paulovitorbal/coruja_gps/revisao_tecnica.md

# 🔍 Revisão Técnica — Pontos que Necessitam Correção

**Projeto:** Detector de Radares GPS Inteligente (Raspberry Pi Pico 2 W)
**Documentos revisados:** `bom_schematic.md`, `requirements.md`
**Data da revisão:** 2026-09-15
**Contexto:** projeto pessoal de estudo — aperfeiçoamento de habilidades em embarcados.

## Sumário por severidade

> ✅ **2026-09-15 — Revisão 2 aplicada aos documentos de origem.** `requirements.md` e
> `bom_schematic.md` foram atualizados com todos os itens abaixo. Os originais estão em
> `requirements.md.bak` e `bom_schematic.md.bak`. O que resta não é mais *documentar* —
> é **implementar, medir e confirmar as suposições**.

| Severidade | Documentado | Pendente de bancada | Significado |
| :--- | :---: | :---: | :--- |
| 🔴 **Bloqueador** | 8 de 8 | — *(R-05 medido em 19/09)* | Queima componente, ou o requisito não roda no hardware. R-05, R-06, R-14 e R-21 fechados. |
| 🟠 **Relevante** | 28 de 28 | 2 medições (R-13, R-17) + 2 inspeções (display, serigrafia do GPS) + 1 julgamento subjetivo (R-32, audibilidade) | Circuito liga, comportamento sai errado ou falha em silêncio. **R-22 a R-26**. |
| 🟡 **Lacuna** | 9 de 9 | — | Requisito que não existia. |
| ⚪ **Editorial** | 5 de 5 | — | Erro de texto ou numeração. |

### ⏳ O que continua aberto

**📐 Medições de bancada** — as únicas coisas que exigem o hardware na mão:

| Item | O que medir | Por quê |
| :--- | :--- | :--- |
| ~~**R-05**~~ | ✅ **CONCLUÍDO em duas partes.** LED em 2026-09-19: resistores 330/470/150 Ω, âmbar 19,6% de verde, rosa 15,7% de azul. **Tela em 2026-09-29:** as três matizes se distinguem a 5%, mas a barra some por falta de área — piso físico sobe de 5% para 10%, e a escala exposta passa a 0–100% com o piso escondido. **Reverificado:** a 0% da escala nova o texto continua legível no escuro e a barra é fácil de ver | Critério do RF03.4 atendido no LED. Na tela, a paleta passou, o piso de brilho não — e o piso corrigido passou na reverificação. |
| **R-13** | Corrente agregada no `3V3_OUT` com backlight em 100% | Com o GPS migrado para 5 V (R-14), sobraram display e SD — margem provavelmente confortável, mas não verificada. |
| **R-17** | Consumo do buzzer e pinagem do BC337/2N2222 | A ordem E-B-C difere da do BC547. ⚠️ **Esperado ~10 mA no SFM-20B**, não 20–50 mA como dizia a rev. 2 da folha de bancada — aquele número era do SFM-27 (R-32). |

**🔍 Inspeção antes de energizar:**

| Item | Verificação |
| :--- | :--- |
| ~~**R-14**~~ | ✅ **CONFIRMADO em 2026-10-04.** Regulador presente: SOT-23-**5** marcado `LB2k` — não 3 pinos, como esta linha supunha. Medido com fonte de bancada a 3,3 V: `VCC` 3,29 V, saída 3,19 V no **pino 4**, consumo **42 mA**. A queda de 0,10 V a 42 mA são 2,4 Ω equivalentes; trilha cai microvolts. **5 V liberados.** |

**❓ Decisões de produto — não bloqueiam nada:**

| Item | Decisão |
| :--- | :--- |

**🔜 Escopo futuro, fora desta versão:**

| Item | Escopo |
| :--- | :--- |
| **RF03.10** | Controle de velocidade média em trecho. Desenho completo registrado. |
| **Telas e interfaces visuais** | Sessão dedicada. Inclui a distinção visual de radar móvel do RF03.5 e todos os estados que migraram para a tela no R-25. |

**🔨 Todo o resto é implementar.** Ver ordem de ataque abaixo.

### ✅ Decisões fechadas pelo autor

| Item | Decisão | Data |
| :--- | :--- | :--- |
| **RF03.6** | **Limiar de multa com margem de segurança:** desconto de projeto de 6 km/h (≤100) e 5% (>100), contra os valores legais de 7 km/h e 7% confirmados na Resolução CONTRAN. | 2026-09-15 |
| **RF03.7** | **Buzzer escalonado em 3 faixas** na Zona de Perigo (lento / rápido / contínuo). | 2026-09-15 |
| **RF03.9** | **Rosa piscante a 1 Hz** entre o limite da via e `V_infra` — silencioso. Rosa (R+B) em vez de laranja (R+G): separação por canal, não por razão. | 2026-09-15 |
| **RF03.4** | **Precedência: Perigo > Margem > Semáforo > Conforme.** | 2026-09-15 |
| **RF03.5** | **`TYPE=5` como radar simples** + sinal de alerta na tela. Média diferida. | 2026-09-15 |
| **RF06.1** | **Categorias exportadas: `1,2,4,5`** (Radar Fixo, Radar Móvel, Semáforo c/ Câmera, Semáforo c/ Radar). Fora do escopo: Polícia Rodoviária, Pedágio e **Lombada** — esta última, com 19.351 pontos, levaria a base a 37.645 registros e estouraria o RNF07. | 2026-09-16 |
| **R-25** | **LED RGB exclusivo de estado de via** — boot, sem sinal, OTA e falha de dados só na tela. **LED verde de Wi-Fi removido do projeto**; LED RGB é o único indicador luminoso. | 2026-09-15 |
| **RF03.8** | **Zona de Aproximação silenciosa** — buzzer exclusivo da Zona de Perigo. | 2026-09-15 |
| **L-08** | **C++17 com Pico SDK** — dual core real e orçamento de memória. Teste de heap do MicroPython dispensado. | 2026-09-15 |
| **R-06** | **Conector JST-XH** de 2 vias no lugar do Jack P2. | 2026-09-15 |
| **R-14** | **GPS alimentado em 5 V** — placa GY-GPS6MV2-NEO M8N tem LDO embarcado. | 2026-09-15 |
| **R-19** | **Zona de Semáforo silenciosa**, LED amarelo/vermelho alternando a 2 Hz. | 2026-09-15 |
| **R-21** | **GPS+GLONASS a 4 Hz nominal, piso de 3 Hz.** Gerou o RF01.5. | 2026-09-15 |

### ⚠️ Correções de pinagem física (2026-09-17)

Com os módulos em mãos, duas pinagens dos documentos estavam erradas. Ambas vieram de
inferência minha, não de leitura da peça.

| Módulo | Documento (rev. 2) | Placa física | Consequência se soldado |
| :--- | :--- | :--- | :--- |
| **KY-040** | `CLK DT SW + GND` | **`GND + SW DT CLK`** | **ordem invertida** — 3,3 V e GND direto em dois GPIO |
| **Leitor SD** | 6 pinos `VCC GND CLK DI DO CS` | **8 pinos** `3V GND CLK DO/SO CMD/SI D3/CS DAT2 DET` | rótulos inventados; 2 pinos inexistentes no meu mapa |

Lição registrada: rótulo de serigrafia é dado, não dedução. Os documentos passaram a
usar os nomes impressos na placa, porque na bancada se lê a placa.

### 🆕 Card detect aproveitado (2026-09-17)

O pino `DET` do leitor SD, que eu nem sabia existir, foi ligado ao **GPIO 14** — livre
desde que o LED de Wi-Fi saiu (R-25). Permite ao RF07 distinguir **cartão ausente**, que
o motorista resolve inserindo o cartão, de **cartão ilegível**, que ele não resolve
dirigindo. Antes eram a mesma mensagem.

Custo zero em componentes: **a própria placa traz o pull-up de 4,7 kΩ para 3 V**, então
o GPIO 14 é entrada **sem pull** — o interno do Pico, que eu havia recomendado, seria
redundante e mais fraco.

A polaridade **não é incógnita de bancada**: o guia do fabricante documenta que o `DET`
fica em GND sem cartão e sobe a 3 V quando há cartão, logo **cartão presente = nível
ALTO**. Fica uma ressalva no RNF03: o `DET` é **indício, não autoridade** — a tentativa
de leitura continua sendo o veredito.

### Histórico de resoluções

| Data | Itens | Documento de solução | Observação |
| :--- | :--- | :--- | :--- |
| 2026-09-15 | **R-02** | `formato_dados.md` §1 | Premissa corrigida: base real tem 18.294 pontos, não 40–60 mil. Cabe em RAM; particionamento desnecessário. |
| 2026-09-15 | **R-03** | `formato_dados.md` §4 | Array ordenado por latitude + busca binária + pré-filtro inteiro. Custo medido: máx. 24 Haversines/ciclo. |
| 2026-09-15 | **R-18** | `formato_dados.md` §0 + `converte.py` | Layout confirmado por cabeçalho do arquivo; `DirType` confirmado por análise geométrica; conversor escrito e verificado. |
| 2026-09-15 | **R-19** *(parcial)* | `formato_dados.md` §7.1 | Comportamento decidido pelo autor: Zona de Semáforo silenciosa, LED amarelo/vermelho a 2 Hz. Implementação pendente e dependente do R-05. |
| 2026-09-15 | **L-08** | `requirements.md` RNF06 | **C++17 com Pico SDK decidido pelo autor.** Dual core real e orçamento de memória. Teste de heap do MicroPython dispensado. |
| 2026-09-15 | **TODOS** | `requirements.md` rev. 2 + `bom_schematic.md` rev. 2 | Os 34 itens aplicados aos documentos de origem, com tabelas de rastreabilidade em cada um. Originais preservados em `.bak`. |
| 2026-09-15 | **R-06** | `bom_schematic.md` §5 + `requirements.md` RNF05 | **Conector JST-XH confirmado pelo autor** em lugar do Jack P2. Suposição fechada. |
| 2026-09-15 | **R-14** *(reformulado)* | `bom_schematic.md` §3 | Faixa do chip (2,7–3,6 V) informada pelo autor revelou que a suposição de 3,3 V era mal fundamentada. Virou árvore de decisão por regulador da placa. |
| 2026-09-15 | **R-14** | `bom_schematic.md` §3 | **5 V decidido.** Placa identificada como GY-GPS6MV2-NEO M8N, família com LDO embarcado — alimentar em 5 V é a configuração de projeto da placa, funciona com qualquer LDO e alivia ~82 mA do regulador do Pico. |
| 2026-09-15 | **R-21, R-22** *(novos)* | `revisao_tecnica.md` | Datasheet oficial UBX-15031086 analisado. Teto de 5 Hz em GPS+GLONASS e faixa de entrada dos GPIO do GPS. Correntes, temperatura e config padrão agora ancoradas em datasheet. |
| 2026-09-16 | **R-20** *(resolvido)* e **R-26** | `formato_dados.md` §0.2 · `requirements.md` RF03.5/RF03.10 | Significado real dos códigos `TYPE` obtido da fonte da base: as contagens batem na unidade. **Minhas duas inferências de rótulo estavam erradas** — `TYPE=2` é semáforo com radar e `TYPE=5` é radar móvel. RF03.10 anulado por falta de dados. |
| 2026-09-15 | **R-20** *(corrigido)* + **R-25** *(novo)* | `requirements.md` RF03.5, RF03.9, RF03.10 | Teste de pareamento de `TYPE=5` refeito após erro de método meu — evidência é mista, não negativa. Requisito mantido pelo autor; média diferida por ausência de trechos no DF (5 pontos). Paleta do LED reduzida de 9 para 5 estados. |
| 2026-09-15 | **R-23** *(novo)* | `requirements.md` RF03.6 a RF03.8 | Tolerância legal e buzzer escalonado especificados pelo autor. A ancoragem literal dos percentuais no limite da via deixaria as faixas vazias em 82,5% dos radares; reancorada em `V_infra`. Aproximação silenciada. |
| 2026-10-04 | **R-14** *(fechado)* | `revisao_tecnica.md` · `bom_schematic.md` §3 | Regulador da placa GPS **confirmado por medição**: SOT-23-5 marcado `LB2k`, 3,29 V na entrada e **3,19 V na saída** a 42 mA. Queda de 0,10 V nessa corrente só vem de elemento ativo em série. **5 V liberados.** A marcação não identificou a peça e a pinagem típica de datasheet errou o pino de saída — resolveu-se medindo. |
| 2026-10-03 | **R-67** *(novo)* | `bom_schematic.md` item 10 · `roteiro_bancada.html` §02 | Procedimento de bancada mandava tentar as duas orientações do transistor "sem risco a 5 V" — mas o **ADR 0009 levou o buzzer para 12 V** em setembro, e invertido isso aplica o dobro do `V_EBO` na junção base-emissor. Degrada o hFE sem o dano aparecer. Substituído por **teste de ruptura reversa**, que não depende de ganho. Pinagem desta peça MEDIDA: `2N2222 / A331`, NPN, **E-B-C** com a face chata para o observador. |
| 2026-10-01 | **R-66** *(novo)* · **ADR 0011** | `bom_schematic.md` item 2 · `docs/adr/0011` · `montagem.md` §0 | Conector da antena medido a paquímetro: **U.FL de ~2 mm com rabicho de 8 cm**, não SMA. Terceira divergência BOM × peça no mesmo dia, e as duas últimas me fizeram propor arranjos impossíveis. **ADR 0011:** monta-se com o que já existe e as mitigações do R-65 são contingentes a medição — o gatilho é observar problema, não concluir que seriam boa ideia. |
| 2026-10-01 | **R-65** *(novo)* | `requirements.md` RNF09 · `montagem.md` §4 | Painel ao sol medido em **92 °C** (infravermelho, São Paulo, 5 h) contra os "ultrapassa 60 °C" do requisito. O NEO-M8N fica **7 °C fora da faixa de ARMAZENAMENTO** — o aparelho desligado já está fora de especificação. Remoção ao estacionar vetada pelo autor por contrariar a premissa do produto. Mitigado por montagem: prateleira migra da tampa para o chassi. |
| 2026-09-15 | **R-21** | `requirements.md` RF01.4 + RF01.5 | **4 Hz nominal com piso de 3 Hz confirmado pelo autor.** A banda de tolerância gerou requisito novo de monitoramento da taxa efetiva — que serve primariamente como verificação de que a configuração UBX do RF01.2 foi aplicada. |

## Legenda de confiança da evidência

| Marca | Origem |
| :--- | :--- |
| ✅ **Verificado** | Confirmado contra pinout oficial do Raspberry Pi Pico 2 / formato de dados / especificação citada. |
| ⚠️ **Valor típico** | Valor típico de datasheet. **Medir com a peça real** — e aqui medir é parte do exercício: multímetro no LED e no buzzer ensina mais que aceitar o número. |
| ❓ **A confirmar** | Precisa de consulta ao datasheet do fornecedor específico. |

## Ordem sugerida de ataque

Os requisitos já estão escritos. Esta é a ordem de **construção**, priorizada por valor
didático e por dependência:

1. **Bancada, antes de soldar** — as três medições pendentes (R-05, R-13, R-17). São
   rápidas, se resolvem com multímetro e datasheet, e custam componente queimado se
   descobertas depois. O R-05 é o mais urgente: sem o canal verde funcionando, a Zona de
   Semáforo que você decidiu não tem como ser validada.
2. **Fechar as duas decisões de produto restantes** — RF03.4 (prioridade entre alertas
   simultâneos) e RF03.5 (distinção visual de radar móvel). Podem esperar o aparelho
   rodando; não bloqueiam nada. *(R-06, conector JST-XH, confirmado em 2026-09-15.)*
3. **Parser NMEA e matemática geográfica** (RF01, RF02) — o núcleo, e o melhor terreno
   para os testes do RNF10: vetores conhecidos, zero hardware na mesa. O wraparound
   355°/5° e os três valores de `DirType` são os casos de teste obrigatórios. O
   `radares.bin` já gerado serve de *fixture*.
4. **Carregador da base e busca em dois estágios** (RF06, RF02.1) — continua sendo a
   parte mais interessante do projeto: é onde restrição real de memória e CPU força
   decisões de estrutura de dados. Especificação pronta em `formato_dados.md` §2 e §4.
5. **Máquina de estados de zona** (RF03, RF07) — as quatro zonas, histerese, condição de
   aproximação, prioridade entre alertas e degradação segura. É aqui que a Zona de
   Semáforo vive.
6. **Concorrência entre núcleos** (RNF04) — divisão core 0 / core 1 e mutex do SPI0.
   Deixar para depois de a lógica estar correta em um único núcleo.
7. **OTA** (RF05) — por último: subsistema mais independente e o projeto já é útil sem
   ele. Escrita atômica e validação já especificadas.

---

---

# 🔴 Bloqueadores

## R-01 — `VBUS` não é o pino 39, e não deve ser o nó de entrada

- **Onde:** `bom_schematic.md` seções 1 e 5; `requirements.md` RNF01
- **Confiança:** ✅ Verificado (pinout oficial Pico / Pico 2)

**Problema.** O documento roteia o carregador veicular e os dois capacitores de filtro
para "VBUS (Pino 39)". No pinout real: pino 39 = `VSYS`, pino 40 = `VBUS`, pino 38 = `GND`.
O rótulo está trocado. Além do erro de nome, `VBUS` é ligado diretamente ao conector
USB do Pico — injetar 5V externo nesse nó cria conflito de fontes se o USB for plugado
para debug ou regravação.

**Correção.** Entrada 5V → diodo Schottky em série → `VSYS` (pino 39), com o par de
capacitores nesse nó, o mais próximo possível fisicamente dos pinos 39/38.

**Impacto propagado.** Atualizar também:
- Seção 5 do BOM: a linha de 5V do Jack do buzzer passa a vir de `VSYS` (ou do 5V
  pré-regulador, antes do Schottky).
- RNF01: trocar a menção a `VBUS` pelo nó correto.
- Seção 3 do BOM: a opção de alimentar o GPS em 5V muda de nó.

---

## ~~R-02 — A base de radares não cabe na SRAM~~ → ✅ **RESOLVIDO: premissa corrigida**

- **Onde:** `requirements.md` §5 (tela de boot: "Lê o SD e carrega dados na RAM")
- **Solução registrada em:** `formato_dados.md` §1
- **Resolvido em:** 2026-09-15

**Este achado estava errado.** Eu o levantei sobre uma estimativa de 40–60 mil pontos
na base brasileira. O número real, informado pelo autor, é de **18.294 pontos** — 3×
menor. Recalculando:

```
18.294 registros × 12 bytes = 214 KB   de 520 KB de SRAM
```

**A base inteira cabe na RAM.** O requisito original do §5 ("Lê o SD e carrega dados na
RAM") estava correto como escrito, e o particionamento em quadrantes que eu recomendei
é complexidade desnecessária: índice espacial, margem sobreposta, prefetch, histerese
de fronteira e duplo buffer são cinco mecanismos que não precisam existir.

Ganhos colaterais da carga integral: **nenhum acesso a SD com o veículo em movimento**,
e falha de cartão em movimento passa a ser irrelevante.

**O que sobrou de real deste achado** — dois pontos que valem independentemente:

1. **O framebuffer do display consome 150 KB** (320 × 240 × 2 B), quase o que a base
   inteira consome, e não aparecia em nenhum documento. É o maior alvo de otimização se a
   memória apertar (renderização em bandas libera **125 KB**). Ver `formato_dados.md` §6.
   *Número atualizado em 2026-09-17: o painel passou de 1,3" 240×240 para 2,4" 320×240,
   e com ele o framebuffer de 112,5 para 150 KB.*
2. **O orçamento de memória continua precisando ser escrito** como requisito, agora com
   números reais em vez de estimativas. Ver **L-02**.

O desenho de particionamento está preservado em `formato_dados.md` Anexo A, como plano
B para o caso de a base passar de ~35.000 registros.

---

## ~~R-03 — Haversine contra a base inteira a 5 Hz~~ → ✅ **RESOLVIDO**

- **Onde:** `requirements.md` RF02
- **Solução registrada em:** `formato_dados.md` §4
- **Resolvido em:** 2026-09-15

O achado era válido: 18.294 pontos × 5 Hz × Haversine em dupla precisão não executa em
tempo real. A solução não dependia do particionamento e sobreviveu à revisão do R-02.

**Solução: array ordenado por latitude + busca em dois estágios.**

1. **Busca binária** pela faixa de latitude `[lat − 300 m, lat + 300 m]` — ~15
   comparações de inteiros.
2. **Varredura da faixa** com descarte por longitude em aritmética inteira, sem
   trigonometria.
3. **Haversine apenas nos sobreviventes** — unidades por ciclo, não milhares.

Ordenar por **latitude** e não longitude é deliberado: o grau de latitude mede 111,32 km
em qualquer ponto do globo, então o limiar da busca binária é constante. Em longitude ele
dependeria de cos(lat) e o índice ficaria distorcido de norte a sul do país.

A invariante de ordenação é validada no carregamento (ver R-10 e `formato_dados.md` §2):
se o arquivo vier desordenado, a busca binária erra silenciosamente.

---

## R-04 — Filtro de rumo com bug de wraparound em 0°/360°

- **Onde:** `requirements.md` RF02, "Filtro de Sentido (Rumo)"
- **Confiança:** ✅ Verificado (aritmética circular + dados reais da base)
- **Código pronto em:** `formato_dados.md` §3.2

**Problema.** O requisito diz "se a diferença absoluta for maior que 30°, o radar deve
ser ignorado". Entre rumo 355° e radar 5° a diferença aritmética é 350° → o radar
**correto** é descartado. São três defeitos no mesmo requisito:

1. **Wraparound.** Usar diferença circular: `min(|a−b|, 360−|a−b|)`.
2. **Rumo inválido a baixa velocidade.** O azimute do NEO-M8N é ruído aleatório com o
   veículo parado ou abaixo de ~5 km/h. O filtro precisa de porta de velocidade — e
   abaixo do limiar ele deve **abrir**, não fechar: descartar por um rumo que é ruído
   perderia radares reais.
3. **O requisito só contempla o caso unidirecional**, que é 83,2% da base. Os outros
   dois casos, confirmados nos dados (ver R-18), precisam de tratamento próprio:
   - **`DirType=0`, omnidirecional — 1.419 registros (7,8%):** nunca podem ser
     descartados pelo filtro de rumo.
   - **`DirType=2`, bidirecional — 1.657 registros (9,1%):** válidos no rumo indicado
     **e no oposto**. Resolve-se com uma diferença circular dobrada em 0–90° em vez de
     0–180°, sem caso especial no laço.

> ⚠️ **Correção de uma suposição minha anterior:** eu havia afirmado que o sentinela de
> omnidirecional seria `Direction = 0`. **Está errado** — o `Direction` vem preenchido
> mesmo quando `DirType = 0`. O sentinela é o campo `DirType`. Se você tinha anotado a
> versão anterior, descarte.

---

## ~~R-05 — 330 Ω deixa o verde e o azul do LED RGB praticamente invisíveis~~ → ✅ **MEDIDO: a previsão estava errada**

- **Onde:** `bom_schematic.md` itens 10 e 11, seção 4
- **Confiança:** ✅ **Medido na bancada em 2026-09-19**, com fonte de 3,3 V e julgamento
  sob **luz solar direta**, que é o pior caso de visibilidade
- **Status:** ✅ **FECHADO** — sem alteração de BOM

**O que este achado afirmava.** Que LEDs difusos verde e azul têm `Vf` de 3,0 a 3,2 V,
que com 330 Ω sobrariam ~0,1 V no resistor, menos de 1 mA, e que os dois canais ficariam
**praticamente invisíveis** — tornando o amarelo do R-19 e o rosa do RF03.9 impossíveis.
A correção proposta era baixar verde e azul para **47 a 100 Ω**.

**O que a medição encontrou.**

| Canal | Resistor escolhido | O achado previa |
| :--- | ---: | ---: |
| Vermelho | 330 Ω | 330 Ω ✅ |
| **Verde** | **470 Ω** | 47–100 Ω ❌ |
| **Azul** | **150 Ω** | 47–100 Ω ❌ |

O verde precisou do **maior** resistor dos três, não do menor. A previsão errou o sinal,
não só a magnitude.

**Por que errou.** O raciocínio olhava exclusivamente o lado **elétrico** — `Vf` contra o
trilho — e ignorou o lado **fotométrico**. A sensibilidade do olho humano tem pico no
verde, e a ordem dos resistores medidos é **exatamente o inverso** da ordem de
sensibilidade:

| Canal | Resistor | Sensibilidade relativa do olho |
| :--- | ---: | ---: |
| Verde ~555 nm | **470 Ω** | **1,00** |
| Vermelho ~630 nm | 330 Ω | 0,27 |
| Azul ~470 nm | **150 Ω** | **0,09** |

A 1 mA o verde parece cerca de **11× mais brilhante** que o azul de mesma corrente.
Dimensionar canal de LED colorido só pela corrente supõe que o olho é plano em
frequência, e ele não é — é a suposição que estava escondida no achado.

**O que se fecha.**

* **Nenhum componente novo.** A contingência — trocar o LED ou acionar verde e azul pelos
  5 V com um transistor por canal — não é necessária. Era o único item que podia fazer o
  BOM crescer.
* **R-19 e RF03.9 destravados.** Há verde suficiente para compor o amarelo da Zona de
  Semáforo e azul para o rosa da faixa de margem.
* **Alívio para o R-13.** Somados, os três canais contribuem com poucos miliampères no
  trilho de 3V3.
* Os **68 Ω comprados** antes da medição ficam de sobra. Os 150 Ω e 470 Ω saem do estoque.

**Calibração de PWM concluída em 2026-09-19**, com o modo de calibração na placa:

| Cor | Composição | Razão |
| :--- | :--- | ---: |
| **Âmbar** | `rgb(255, 50, 0)` | 19,6% de verde |
| **Rosa** | `rgb(255, 0, 40)` | 15,7% de azul |

Os dois canais secundários precisam de **muito pouco**. Os nominais que este documento
propunha — 45% e 60% — estavam errados por **2,3× e 3,8×**, e teriam produzido um amarelo
esverdeado e um rosa lavado, quase lilás. Mesma origem do erro dos resistores: estimativa
fotométrica feita de cabeça.

✅ **Critério do RF03.4 atendido**, confirmado pelo autor: o rosa é inconfundível em
relação ao vermelho, e o âmbar sai âmbar claro. Os quatro estados de via — verde, âmbar,
rosa, vermelho — são distinguíveis.

**Duas ressalvas sobre a medição.**

1. Foi com **fonte de bancada ligada direto ao LED**, a 3,30 V. No circuito final o ânodo
   comum fica no `3V3_OUT` e o **GPIO drena**, com `Vol` de ~0,2 V: sobram ~3,10 V, cerca
   de **7% menos corrente**. Imperceptível, mas os valores não são idênticos.
2. **`Vf` não foi anotado**, então as correntes por canal são estimativa. Para o R-13
   basta; se o orçamento do trilho apertar, vale medir.

---

## R-06 — O Jack J2 de 3,5 mm curto-circuita 5V no GND durante a inserção

- **Onde:** `bom_schematic.md` seção 5, itens 16 e 17; `requirements.md` RNF05
- **Confiança:** ✅ Verificado (geometria de conector P2)

**Problema.** Do jeito roteado (tip = 5V, sleeve = coletor do BC547), inserir ou remover
o plugue faz o sleeve varrer o tip. Se o transistor estiver conduzindo nesse instante,
resulta em curto direto do trilho de 5V para o GND, **sem o buzzer limitando a corrente** —
risco de dano ao transistor e ao carregador veicular. Conector P2/P3 de áudio para
energia é antipadrão conhecido justamente por isso.

**Correção (em ordem de preferência).**
1. Trocar por conector polarizado sem wiping — JST-XH ou Molex de 2 vias. *Recomendado:*
   preserva o requisito de liberação rápida do RNF05 sem o modo de falha.
2. Se o P2 for mandatório por restrição mecânica: inverter os nós (5V no sleeve) e
   adicionar PTC rearmável ou fusível na perna de 5V do jack.

---

## ~~R-21 — 5 Hz é exatamente o teto do NEO-M8N~~ → ✅ **RESOLVIDO**

- **Onde:** `requirements.md` RF01, RF01.4, RF01.5
- **Confiança:** ✅ **Verificado no datasheet oficial** (UBX-15031086, Tabela 1, p. 6)
- **Decisão do autor:** 2026-09-15 — **GPS+GLONASS a 4 Hz nominal, piso de 3 Hz**

> ✅ **Resolvido.** O autor optou por banda de tolerância em vez de ponto único, o que é
> mais robusto: 4 Hz nominal com 20% de folga sob o teto, e 3 Hz como piso aceitável.
> O custo do piso é de no máximo um período de amostragem de antecedência — 333 ms, ou
> 11 m dos 300 m de raio a 120 km/h.
>
> **Consequência que gerou requisito novo:** definir um piso só tem valor se o sistema
> souber quando o cruzou. Daí o **RF01.5** (monitoramento da taxa efetiva), que na
> prática funciona como verificação de que a configuração UBX do RF01.2 foi aplicada —
> taxa abaixo do nominal quase nunca é o receptor com dificuldade, é a configuração que
> não pegou.

**Problema.** O RF01 exige "taxa de amostragem mínima de 5 Hz". A Tabela 1 do datasheet
traz a taxa máxima de navegação do NEO-M8N por modo de GNSS:

| Modo GNSS | Taxa máx. | Precisão horiz. | Cold start | Sensib. (tracking) | Talker NMEA |
| :--- | :---: | :--- | :---: | :---: | :---: |
| **GPS + GLONASS** *(padrão de fábrica)* | **5 Hz** | 2,5 m · 2,0 m c/ SBAS | 26 s | −167 dBm | `$GNRMC` |
| **GPS apenas** | **10 Hz** | 2,5 m · 2,0 m c/ SBAS | 29 s | −166 dBm | `$GPRMC` |
| GLONASS apenas | 10 Hz | 4 m | 30 s | −166 dBm | `$GLRMC` |
| BeiDou | 10 Hz | 3 m | 34 s | −160 dBm | — |
| Galileo | 10 Hz | 3 m | 45 s | −159 dBm | — |

O módulo sai de fábrica em **recepção concorrente de GPS + GLONASS**, modo em que o teto
é **exatamente 5 Hz**. O requisito não tem **nenhuma folga**: qualquer degradação —
temperatura, sinal fraco, muitos satélites rastreados — e a taxa efetiva cai abaixo do
que o RF01 exige, sem aviso.

**O dado mais útil da tabela:** GPS-apenas tem **precisão horizontal idêntica** à
concorrente (2,5 m, 2,0 m com SBAS). O que se perde são 3 s de cold start, 1 dBm de
sensibilidade e a disponibilidade extra de satélites — que importa em cânion urbano,
justamente onde os radares estão.

**Vale reexaminar o próprio 5 Hz.** A 100 km/h (27,8 m/s), o deslocamento por amostra é:

| Taxa | Deslocamento/amostra a 100 km/h |
| :---: | :--- |
| 5 Hz | 5,6 m |
| 4 Hz | 6,9 m |
| 2 Hz | 13,9 m |

Contra um raio de alerta de **300 m**, mesmo 2 Hz daria granularidade de 14 m — 4,6% do
raio. O 5 Hz é generoso, não apertado.

**Três configurações viáveis:**

| Opção | Configuração | Folga | Custo |
| :---: | :--- | :--- | :--- |
| **a** | GPS+GLONASS @ 5 Hz | **nenhuma** | — |
| **b** | GPS apenas @ 5 Hz | 2× | +3 s cold start, −1 dBm, menos satélites em cânion urbano |
| **c** ⭐ | GPS+GLONASS @ 4 Hz | 20% | 6,9 m/amostra em vez de 5,6 m |

**Recomendação: opção (c).** Mantém a disponibilidade multiconstelação, que é o ativo
real em cidade, e compra 20% de folga trocando 1,3 m de granularidade que o raio de
300 m absorve sem notar. Exige relaxar o RF01 de 5 Hz para 4 Hz.

> **Fecha o R-08 por outro caminho:** a escolha de modo determina o talker NMEA —
> `$GNRMC` em concorrente, `$GPRMC` em GPS-apenas. Aceitar os dois, como o R-08 já
> exigia, deixa o firmware indiferente a esta decisão e permite mudá-la sem tocar no
> parser.

---

> ℹ️ **Não existe R-27.** O número foi pulado na numeração original e nunca ocupado.

## R-28 — Conector permutável com 12 V destrói o aparelho

- **Onde:** `bom_schematic.md` seção 0; BOM itens 18, 19 e 22
- **Confiança:** ✅ Verificado por análise do circuito
- **Origem:** revisão do autor em 2026-09-17
- **Resolvido em:** mesma data, com o perigo reposicionado

**Problema.** Um plugue de **12 V** que encaixe na entrada do aparelho injeta 12 V no nó
`VSYS`, cujo máximo absoluto é **5,5 V**. Pico, GPS, display e cartão saem juntos. O
erro é fácil: dois plugues iguais, sob o painel, no escuro.

### O perigo mudou de lugar duas vezes

| Arranjo | Onde estava o risco |
| :--- | :--- |
| Conversor **dentro** do gabinete | Nos **dois conectores do aparelho**: a entrada trazia 12 V e o buzzer trazia `VSYS`. Trocar destruía tudo. |
| Conversor **fora** *(decisão final)* | Nos **dois cabos externos**: 12 V (piggyback → conversor) e 5 V (conversor → gabinete). |

Com o conversor fora, a entrada do aparelho passou a ser 5 V, então **trocar os dois
conectores do aparelho deixou de ser destrutivo** — o pior caso é o buzzer tocar sozinho
ou o aparelho não ligar.

Mas o risco não desapareceu: migrou para o cabo de 12 V, que agora existe do lado de
fora e pode encaixar na entrada do gabinete.

### Correções aplicadas

1. **O trecho de 12 V não usa JST-XH.** Preferência: ligar direto aos terminais do
   conversor, sem conector — não existindo plugue de 12 V, não há o que trocar. Se
   houver conector, família diferente (VH, faston).
2. **Entrada do aparelho com 3 vias**, pino central sem uso, contra as 2 do buzzer.
   Agora é medida de **robustez**, não de segurança: evita duas formas de perder tempo
   depurando, ao mesmo custo.

Achado do autor, não meu: eu especifiquei os dois conectores sem notar que se tornaram
permutáveis quando a entrada deixou de ser 5 V, e teria mantido o erro se ele não
tivesse pedido a revisão.

---

# 🟠 Pontos relevantes

## R-07 — RF01 (5 Hz) exige configuração UBX não especificada

- **Onde:** `requirements.md` RF01
- **Confiança:** ✅ Verificado (comportamento padrão de fábrica u-blox M8)

**Problema.** O NEO-M8N sai de fábrica em **1 Hz e 9600 bps**. A 9600 bps o conjunto NMEA
padrão a 5 Hz não cabe na banda → frames truncados. O requisito pede a taxa mas não
especifica como obtê-la.

**Correção.** Acrescentar ao RF01 a sequência de configuração obrigatória:
- `CFG-RATE` → 200 ms.
- `CFG-PRT` → 38400 ou 115200 bps.
- `CFG-MSG` → desabilitar todas as sentenças exceto RMC.
- `CFG-CFG` → persistir em BBR/flash **e** reenviar a cada boot (o módulo perde a
  configuração se a bateria de backup estiver descarregada).

---

## R-08 — `$GNRMC` vs `$GPRMC`

- **Onde:** `requirements.md` RF01
- **Confiança:** ✅ Verificado (padrão NMEA: talker ID)

**Problema.** RF01 fixa `$GNRMC`. O talker `GN` só aparece com multi-GNSS ativo; em modo
GPS-only a sentença vira `$GPRMC` e o parser não casa nada — falha silenciosa total.

**Correção.** Aceitar ambos os talkers. Acrescentar também requisito de **validação de
checksum NMEA**, hoje ausente dos dois documentos.

---

## R-09 — As zonas de alerta não saem depois de passar pelo radar

- **Onde:** `requirements.md` RF03; §5 (fluxo de telas); matriz IHM
- **Confiança:** ✅ Verificado (análise lógica do requisito)

**Problema.** RF03 define as zonas apenas por `distância ≤ 300 m`. Ao passar pelo radar
a distância volta a crescer, mas permanece ≤ 300 m por vários segundos: o alerta continua
ativo e, na Zona de Perigo, o buzzer "metralhadora" segue tocando **depois** de já ter
passado o radar. Dois defeitos:

1. **Falta condição de aproximação.** Comparar o azimute veículo→radar com o rumo do
   veículo (alvo à frente), ou exigir distância decrescente entre amostras.
2. **Falta histerese no limiar de 300 m.** Sem ela, os "2 bipes curtos apenas no momento
   da entrada da zona" re-disparam em loop quando a distância oscila na fronteira.

**Consideração adicional.** Raio fixo de 300 m dá ~10,8 s de antecedência a 100 km/h e
~21,6 s a 50 km/h. Avaliar raio proporcional à velocidade.

---

## R-10 — OTA sem integridade, escrita atômica ou rollback

- **Onde:** `requirements.md` RF05; matriz IHM (linha "Fim do download / Falha no Timeout")
- **Confiança:** ✅ Verificado (análise do requisito)

**Problema.** RF05 salva o arquivo baixado "diretamente no cartão SD". Queda de energia
(motorista desliga o carro), timeout ou arquivo remoto vazio deixam a base corrompida e
o dispositivo sem alertas — falha perigosa e silenciosa, já que a tela volta ao
velocímetro normalmente.

**Correção.** Especificar no RF05:
- Baixar para `speedcam.tmp`.
- Validar: tamanho mínimo, contagem de linhas parseáveis, hash conferido contra a origem.
- Só então renomear sobre o original, preservando `speedcam.bak` da versão anterior.
- Rollback automático para `.bak` se a validação falhar.
- Definir **timeout**, **número de tentativas** e comportamento explícito para
  arquivo remoto vazio ou HTTP != 200.

---

## R-11 — Credenciais de Wi-Fi não especificadas e não devem ir no firmware

- **Onde:** `requirements.md` RF05 ("conectar ao ponto de acesso configurado" — sem definir onde)
- **Confiança:** ✅ Verificado (política de segurança da informação aplicável)

**Problema.** O requisito pressupõe um AP "configurado" mas não define o mecanismo.
Credenciais embutidas no firmware violam a política de não manter segredos em código.

**Correção.** Escrever requisito explícito:
- Credenciais em arquivo de configuração no SD (ex. `wifi.cfg`), lido em runtime.
- Tratar o cartão SD como mídia que circula fora do laboratório — não versionar o
  arquivo de credenciais, não usar rede corporativa para o AP de atualização.
- Download por HTTPS ou com verificação de assinatura na origem.

---

## R-12 — Suspender o GPS durante o OTA é risco de uso em movimento

- **Onde:** `requirements.md` RF05
- **Confiança:** ✅ Verificado (análise do requisito)

**Problema.** RF05 "suspende temporariamente a leitura do GPS" ao detectar o clique.
O eixo do encoder é fácil de pressionar sem intenção. Se isso ocorrer em movimento, o
motorista fica sem alerta por tempo indeterminado, e a matriz IHM mostra apenas
"Atualizando base de dados..." — sem indicação de que a proteção está desativada.

**Correção.** Condicionar a entrada em OTA a veículo parado (velocidade < 3 km/h por
N segundos consecutivos), ou exigir confirmação em duas etapas. Definir também timeout
máximo global do modo OTA com retorno automático ao velocímetro.

---

## R-13 — Orçamento de corrente do trilho `3V3_OUT` não foi calculado

- **Onde:** `bom_schematic.md` seções 2, 3 e 4
- **Confiança:** ⚠️ Valores típicos — **requer medição**

**Problema.** Somam-se no `3V3_OUT` (pino 36) o GPS, o display com backlight, os picos
de escrita do SD e o encoder. O total se aproxima do que o regulador interno do Pico
entrega com folga, e o documento não apresentava o cálculo.

O consumo do GPS deixou de ser estimativa — **datasheet UBX-15031086, Tabela 11**:

| Parâmetro | Valor | Nota |
| :--- | ---: | :--- |
| `ICCP` — corrente máxima de pico | **67 mA** | *"use esta figura para dimensionar a capacidade máxima da fonte"* |
| `ICC` tracking contínuo (GPS+GLONASS) | 30 mA @ 3,0 V | regime normal de condução |
| `ICC` aquisição (até o primeiro fix) | 32 mA @ 3,0 V | |
| `ICC_RF` — antena ativa (LNA) | **até 50 mA** | corrente **separada**, sai do pino VCC_RF |

Pior caso do bloco GPS: **67 mA + antena**. Com LNA de antena patch típica (~10–15 mA),
o número de projeto é **~82 mA**; com antena que consuma o máximo de `ICC_RF`, chega a
117 mA. A estimativa anterior de 50–100 mA estava aproximadamente certa, mas agora está
ancorada e o **típico é bem menor** (~40 mA) do que o de projeto.

**Correção.**
- Medir o consumo agregado com todos os periféricos ativos e backlight em 100%.
- Se não houver margem, prever regulador 3V3 dedicado a partir dos 5V.
- Registrar o resultado como requisito não-funcional (ver L-02).

---

## R-14 — Alimentação do GPS: depende do regulador da placa

- **Onde:** `bom_schematic.md` seção 3
- **Confiança:** ✅ **Faixa do chip verificada no datasheet oficial** (UBX-15031086, Tabela 10: min 2,7 · típico 3,0 · máx 3,6 V; máximo absoluto 3,6 V) / ❓ regulador da placa adquirida a identificar
- **Atualizado em:** 2026-09-15

**Problema.** A revisão 1 oferecia "5 V **ou** 3V3_OUT" sem decidir — são circuitos
diferentes. Eu havia adotado 3,3 V como suposição conservadora. **A suposição estava
mal fundamentada.**

O datasheet do CI u-blox especifica 2,7 V a 3,6 V. Esse é o limite **do chip**, não da
placa breakout — e essa distinção decide o circuito, porque a maioria das breakouts traz
LDO embarcado com faixa de entrada própria.

| Regulador na placa | Alimentar em | Motivo |
| :--- | :--- | :--- |
| Nenhum | **3,3 V** obrigatório | 5 V excede o máximo absoluto de 3,6 V e destrói o chip |
| LDO de baixa queda (HT7333, XC6206) | **5 V** preferível | 3,3 V funciona (~3,1 V), mas 5 V alivia o regulador do Pico (R-13) |
| **LDO de queda alta (AMS1117-3.3)** | **5 V** obrigatório | Com 3,3 V de entrada a saída cai a ~2,1 V — **abaixo do mínimo de 2,7 V** |

O terceiro caso é o traiçoeiro: alimentar em 3,3 V uma placa com AMS1117 deixa o CI
subalimentado. O sintoma é ausência de fix ou fix intermitente, que se confunde
facilmente com problema de antena ou de céu obstruído — e não com erro de projeto
elétrico.

**Em duas das três configurações os 5 V são preferíveis ou obrigatórios**, o que
inverte a suposição que eu havia aplicado.

**Correção.** Identificar o regulador antes de fechar o circuito: inspeção visual do
encapsulamento de 3 pinos junto ao VCC, leitura da marcação, ou medição da tensão no CI
com 5 V na entrada. Procedimento detalhado em `bom_schematic.md` §3.

**Efeito colateral positivo — questão de nível lógico encerrada.** Em qualquer das três
configurações válidas o CI opera em 3,3 V ou menos, logo o TX sai em nível compatível
com o GPIO 1. Não há necessidade de divisor nem level shifter, e a ressalva que eu havia
levantado sobre isso não se aplica.

---

## R-15 — Concorrência no SPI0 e divisão entre cores não especificadas

- **Onde:** `requirements.md` RNF04; `bom_schematic.md` seção 2
- **Confiança:** ✅ Verificado (requisito de inicialização SD / arquitetura RP2350)

**Problema.** O barramento compartilhado com dois CS distintos está correto, mas:
- O SD exige clock ≤ 400 kHz **na inicialização**, enquanto o ST7789 opera em dezenas
  de MHz — troca de velocidade por dispositivo não está prevista.
- Nenhum acesso pode se intercalar com o outro; não há requisito de exclusão mútua.
- O RNF04 fala de IRQs e timers mas não define a divisão de trabalho, apesar de o
  Pico 2 W ser dual-core.

**Correção.** Especificar no RNF04: core 0 = GPS/parsing/cálculo geográfico;
core 1 = display/encoder/LEDs; mutex no acesso ao SPI0; reconfiguração de clock por
dispositivo antes de cada transação.

---

## R-16 — O diodo 1N4148 no buzzer é desnecessário e a justificativa está incorreta

- **Onde:** `bom_schematic.md` item 13 e seção 5; `requirements.md` RNF02
- **Confiança:** ✅ Verificado (buzzer piezoelétrico é carga capacitiva)

**Problema.** O item 13 justifica o diodo como "roda livre para absorver o pico de
retorno magnético do buzzer". O SFM-27 é piezoelétrico **ativo** — carga capacitiva com
oscilador interno, sem indutância significativa. Não há pico de retorno magnético a
absorver. A justificativa técnica no documento está errada.

**Correção.** Corrigir o texto. O componente pode ser mantido (é inofensivo e protege
contra troca futura por buzzer eletromagnético), mas não deve ser descrito como proteção
necessária. A **orientação descrita está correta** para flyback (catodo no 5V, anodo no
coletor) — preservar caso o diodo seja mantido.

---

## R-17 — BC547 opera no limite de corrente

- **Onde:** `bom_schematic.md` item 10, seção 5; `requirements.md` RNF02
- **Confiança:** ⚠️ Valor típico — **medir**. O SFM-20B, que passou a ser o modelo
  padrão, consome ~10 mA; o SFM-27, ~50 mA. Em qualquer dos dois o BC337 fica folgado,
  mas o BC547 seguiria inadequado por princípio (ver R-32).

**Problema.** O BC547 tem Ic máximo de 100 mA. Um piezo de 95–105 dB pode puxar
30–50 mA, somando a capacitância do cabo longo até o painel. Funciona, mas sem margem.

**Correção.** Trocar por BC337 (Ic 500 mA) ou 2N2222 (Ic 800 mA) — mesmo encapsulamento
TO-92, mesmo custo, mesma pinagem a confirmar por datasheet. Com 1 kΩ na base a corrente
é ~2,6 mA, suficiente para saturar qualquer um dos três. Medir o consumo real do buzzer
adquirido.

---

## ~~R-18 — Mapeamento dos campos do iGO8~~ → ✅ **RESOLVIDO**

- **Onde:** `requirements.md` RF02 / RF05
- **Solução registrada em:** `formato_dados.md` §0 e §5; conversor em `converte.py`
- **Resolvido em:** 2026-09-15

O arquivo real (18.294 pontos) traz **cabeçalho explícito**:

```
X,Y,TYPE,SPEED,DirType,Direction
```

Minha previsão de que a ordem seria `X,Y` com longitude primeiro **estava certa** — e
essa era a armadilha de falha silenciosa. Confirmado.

Minha previsão de que `Direction = 0` seria o sentinela de omnidirecional **estava
errada.** O `Direction` vem preenchido mesmo quando `DirType = 0` (99,6% não-zero); o
sentinela é o próprio campo `DirType`. Semântica confirmada por teste geométrico —
proporção de registros com "gêmeo" de rumo oposto a menos de 120 m:

| `DirType` | n | Com gêmeo oposto | Conclusão |
| :---: | ---: | ---: | :--- |
| 0 | 1.419 | 0,3% | omnidirecional |
| 1 | 15.218 | **47,9%** | unidirecional (pista oposta = registro separado) |
| 2 | 1.657 | 0,2% | bidirecional |

Contraste de ~200×, conclusivo.

**Decisão revisada:** eu havia recomendado expandir cada bidirecional em dois registros.
Com os números reais isso custaria 19,4 KB de RAM a mais (233,8 KB contra 214,4 KB), e a
comparação bidirecional é uma dobra aritmética trivial. **Guardar o `DirType` em 2 bits
venceu a expansão** — ver `formato_dados.md` §3.2.

Conversor escrito, executado e verificado: 18.294 registros, zero rejeições, round-trip
de coordenadas idêntico ao `.txt`, CRC-32 e invariante de ordenação conferidos.

---

## R-19 — `limite = 0` dispara Zona de Perigo permanente → 🟨 **comportamento decidido, implementação pendente**

- **Onde:** `requirements.md` RF03 (Zona de Perigo) + matriz IHM (falta a linha)
- **Confiança:** ✅ Verificado nos dados reais
- **Decisão do autor:** 2026-09-15
- **Detalhe em:** `formato_dados.md` §7.1

**Problema.** **1.430 registros — 7,8% da base — têm `SPEED = 0`**: são os semáforos
(`TYPE=3`), que não têm limite de velocidade associado. O RF03 define a Zona de Perigo
como `Velocidade Carro > Limite Radar`; com `Limite = 0`, **qualquer** velocidade acima
de zero satisfaz a condição. Todo semáforo dispararia fundo vermelho piscante e buzzer
em "metralhadora" até o carro parar — inutilizável justamente na cidade.

Bug que só aparece com a base real na mão: a lógica do RF03 é perfeitamente coerente
até encontrar um ponto sem limite aferível.

**Decisão: nova Zona de Semáforo, silenciosa.**

| Aspecto | Comportamento |
| :--- | :--- |
| Buzzer | 🔇 **silencioso — sem exceção** |
| Visor | ícone de semáforo + distância decrescente, **sem placa de limite** |
| LED RGB | 🟡🔴 **amarelo/vermelho alternados a 2 Hz** |
| Zona de Perigo | **nunca**, independente da velocidade |

**Pendente de implementação:**
- [ ] Nova linha na matriz IHM do `requirements.md` (texto pronto em `formato_dados.md` §7.1)
- [ ] Gatilho por `limite == 0`, **não** por `TYPE == 3` — os 22 registros combinados
      (semáforo *com* limite 50/60) devem seguir pelo caminho de radar de velocidade
- [ ] Alternância em timer de hardware, conforme RNF04
- [ ] Regra de prioridade quando semáforo e radar coexistem nos 300 m (proposta na §7.1)

> ⚠️ **Esta decisão tem pré-requisito de hardware: o R-05.** Ver nota no R-05.

---

## R-20 — `TYPE=5` → ✅ **RESOLVIDO: rótulos oficiais obtidos, minhas duas inferências estavam erradas**

- **Onde:** `requirements.md` RF03.5, RF03.10; `formato_dados.md` §0.2, §7.2
- **Confiança:** ✅ **Aritmeticamente conclusivo** — contagens batem na unidade
- **Resolvido em:** 2026-09-16

### Como foi resolvido

A fonte da base permite contar pontos por categoria de equipamento. Comparando com a distribuição de `TYPE` no arquivo
baixado, o mapeamento sai sem ambiguidade:

| Categoria de equipamento | n | → `TYPE` | n no arquivo |
| :--- | ---: | :---: | ---: |
| Radar Fixo | 11.783 | **1** | 11.783 |
| **Radar Móvel** | 2.065 | **5** | 2.065 |
| **Semáforo c/ Câmera** | 1.452 | **3** | 1.452 |
| **Semáforo c/ Radar** | 2.994 | **2** | 2.994 |

E `1,2,4,5` é a única combinação de categorias que soma 18.294 — confirmando também
qual seleção gerou o arquivo atual.

### Minhas duas inferências estavam erradas

| `TYPE` | Meu rótulo inferido | Rótulo oficial |
| :---: | :--- | :--- |
| 2 | "provável lombada eletrônica" | **Semáforo c/ Radar** |
| 5 | "provável trecho controlado (velocidade média)" | **Radar Móvel** |

Eu as derivei do perfil de velocidade e da distribuição espacial. Ambas eram
plausíveis e ambas estavam erradas. O caso do `TYPE=5` é instrutivo: passei por duas
análises espaciais — a primeira com erro de método, a segunda corrigida e apontando
"evidência mista" — e **nenhuma das duas chegou perto** do rótulo real. Geometria
sozinha não recupera semântica; a fonte de dados tinha a resposta.

### O mapeamento explica as anomalias

* `TYPE=3` tem `SPEED=0` em 98,5% porque é **câmera de avanço de sinal** e não afere
  velocidade. Os 22 casos com 50/60 são inconsistências da base, não equipamento
  combinado como eu supus.
* `TYPE=2` sempre tem limite porque afere **as duas coisas** — daí a faixa urbana.
* `TYPE=5` opera em 60–120 km/h porque **fiscalização móvel** acontece em rodovia. Os
  pares a ~26 m em sentidos opostos são pontos de operação registrados por sentido, a
  mesma convenção dos radares fixos.

### Consequências aplicadas

| Item | Resultado |
| :--- | :--- |
| **RF03.5** | Reescrito de "Trecho controlado" para **Radar Móvel**. Zonamento inalterado. |
| **RF03.10** | ❌ **ANULADO.** Sem trecho controlado na base, não há par de pórticos a cronometrar. O número fica retirado, não reservado. |
| **RF03.3** | Lacuna nova — ver R-26. |

O que a correção **não** invalida: o zonamento de `TYPE=5` como "radar de velocidade
simples" sempre esteve correto. Radar Móvel afere velocidade instantânea.

---

## R-22 — GPIO do Pico em 3,3 V excede a faixa de entrada do GPS

- **Onde:** `bom_schematic.md` seção 3 (GPS RX ← Pico GPIO 0)
- **Confiança:** ✅ **Verificado no datasheet oficial** (UBX-15031086, Tabelas 9 e 10)
- **Registrado em:** 2026-09-15

**Problema.** O datasheet especifica para os pinos digitais de entrada:

| Parâmetro | Valor | Fonte |
| :--- | :--- | :--- |
| Faixa de operação `VIN` | **0 a VCC** | Tabela 10 (operating conditions) |
| Máximo absoluto `VIN` | VCC + 0,5 V *(se VCC < 3,1 V)* / 3,6 V *(se VCC > 3,1 V)* | Tabela 9 |
| `VCC` NEO-M8N | min 2,7 · **típico 3,0** · máx 3,6 V | Tabela 10 |
| Corrente por pino `IPIN` | máx 10 mA | Tabela 9 |

O Pico aciona o GPIO 0 em **3,3 V**. Como o VCC **típico** do NEO-M8N é **3,0 V**, a
faixa de operação da entrada fica em 0–3,0 V e os 3,3 V do Pico a **excedem em 0,3 V**.
Não há dano — o máximo absoluto nesse caso é VCC + 0,5 = 3,5 V — mas é operação fora de
especificação, e a margem até o limite absoluto é de apenas 0,2 V.

Se a placa tiver LDO de 3,3 V, `VIN` máximo passa a 3,3 V e a situação é limítrofe mas
dentro da faixa. Se o LDO for de 3,0 V, ou se o VCC cair sob carga, fica fora.

**Esta direção do barramento é necessária:** os comandos UBX de configuração do RF01.2
vão do Pico para o GPS.

**Correção.** **Resistor de 1 kΩ em série** no caminho `Pico GPIO 0 → GPS RX`. Limita
qualquer corrente de clamp a menos de 1 mA (contra o `IPIN` de 10 mA) e é eletricamente
irrelevante a 115200 bps: com ~10 pF de capacitância de pino, a constante RC é de ~10 ns
contra um bit de 8,7 µs.

**A direção oposta está confirmada como segura**, agora com números:

| | Valor | Conclusão |
| :--- | :--- | :--- |
| `VOH` do GPS (Tabela 10) | ≥ VCC − 0,4 V a IOH = 4 mA | 2,9 V com VCC 3,3 · 2,6 V com VCC 3,0 |
| `VIH` do RP2350 | ≈ 0,65 × 3,3 = 2,15 V | Ambos os casos leem nível alto com margem |

Nenhum divisor ou level shifter é necessário no `GPS TX → Pico GPIO 1`.

---

## R-23 — Faixas de 10%/20% ficam vazias em 82,5% dos radares da base

- **Onde:** `requirements.md` RF03.7 (escalonamento sonoro da Zona de Perigo)
- **Confiança:** ✅ **Verificado na base real** (base real, 16.864 radares de velocidade)
- **Origem:** especificação de comportamento do autor, 2026-09-15
- **Resolvido em:** mesma data, ancoragem reformulada

**Problema.** O autor especificou duas regras que, combinadas literalmente, se anulam:

1. **Tolerância legal absoluta** de 7 km/h até 100 km/h (RF03.6).
2. **Faixas sonoras** a 10% e 20% "acima da velocidade da via" (RF03.7).

Sete km/h é um percentual **grande** em via lenta — a 30 km/h equivale a 23%, já acima
da própria faixa de 20%. Ancorando os percentuais no limite da via, a faixa de bipes
lentos nasce **abaixo** do limiar em que a Zona de Perigo começa:

| Limite | `V_infra` | `limite × 1,10` | Faixa 1 |
| :--- | ---: | ---: | :--- |
| 30 | 37,0 | 33,0 | ❌ vazia — *e a faixa 2 (36,0) também* |
| 40 | 47,0 | 44,0 | ❌ vazia |
| 50 | 57,0 | 55,0 | ❌ vazia |
| 60 | 67,0 | 66,0 | ❌ vazia |
| 70 | 77,0 | 77,0 | ❌ vazia |
| 80 | 87,0 | 88,0 | +1,0 km/h |
| 120 | 126,0 | 132,0 | +6,0 km/h |

**Alcance medido na base:** os limites ≤ 70 km/h são **13.905 de 16.864 radares de
velocidade — 82,5%**. Em todos eles a faixa de bipes lentos seria vazia. E a 30 km/h
até a intermediária seria vazia, fazendo o aparelho saltar direto para **bipe contínuo**
no instante em que cruzasse o limiar de infração — o oposto exato do escalonamento
pretendido, e precisamente nas vias urbanas onde o aparelho mais será usado.

É o tipo de defeito que não aparece na leitura da especificação: as duas regras são
individualmente corretas e a interação entre elas é que falha.

**Correção aplicada.** Os percentuais passam a contar a partir de **`V_infra`** (o
limiar de infração) e não do limite da via. Preserva a intenção do escalonamento em
passos de 10% e garante faixas não vazias e monotônicas em todos os dez limites da base.
Tabela completa em `requirements.md` RF03.7.

**Ganho colateral:** as fronteiras da nova ancoragem ficam próximas dos degraus de
gravidade da legislação em vias rápidas, onde a tolerância percentual e a absoluta
convergem.

---

## R-24 — Precedência por categoria suprimiria o aviso de margem

- **Onde:** `requirements.md` RF03.4 vs RF03.9
- **Confiança:** ✅ Verificado na base real (29,2% de coexistência)
- **Origem:** interação entre duas decisões do autor, 2026-09-15
- **Resolvido em:** mesma data

**Problema.** O autor escolheu a opção (d) para o RF03.4 — precedência por categoria,
com Semáforo acima de Aproximação — e, na mesma decisão, aprovou o sub-estado de
**margem** (rosa piscante entre o limite e `V_infra`).

As duas combinadas criam um furo: um semáforo em **qualquer** ponto da janela de 300 m
suprimiria o rosa piscante, e o motorista a 1 km/h do limiar de multa não receberia
aviso. Como **29,2% dos semáforos da base têm radar de velocidade a menos de 300 m**, o
aviso de margem seria perdido justamente nas vias urbanas onde ele mais importa.

A justificativa original da opção (d) era que *"a Aproximação é o único estado sem ação
associada"* — argumento que o RF03.9 tornou verdadeiro **apenas para o sub-estado
conforme**. A margem tem ação clara (não acelerar) e certeza (o aparelho comparou a
velocidade com `V_infra`).

**Correção aplicada.** A precedência passa a ter quatro níveis, com a margem elevada
acima do semáforo:

```
Perigo  >  Margem  >  Semáforo  >  Conforme
```

Dentro de cada nível, vence o mais próximo. Exige rastrear **quatro candidatos** na
varredura — um por categoria — em vez de um único alvo.

**Achado colateral.** Ao especificar os quatro ponteiros, ficou explícito um erro sutil
que a implementação ingênua cometeria: **o estado é por ponto, não global.** Dois radares
na janela com limites diferentes — um de 60 km/h a 250 m e um de 80 km/h a 100 m, veículo
a 70 km/h — produzem simultaneamente um candidato de Perigo (o mais distante) e um de
conforme (o mais próximo). Avaliar o estado do radar *mais próximo* e usá-lo como estado
do sistema perderia a infração em curso.

---

## R-25 — Paleta do LED RGB saturada em nove estados → ✅ **RESOLVIDO**

- **Onde:** `requirements.md` RF03.9 e matriz IHM
- **Decisão do autor:** 2026-09-15

**Problema.** Com a adição do rosa (RF03.9), o LED RGB acumulava **nove** estados
distintos — segura, conforme, margem, perigo, semáforo, boot, sem sinal, OTA e falha de
dados — distinguidos por hue e taxa de piscada. Perto do limite do que um LED difuso
comunica com confiabilidade na visão periférica, e misturando duas categorias
semânticas: estado da **via** e estado do **aparelho**.

**Decisão.** Os estados de **boot, sem sinal, OTA e falha de dados** passam a ser
exibidos **somente na tela**. O LED RGB fica apagado neles, reduzindo a paleta a
**cinco** estados, todos da mesma categoria — "qual é a sua situação em relação à via".

| Estado | LED RGB |
| :--- | :--- |
| Zona Segura | 🟢 verde fixo |
| Aproximação conforme | 🟡 amarelo fixo |
| Aproximação em margem | 🩷 rosa piscante (1 Hz) |
| Zona de Perigo | 🔴 vermelho piscante (4 Hz) |
| Zona de Semáforo | 🟡🔴 amarelo/vermelho alternados (2 Hz) |
| *(todos os demais)* | **apagado** |

**Consequência não óbvia e favorável:** o **LED apagado ganha significado próprio —
nenhuma proteção ativa.** É inequivocamente distinguível do verde fixo, então um olhar
de relance informa que o sistema não está avaliando a via. Um LED colorido nesses
estados diria "estou trabalhando" sem estar.

O canal **azul** deixa de ser usado isoladamente e serve apenas à mistura do rosa (R+B).

**Pendência que este achado gerou, já resolvida:** o LED verde dedicado ao status de
Wi-Fi ficou redundante e **saiu do projeto** em 2026-09-15, liberando o **GPIO 14** —
que foi usado pelo card detect do leitor SD entre 2026-09-17 e 2026-09-22, e voltou a
ficar livre com a remoção dele (ADR 0010).

---

## R-26 — `TYPE=2` é semáforo e não recebe aviso de semáforo

- **Onde:** `requirements.md` RF03.3
- **Confiança:** ✅ Verificado no mapeamento oficial (R-20)
- **Registrado em:** 2026-09-16

**Problema.** Os **2.994 pontos de `TYPE=2` são Semáforos c/ Radar** — fiscalizam
avanço de sinal **e** velocidade. O gatilho da Zona de Semáforo (RF03.3) é
`limite == 0`, e esses pontos têm limite. Resultado: caem no caminho de radar de
velocidade e o motorista **não recebe indicação alguma de fiscalização de sinal** em
2.994 cruzamentos urbanos.

A regra `limite == 0` continua correta para o *zonamento* — há velocidade a comparar,
então a máquina de estados deve tratá-los como radar. O que falta é **indicação
visual** de que ali também se fiscaliza o sinal.

**Correção.** O campo `TYPE` já está preservado nos flags do registro
(`formato_dados.md` §3.1), então não há mudança de formato: zonamento pela velocidade,
ícone combinado de semáforo + radar na tela.

> 🎨 **Forma visual deferida** para a sessão dedicada a telas e interfaces, junto com
> a distinção visual de Radar Móvel (RF03.5) e o sinal de alerta de tipo de ponto.

---

## R-29 — O `.fzz` versionado divergiu do gerador

- **Onde:** `coruja_gps.fzz` vs `gera_fritzing.py`
- **Registrado em:** 2026-09-17

**Situação.** O `.fzz` foi gerado por script e depois **ajustado à mão** no Fritzing:
roteamento com pontos de dobra (53 → 155 fios), orientação de 16 peças e 4 notas
rotulando os módulos que aparecem como headers genéricos. Nada disso o gerador
reproduz.

Regerar o arquivo **descarta o trabalho manual**. E o gerador já foi atualizado para a
entrada de 12 V com 3 vias, enquanto o `.fzz` ainda mostra a de 5 V com 2 — a
divergência existe agora.

**Convenção adotada:** o gerador é fonte da **netlist**; o `.fzz` é fonte do
**layout**. Para mudar fiação: editar `NETS`, regerar num arquivo temporário, comparar
as redes e aplicar a mudança à mão no Fritzing.

O documento de referência para montagem é o **`bom_schematic.md`**, não o `.fzz`.

### Como fechar a divergência à mão, no Fritzing

O único ponto divergente é o conector de entrada: o `.fzz` tem 2 vias rotuladas
`+5V / GND`, o gerador tem 3 vias `+12V / n/c / GND`. São quatro passos e dois fios.

1. **Na vista Protoboard, apague o conector de entrada atual.** É o header de 2 vias
   com título *"Entrada 5V (carregador veicular)"*, ligado ao anodo do `D1`
   (Schottky) e ao GND. Apagar leva os dois fios com ele.

2. **Arraste um header fêmea de 3 vias** para a mesma posição. Na paleta:
   *Core Parts → Connection → Generic female header*, e ajuste `pins` para **3**.
   Se preferir garantir a peça exata, é a `generic-female-header-rounded_3`,
   moduleId `b13c0353-1ee1-11de-8283-0019d2b7521e`.

3. **Renomeie** para `Entrada 12V (pos-chave) -> conversor CC`, em *Inspector →
   part label*. Se quiser, acrescente uma nota ao lado, como você fez com os módulos.

4. **Refaça os dois fios**, deixando o pino central sem ligação:

   | Do pino | Para | Cor |
   | :--- | :--- | :--- |
   | 1 — `+12V` | anodo do `D1` (1N5817) | vermelho `#ff1a1a` |
   | 2 — `n/c` | *nada* | — |
   | 3 — `GND` | rede de GND | preto `#000000` |

> ⚠️ **Fisicamente, o `D1` fica depois do conversor CC**, não antes — o conversor não
> está representado no esquemático, que começa no 5 V. Ligar `+12V` ao `D1` no desenho
> é atalho de representação. Quem monta segue a **seção 0** do `bom_schematic.md`, não
> o `.fzz`.

Ao terminar, confira que o total de peças voltou a 21 e que nenhuma rede ficou órfã:
o `gera_fritzing.py` continua sendo a referência das 30 redes.

## R-30 — A falha de dados avisa por 3 s e depois cala para sempre

- **Onde:** `requirements.md` matriz de IHM, linha "Cartão SD ausente ou base inválida"
- **Confiança:** ✅ Verificado no próprio texto da matriz
- **Registrado em:** 2026-09-17
- **Status:** ✅ **CORRIGIDO** na mesma data — `requirements.md` §4.1

**Problema.** A matriz mandava exibir *"Base indisponível — modo velocímetro"* e
**permanecer na tela 3 s**, voltando depois ao velocímetro. Passados os 3 segundos, a
tela ficava idêntica à Zona Segura — número branco, LED apagado — e o motorista rodava o
resto da viagem **sem nenhuma proteção e sem nenhum indício disso**.

O LED não cobre o furo: em Falha de Dados ele fica **apagado** por decisão do R-25, e
apagado é indistinguível de aparelho desligado na visão periférica.

A ambiguidade é de significado, não de pixel: a tela de Zona Segura afirma *"não há
pontos próximos"*. Sem base, o que o aparelho sabe é *"não sei se há pontos"*. As duas
afirmações eram visualmente iguais, e a segunda é perigosa porque produz confiança
infundada — exatamente a classe de falha silenciosa que o RF07 foi escrito para evitar.

**Correção aplicada.** A mensagem passa a ser **persistente**, na faixa inferior, em
cinza. O encaixe é exato e foi o autor quem o apontou: **sem base não existe ponto, logo
a barra de proximidade nunca teria o que mostrar** — a faixa inferior está livre 100% do
tempo nesse estado, e o relógio nem precisa ceder lugar.

A mesma lógica generalizou a faixa inferior para um canal único — *"há alerta, ou por que
não há"* — que também absorveu o estado "sem sinal" e a recusa de OTA em movimento. Ver o
inquilinato em `requirements.md` §4.1.

## R-31 — A entrada de 12 V não tinha proteção nenhuma

- **Onde:** `bom_schematic.md` seção 0
- **Confiança:** ✅ Verificado no próprio desenho
- **Registrado em:** 2026-09-18
- **Status:** ✅ **CORRIGIDO** na mesma data — BOM itens 27 e 28

**Problema.** A cadeia de alimentação tinha três proteções, e nenhuma cobria o
conversor:

| Proteção | Protege | Não protege |
| :--- | :--- | :--- |
| Fusível de 2 A | o **fio** contra curto | sobretensão — fusível não reage a transiente de milissegundos |
| `C1` 470 µF em `VSYS` | o **Pico** contra ruído e queda | o conversor: fica **depois** dele |
| `C2` 100 nF em `VSYS` | idem, alta frequência | idem |

O conversor CC era **o único componente exposto direto à rede do carro**, e o
desenho contava com ele aguentar sozinho. Apareceu quando o autor perguntou se
um módulo específico de 3 A era seguro: a resposta exigia olhar o que havia a
montante dele, e não havia nada.

**Correção aplicada.** TVS bidirecional de 24 V (item 27) e eletrolítico de
470 µF / 50 V (item 28), em paralelo na entrada de 12 V, junto ao conversor.

**Sobre o que isso cobre — e o que não cobre.** Registro aqui porque eu mesmo
exagerei ao propor: disse que o TVS "existe justamente para load dump". Está
errado. Um load dump real chega a 60–120 V com impedância de fonte de ordem de
ohms por até 400 ms; contra um clamp de 33 V isso dá dezenas de ampères e mais
de **1 kW sustentado**, e 600 W ou 1500 W são ratings de pulso de 10/1000 µs,
não de centenas de milissegundos. Nenhum TVS axial pequeno sobrevive.

O que o TVS cobre são os transientes **frequentes e de baixa energia** —
chaveamento indutivo, ruído de ignição, pulsos da ISO 7637-2 — que são os que
matam módulo barato no uso diário. Para o load dump, o projeto se apoia no fato
de que alternador de carro moderno já clampa internamente em ~35 V. **É uma
suposição, não uma medição**, e vale dizer isso em voz alta em vez de deixar o
componente novo dar falsa sensação de blindagem.

**Detalhe que quase passou.** O sufixo `CA` é obrigatório: significa
bidirecional. A versão `A` é unidirecional e, montada ao contrário, fica em
curto permanente com 12 V atrás. E o fusível tem de ficar **antes** da proteção
no percurso do cabo: o modo de falha desejável de um TVS é curto, e sem fusível
a montante ele vira aquecedor ligado na bateria.

## R-32 — Audibilidade com janela aberta, e a faixa 3 era o padrão menos detectável

### ✅ Medição de bancada, 2026-09-27: 52 dB em 5 V contra 75 dB em 12 V

O autor mediu o SFM-27 nas duas alimentações:

| Alimentação | Nível medido |
| :--- | ---: |
| 5 V | **52 dB** |
| 12 V | **75 dB** |

**23 dB de diferença.** Não é um ganho marginal: em pressão sonora são ~14×
(10^(23/20)), e em sonoridade percebida, à regra de +10 dB ≈ "duas vezes mais alto",
algo perto de **cinco vezes**. É a justificativa do ADR 0009 confirmada por medição, e
não por raciocínio: os 12 V entraram no gabinete por causa do buzzer, e o buzzer era o
único componente que pedia isso.

Também explica por que a especificação de 3–24 V do módulo não é uma faixa onde tanto
faz. Em 5 V ele opera junto ao mínimo, e o rendimento acústico despenca ali.

**Condições, completadas em 2026-09-27:** medido a **~5 cm** com o telefone do autor
(Blackview BV9300 Pro). Instrumento não calibrado.

### A extrapolação para a posição do ouvido, e por que ela preocupa

Em campo livre a pressão cai 6 dB a cada dobro de distância:

| Distância | Nível estimado |
| ---: | ---: |
| 5 cm *(medido)* | **75 dB** |
| 10 cm | 69 dB |
| 40 cm | 57 dB |
| **80 cm** *(ouvido do motorista)* | **~51 dB** |

Contra uma cabine que a 80 km/h com janela aberta fica em **75–85 dB**, isso é um
déficit de **25 a 35 dB** — o alerta não apenas ficaria baixo, ficaria abaixo do ruído.

**As ressalvas são grandes e vão todas na mesma direção de incerteza, não de conforto:**
a cabine é reverberante e cai menos que campo livre; medidor de telefone não é
calibrado e erra mais em 4 kHz; e 5 cm é campo próximo para um transdutor de 22 mm, o
que torna a extrapolação frágil. Fácil errar ±10 dB. Mas o sinal do resultado não muda.

### A discrepância que precisa ser resolvida antes de mexer em hardware

O BOM registra **"até 105 dB"** para o SFM-27. A extrapolação da medição dá **69 dB a
10 cm**. São ~36 dB de diferença, demais para erro de instrumento sozinho.

Hipóteses, e a primeira é a que muda a decisão:

1. **Os 105 dB podem ser especificados em 24 V**, o topo da faixa de 3–24 V. Se for
   isso, o número da folha pressupõe uma alimentação que o projeto não fornece.
2. Medidor de telefone lendo baixo.
3. Campo próximo num transdutor de 22 mm.
4. A peça em mãos não ser a que se supõe (o BOM aceita SFM-20B **ou** SFM-27, e são
   bem diferentes: 95 dB/10 mA contra 105 dB/~50 mA).

### O experimento que responde de verdade

Medir com **o mesmo telefone** o buzzer na posição de montagem e o ruído de cabine a
80 km/h com janela aberta. Sendo o mesmo instrumento não calibrado nos dois, o erro
sistemático se cancela na **diferença** — que é o que interessa. Isso responde o R-32
com um número em vez de estimativa, e custa uma volta de carro.

O **delta entre 5 V e 12 V** está estabelecido e basta para a decisão de alimentação.
A **audibilidade** continua pendente, e agora com indício desfavorável.

- **Onde:** `requirements.md` RF03.7 · `bom_schematic.md` item 7 e RNF05
- **Confiança:** ⚠️ Estimativa acústica, **não medida** — ver ressalva
- **Registrado em:** 2026-09-18
- **Status:** ⏳ **PARCIAL** — a faixa 3 virou pulso de 10 Hz, e em 2026-09-21 o buzzer
  passou a ser alimentado em 12 V em vez de 5 V (ADR 0009), o que ataca a mesma causa
  pelo lado elétrico. **A audibilidade em campo segue sem medição.**; montagem documentada

**Contexto que faltava.** O veículo é um **Uno Mille 2009 sem ar-condicionado**, e o
autor roda normalmente **com as janelas abertas**, em vias de ~80 km/h. Isso não é uma
condição excepcional a tolerar: é o caso de uso normal, e portanto o **caso de projeto**.

Com janela aberta a 80 km/h, num carro de 2009 e pouco isolamento, o ruído interno fica
em torno de **87 dB(A)**, dominado por vento. Contra isso, em decibéis brutos:

| Buzzer | A 70 cm | A 30 cm |
| :--- | ---: | ---: |
| SFM-20B (95 dB) | **−9 dB** | −2 dB |
| SFM-20B (se vier 85 dB) | −19 dB | −12 dB |
| SFM-27 (105 dB) | +1 dB | +8 dB |

**Nem o SFM-27 tem folga a 70 cm.** A conclusão importante é que **trocar de buzzer não
resolve** um déficit desse tamanho — e é a primeira coisa que alguém tentaria.

**Por que não é tão ruim quanto a tabela.** A comparação em dB brutos é pessimista por
três motivos, e nenhum deles é desprezível:

1. **Separação espectral.** Mascaramento é seletivo por frequência: um tom estreito só
   precisa vencer o ruído **na banda crítica dele**, não o nível total de banda larga.
   Ruído de vento se concentra abaixo de ~1 kHz; os **3,9 kHz** do SFM-20B caem onde o
   ruído tem pouca energia e a audição é mais sensível.
2. **Padrão pulsado** detecta muito melhor que tom estável contra ruído estável.
3. **O LED é o canal periférico primário por projeto.** Nesta condição ele deixa de ser
   redundância e passa a ser a defesa principal — o que o desenho já acomoda.

**O defeito de projeto que isso expôs.** A faixa 3 do RF03.7 usava **bipe contínuo**, e
tom contínuo é **o padrão menos detectável** contra ruído estável: o sistema auditivo se
adapta em segundos, e o vento faz exatamente isso. O alerta mais urgente tinha a forma
mais fácil de mascarar.

**Corrigido:** faixa 3 passa a ser **50 ms a cada 100 ms**, um pulso de 10 Hz. Mantém a
mensagem de escalonamento pela cadência (1 Hz → 2,9 Hz → 10 Hz), resiste ao mascaramento
por ser transiente repetido, e continua inconfundível em relação à faixa 2.

**Nota de sorte de configuração.** Numa via de 80 km/h o `V_infra` é 86, e a faixa 3 só
começa a **103,2 km/h** — raro num Uno Mille com janela aberta. Na prática o autor viverá
nas faixas 1 e 2, que já eram pulsadas. Isso reduz a exposição ao problema, mas não era
projeto, era acaso, e não valeria deixar como está.

**O que vale mais que o modelo.** Documentado no item 7 do BOM:

| Ação | Ganho | Custo |
| :--- | ---: | ---: |
| Trocar SFM-20B por SFM-27 | +10 dB | ~R$ 15 |
| Apontar para o motorista | +6 a +12 dB | R$ 0 |
| Aproximar de 70 cm para 30 cm | +7 dB | R$ 0 |

O JST-XH de 2 vias (R-06) torna a troca de buzzer reversível depois do projeto fechado,
então a decisão de modelo não é crítica. A de montagem é.

> ⚠️ **Ressalva de confiança.** Os 87 dB(A) de ruído interno e os ganhos de
> reposicionamento são **estimativas de campo livre e de literatura, não medições neste
> veículo**. A atenuação por distância assume campo livre, e o interior de um carro não
> é. O teste é subjetivo e não cabe em multímetro: montar, rodar a 80 km/h com janela
> aberta e julgar se é inconfundível. Se não for, seguir a ordem de tentativa acima.

## R-33 — O LED é de ânodo comum, e isso inverte a lógica de acionamento

- **Onde:** `bom_schematic.md` item 8 e §4 · `gera_fritzing.py` · `firmware/src/led/`
- **Confiança:** ✅ Verificado na peça física pelo autor
- **Registrado em:** 2026-09-18
- **Status:** ✅ **CORRIGIDO** na mesma data

**Problema.** O projeto especificava **LED RGB 5 mm, cátodo comum**, e o firmware foi
escrito sobre essa premissa. A peça que o autor tem em casa é **10 mm difuso, ânodo
comum**.

| | Cátodo comum *(premissa)* | **Ânodo comum** *(realidade)* |
| :--- | :--- | :--- |
| Terminal comum | GND | **`3V3_OUT`** |
| O GPIO | **fornece** corrente | **drena** corrente |
| Acende com GPIO em | nível **alto** | nível **baixo** |
| PWM | duty direto | **duty complementado** |

Montar um no lugar do outro **não queima nada**, e é por isso que o erro é ruim: o LED
simplesmente fica **aceso ao contrário** — apagado quando deveria acender, e no brilho
complementar em cada canal. O sintoma é confuso, e num LED que codifica quatro estados
de via por cor, é o tipo de coisa que se depura por horas.

**Correção aplicada, em quatro lugares:**

1. **Firmware.** `LedRgbPwm` virou `LedRgbAnodoComum`, com o nível de PWM complementado
   (`kWrap − intensidade`). A polaridade está no **nome da classe** e não num parâmetro
   de construtor, de propósito: ela não é configuração, é propriedade física da peça
   soldada, e com o nome no tipo a escolha errada fica visível onde se escolhe a classe.
   A inversão é aritmética e não por `pwm_set_output_polarity()`, porque a polaridade em
   hardware é por canal de slice e os três GPIO se espalham por dois slices — GPIO 6 e 7
   são A e B do mesmo, GPIO 8 é A de outro. Essa contabilidade é fonte de bug silencioso;
   uma subtração não é.
2. **Netlist.** O terminal comum saiu da rede `GND` e entrou na rede `3V3`. As redes
   `LED_x_ANODO` viraram `LED_x_CATODO`, porque é o cátodo que agora desce pelo resistor.
3. **BOM e §4.** Item 8 passa a 10 mm, ânodo comum, e a fiação foi reescrita.
4. **Folha de bancada, rev. 5.** O diagrama do R-05 mostrava o resistor do lado do 3V3.

**O que o teste não pegou, e por quê.** Os 92 casos continuaram verdes durante toda a
troca, e corretamente: a inversão vive na única classe que toca registrador de PWM, que
por decisão do **ADR 0001** fica fora do alvo de teste de host. O `LedRgbMock` é
agnóstico de polaridade — ele guarda `Cor`, não duty — e é isso que faz a lógica de
`ModoTesteEncoder` continuar válida sem uma linha de mudança. A separação funcionou como
projetada; só não há como um teste de host detectar um LED soldado ao contrário.

**Duas notas que não são defeito.**

* **O 10 mm é melhor** para este uso: lente maior, mais área luminosa na visão
  periférica, que é exatamente o papel do LED no RF03.4. Muda o furo do gabinete.
* **Não ligar o ânodo comum nos 5 V**, por tentador que pareça — resolveria o aperto de
  margem do verde e do azul que o R-05 investiga. Durante o reset os GPIO ficam em alta
  impedância e o LED puxaria os pinos na direção de 5 V menos o `Vf`; no canal vermelho,
  de `Vf` mais baixo, isso chega perto do máximo absoluto do GPIO.

**Divergência conhecida no `.fzz`.** O arquivo versionado usa a peça *"LED RGB catodo
comum"* da biblioteca do Fritzing, com o comum ligado ao GND. O gerador já está correto;
o `.fzz` foi editado à mão pelo autor e **não será regerado** (R-29). A correção ali é
manual: mover o fio do terminal comum do GND para o `3V3`.

## R-34 — O GPS era o único módulo sem tabela de pinagem, e o desenho estava errado

- **Onde:** `bom_schematic.md` §3 · `gera_fritzing.py`
- **Confiança:** ⚠️ Ordem vinda da **foto do anúncio** do módulo comprado — a confirmar
  na serigrafia
- **Registrado em:** 2026-09-18
- **Status:** ⏳ **PARCIAL** — tabela corrigida na mesma data; confirmação física pendente

**Problema.** Três módulos deste projeto têm pinagem que não se adivinha, e **dois deles
divergiram do documentado** quando o autor conferiu a peça física:

| Módulo | O que o documento dizia | O que a placa tinha |
| :--- | :--- | :--- |
| Leitor microSD | 6 pinos, `VCC GND CLK DI DO CS` | **8 pinos**, com nomes duplos |
| KY-040 | `CLK DT SW + GND` | **`GND + SW DT CLK`** — invertido |
| **GY-GPS6MV2 (GPS)** | **nada — não havia tabela** | a confirmar |

O GPS era o único **sem tabela de pinagem física**, apesar de ser o módulo onde um erro de
`VCC`/`GND` seria destrutivo. E o `gera_fritzing.py` assumia `VCC, GND, TX, RX`, enquanto a
foto do anúncio do módulo efetivamente comprado mostra **`VCC, RX, TX, GND`** — pinos 2 e
4 trocados.

**Correção aplicada.** Tabela criada na §3 no mesmo formato das outras duas, ordem do
gerador corrigida, e item novo no checklist de pré-energização exigindo conferir a
serigrafia **antes** de ligar.

**O que aconteceria seguindo o desenho errado.** Não é destrutivo, e é por isso que é ruim:
o **`VCC` é o pino 1 nas duas versões**, então não havia risco de 5 V no lugar errado. Mas
o `GND` do módulo chegaria através do resistor de 1 kΩ do R-22, e o `RX` ficaria preso em
nível baixo. O GPS não ligaria direito e nunca receberia a configuração UBX do RF01.2 —
dano zero, sintoma confuso, e o tipo de coisa que se procura no firmware.

**O que estava certo e vale registrar.** O cruzamento UART está correto na netlist:
`GPIO 0 (TX) → 1 kΩ → GPS RX` e `GPS TX → GPIO 1 (RX)`. O outro erro clássico de UART,
ligar TX↔TX, não está presente.

**Divergência adicional no `.fzz`.** O arquivo versionado tem o GPS com a ordem antiga:
`connector1` é o `GND` e `connector3` é o `RX`, quando deveriam estar trocados. O gerador
já está correto e o `.fzz` não será regerado (R-29). A correção ali é manual: trocar de
posição os fios de `GND` e de `RX` do módulo GPS.

**Padrão que isto revela.** Dois de três módulos com pinagem divergente não é azar, é taxa
de acerto de documentação de módulo genérico de marketplace. A regra que vale para o
display de 2,4" que também está chegando: **nenhuma pinagem de módulo é confiável até ser
lida na serigrafia da peça em mãos**, e o checklist de pré-energização é onde isso vira
obrigação em vez de intenção.

## R-35 — Vermelho e azul do LED estavam trocados, e o mapa passou a descrever a placa

- **Onde:** `firmware/src/placa/Pinos.h` · `bom_schematic.md` §4 · `gera_fritzing.py`
- **Confiança:** ✅ **Determinado empiricamente** com o modo de calibração na placa
- **Registrado em:** 2026-09-19
- **Status:** ✅ **CORRIGIDO** no mapa de pinos

**Como apareceu.** Com o modo de calibração gravado, o autor observou a sequência de
cores ao clicar: **azul, verde, vermelho, ciano, lilás**. O firmware manda vermelho,
verde, azul, âmbar, rosa.

**As compostas fecharam o diagnóstico**, e são o que descarta as outras hipóteses:

| Item | Firmware manda | Observado | Com R e B trocados |
| :--- | :--- | :--- | :--- |
| Vermelho | `255,0,0` | azul | azul ✅ |
| Verde | `0,255,0` | verde | verde ✅ |
| Azul | `0,0,255` | vermelho | vermelho ✅ |
| **Âmbar** | `255,115,0` | **ciano** | azul+verde = **ciano** ✅ |
| **Rosa** | `255,0,153` | **lilás** | azul+vermelho = **lilás** ✅ |

Cinco de cinco. A hipótese concorrente — comum ligado ao GND em vez do 3V3 — foi
descartada por cálculo antes do teste: ela acenderia verde e azul juntos, e como o verde
é ~3,7× mais visível na combinação de correntes deste projeto, o resultado seria verde ou
ciano esverdeado, **não azul puro**.

**A decisão: corrigir o mapa, não a fiação.** O autor optou por manter a protoboard como
está e trocar as constantes. É a escolha certa, e por um motivo que não é preguiça:
**`placa/Pinos.h` documenta a placa como construída**, e esse é o papel dele. Trocar fio
para satisfazer um documento é inverter quem manda.

O que tornou a troca possível sem perder nada foi um detalhe: **os resistores já estavam
casados com a cor**, não com o GPIO. O de 330 Ω já terminava na perna vermelha. Se
estivessem presos ao GPIO, trocar só as constantes daria cores certas com **correntes
trocadas** — vermelho a 150 Ω e azul a 330 Ω — jogando fora a calibração do R-05 feita
sob sol. Foi a pergunta que se fez antes de mexer em qualquer linha.

**Mapa final:**

| Canal | GPIO | Pino físico | Resistor |
| :--- | ---: | ---: | ---: |
| Vermelho | **8** | 11 | 330 Ω |
| Verde | 7 | 10 | 470 Ω |
| Azul | **6** | 9 | 150 Ω |

**O quarto módulo com pinagem diferente da assumida.** Depois do leitor SD (8 pinos em
vez de 6), do KY-040 (ordem invertida) e do GPS (pinos 2 e 4 trocados), agora o LED RGB.
Quatro de quatro entre os que foram verificados fisicamente. A regra do R-34 se confirma
e vale para o display de 2,4" que ainda vai chegar: **nenhuma pinagem de módulo genérico
é confiável até ser observada na peça.**

**De passagem, o que o mesmo teste já provou funcionando:** o encoder decodifica o
clique, o anti-repique não gera evento duplo, o ciclo de itens avança na ordem certa, os
três canais do LED acendem, e a inversão de PWM do ânodo comum está correta — se
estivesse errada, os canais apareceriam complementados.

## R-36 — Os 100 nF de debounce do encoder destruíam o sinal que deviam limpar

- **Onde:** `bom_schematic.md` item 17 e §4 · `requirements.md` RF04
- **Confiança:** ✅ **Medido na placa** em 2026-09-19, com e sem os capacitores
- **Registrado em:** 2026-09-19
- **Status:** ✅ **RESOLVIDO** — monta **sem capacitor**. Não há valor novo a comprar:
  o debounce é a máquina de estados do `DecodificadorQuadratura`. Um RC de 1 a 10 nF
  fica registrado como contingência, caso a montagem definitiva exija.

**Problema.** A revisão 2 deste documento mandou soldar **100 nF entre `CLK` e GND** e
outro entre `DT` e GND, com a justificativa de que "o KY-040 é eletricamente ruidoso;
sem este filtro o ajuste de brilho salta de forma errática mesmo com decodificação por
máquina de estados em software".

A justificativa é razoável. **O valor foi escolhido sem medir nada**, e com ele o giro
do encoder **não produz um único passo decodificado**.

**A medição.** Com o firmware de diagnóstico amostrando a 50 µs:

| | Com 100 nF | Sem capacitor |
| :--- | ---: | ---: |
| Fase `(0,1)` | 0,6 – 2 ms | **45 – 128 ms** |
| Estado `(0,0)` | **nunca ocorreu** | **5,75 – 25,4 ms** |
| Passos decodificados | **zero** | quadratura íntegra |

O capacitor de 100 nF com o pull-up de 10 kΩ do módulo dá **τ = 1 ms**. Contra fases que
duram **dezenas de milissegundos**, ele comprimia pulsos de 60 ms em pulsos de 1 ms e
**apagava a sobreposição inteira** — o estado `(0,0)`, que é onde a quadratura codifica
a direção. A tabela de transição fazia o que devia: sem `(0,0)`, o acumulado oscila em
torno de zero e nunca atinge ±4.

**Direção conferida nos dois sentidos**, com o filtro removido: 11 ocorrências de
`(0,1) → (0,0) → (1,0)` e 12 de `(1,0) → (0,0) → (0,1)`, praticamente simétrico para
8 detentes em cada sentido.

**Decisão do autor, em 2026-09-19: montar sem capacitor**, e o RF04 foi revisado para
acompanhar. É defensável, e por um motivo que estava implícito no projeto sem nunca ter
sido dito: **a máquina de estados já é o debounce**. Repique de contato é oscilação entre
dois estados adjacentes, e na tabela isso soma `+1, −1, +1, −1` — zero líquido. É o teste
`RuidoNaoProduzPassoLiquido`, que alterna 200 vezes numa borda e exige zero passo. Um
passo só sai com **quatro transições válidas consecutivas na mesma direção**, que ruído
simétrico não produz.

E o filtro em software é **independente de frequência**; o RC não é, e foi justamente
essa dependência que quebrou tudo.

| Evidência a favor | Valor |
| :--- | :--- |
| Mudanças espúrias, parado, sem capacitor | **0 em 12 s** |
| Passos falsos na sessão de calibração | nenhum |
| Folga do `(0,0)` sobre a amostragem | **5,8×** |

**O que não foi testado, e fica dito:** o ambiente do veículo, com alternador e ignição.
Dois fatos reduzem o risco — o encoder é **interno ao gabinete**, com fios curtos, ao
contrário do buzzer, que é remoto com 2 m de cabo; e o modo de falha é **benigno e
óbvio**, o brilho saltando sozinho, não uma falha silenciosa que engane o motorista.

**Contingência, mantida barata:** o lugar dos capacitores fica na placa. Se o brilho
oscilar no veículo, soldar **1 a 10 nF** (τ de 10 a 100 µs) resolve sem redesenhar nada.
**Nunca 100 nF.**

**Como o erro se sustentou.** Duas vezes, e as duas por olhar a variável errada:

1. Ao especificar, dimensionei um filtro **sem conhecer a duração das fases do sinal**
   que ele iria filtrar. Constante de tempo só significa alguma coisa em relação ao que
   se quer preservar.
2. Quando o autor perguntou diretamente *"será que o problema são os capacitores?"*,
   respondi que duvidava, argumentando que o RC **alarga** o pulso baixo e portanto
   deveria tornar o `(0,0)` mais provável. O argumento está correto **isoladamente** e é
   irrelevante: o que importa é a **fase relativa** entre os dois canais, e o RC atrasa
   cada um independentemente. Ele chegou lá primeiro; eu o demovi.

**Consequência para o ADR 0005.** O receio de perder detente girando rápido não se
confirma: o pior caso medido do `(0,0)`, já na volta rápida, foi **5,75 ms** contra
1 ms de amostragem — **5,8× de folga**. Polling a 1 ms basta, e a interrupção de borda
deixa de ser pendência e passa a ser desnecessária.

## R-14 — fechado: o LDO da placa GPS existe, e a pinagem não era a típica

- **Onde:** `bom_schematic.md` §3, árvore de decisão de alimentação
- **Confiança:** ✅ Medido na peça, com fonte de bancada
- **Status:** ✅ **FECHADO** — 5 V liberados

**O que se queria saber.** A placa GY-GPS6MV2-NEO M8N tem regulador entre o `VCC` do
header e o chip u-blox? O chip é de 3,6 V máximo; sem LDO, os 5 V da decisão do R-14 o
destroem.

**O componente.** SOT-23-**5** marcado `LB2k`, com o `VCC` entrando numa perna da ponta
do lado de três. A linha de inspeção dizia "encapsulamento de 3 pinos" — são cinco. Não
muda a conclusão, mas mostra que o texto descrevia o que se imaginava.

⚠️ **A marcação não identificou a peça.** O banco de códigos SMD dá `LB2K` como um
XC6219B27ADR da Torex, LDO de 2,75 V, mas em **USP-6B, de seis pinos**. Código de
marcação não é único entre fabricantes, e com o encapsulamento divergindo a
identificação não vale.

**E a pinagem típica de datasheet também errou.** A suposição (1=IN, 2=GND, 3=EN, 4=NC,
5=OUT) previa a saída no pino 5. Medido, o pino 5 está em **0 V** e a saída é o **4**.
Terceira vez na semana em que presumir layout típico falha e a medição corrige — mesma
família do R-66.

| Pino | Função | Evidência |
| :---: | :--- | :--- |
| 1 | `Vin` | curto com `VCC` na continuidade |
| 2 | `GND` | |
| 3 | `EN`, amarrado no `Vin` | curto com `VCC` — montagem "sempre ligado" |
| **4** | **`Vout`** | **3,19 V** com 3,29 V na entrada |
| 5 | — | 0 V |

**As medidas,** fonte de bancada a 3,3 V com limite de corrente em 150 mA:

| | |
| :--- | ---: |
| `VCC` no header | **3,29 V** |
| Saída, pino 4 | **3,19 V** |
| Consumo | **42 mA** · 0,141 W |

**Por que 0,10 V de queda prova regulação.** A 42 mA são 2,4 Ω equivalentes. Trilha de
PCB nessa corrente cai microvolts; só elemento ativo em série produz isso. E a
continuidade já mostrara a saída **aberta** em relação ao `VCC`, descartando passagem
direta.

**O dropout é a previsão de setembro se cumprindo.** O R-14 concluiu que a 3,3 V este
LDO viveria em dropout, e foi por isso que a operação ficou em 5 V. Sobrarem 0,10 V de
margem é exatamente isso.

**Consumo abaixo do orçado.** A BOM previa ~82 mA para o bloco — 67 de pico mais ~15 de
LNA de antena. Com 42 mA medidos **sem antena**, a dissipação do LDO em 5 V fica em
**0,071 W**, cerca de 18 °C de elevação num SOT-23-5, e o uso do limite típico de
150 mA cai para **28%**. Mesmo somando o LNA, 57 mA seguem bem abaixo do orçamento —
folga confortável até no painel quente do R-65.

## R-67 — O procedimento de bancada do transistor ficou perigoso quando o buzzer foi para 12 V

- **Onde:** `bom_schematic.md` nota do item 10 · `roteiro_bancada.html` §02
- **Confiança:** ✅ Aritmética sobre datasheet, e a pinagem foi medida
- **Status:** ✅ **CORRIGIDO** — procedimento substituído; pinagem desta peça registrada

**O defeito.** Os dois documentos mandavam determinar coletor e emissor
**funcionalmente**, tentando as duas orientações no circuito real, e afirmavam:

> *"**Não há risco** em tentar as duas orientações a **5 V** e 10 mA"*

E a nota do item 10 justificava: *"o `V_EBO` do 2N2222 é 6 V. Com o trilho de 5 V sobra
1 V de margem."*

**O buzzer não está em 5 V.** O **ADR 0009** o levou para **12 V** — é inclusive a razão
de os 12 V entrarem no gabinete, e a própria seção de fiação do mesmo documento avisa em
negrito *"É 12 V, não 5 V"*. As duas frases são anteriores ao ADR e não foram revistas.

**A consequência.** Invertido, quem bloqueia a alimentação é a junção base-emissor:

| Peça | `V_EBO` | Aplicado | |
| :--- | ---: | ---: | :--- |
| 2N2222 | 6 V | ~12 V | 2× |
| BC337 | 5 V | ~12 V | 2,4× |

Nos **dois** estados do GPIO. A corrente fica limitada pelo buzzer, então degrada em vez
de destruir — e ruptura reversa de base-emissor derruba o hFE permanentemente. **Um
transistor degradado ainda satura numa chave**, então o dano não aparece. Soma-se ao
sintoma sutil que a mesma nota já descrevia para o SFM-20B: seguir o procedimento
documentado podia estragar a peça *e* esconder que estragou.

**O método primário também falhou.** Os documentos mandavam "leia a marcação e puxe o
datasheet daquela variante", listando `P2N2222A`, `PN2222A` e `2N2222A`. A peça em mãos
traz `2N2222` / `A331` — **sem prefixo de fabricante**. Um `2N2222A` puro é o número
JEDEC genérico e não identifica a disposição dos pinos. O procedimento presumia que a
marcação sempre discriminaria a variante, e ela não discrimina.

**A substituição: ruptura reversa.** As duas junções da base rompem em tensões muito
diferentes — base-emissor em ~6 V, base-coletor em 60 a 75 V. Aplicando 12 V reversos
com 47 kΩ em série, o emissor grampeia e o coletor não.

É melhor que o teste funcional por não depender de **ganho, saturação nem modo reverso**
— e isso não é teórico: o teste de saturação foi tentado nesta peça e **não
discriminou**, dando ~35 mA nas duas orientações. A causa não foi apurada.

**Pinagem medida (2026-10-03), peça marcada `2N2222 / A331`:**

| | |
| :--- | :--- |
| Tipo | **NPN** — conduz com a vermelha no central para os dois outros |
| Base | **pino central** |
| Ruptura, pino esquerdo | **9,13 V** → emissor |
| Ruptura, pino direito | **11,47 V** → coletor |
| **Face chata para o observador, pernas para baixo** | **E – B – C** |

Os 11,47 V em vez de 12 V são a impedância de entrada do multímetro (~1 MΩ) carregando
os 47 kΩ, não condução da junção.

**O sintoma real, observado em 2026-10-03.** A montagem foi feita com C e E trocados, e
o resultado **não** foi o "som mais fraco" que esta nota previa: **o buzzer ficou ligado
direto, desde que o aparelho energiza, ignorando o firmware.** Trocar as duas pernas
resolveu na hora.

A previsão de som fraco descrevia o **modo reverso**, que é o que domina a 5 V. A 12 V
quem domina é a **ruptura da junção base-emissor** — medida em 9,13 V nesta peça —, que
abre um caminho de corrente do trilho ao terra que o GPIO não tem como interromper.

| Trilho | C e E trocados produzem |
| :--- | :--- |
| 5 V | modo reverso, ganho 2 a 5 → **som mais fraco** (sutil) |
| **12 V** | **ruptura base-emissor → buzzer SEMPRE LIGADO** (óbvio) |

🟢 **Os 12 V transformaram uma falha sutil numa falha evidente.** A mesma tensão que
torna o erro perigoso para a peça é a que o denuncia na primeira vez que se liga o
aparelho. A 5 V o defeito teria sobrevivido à montagem como "esse buzzer é fraquinho".

**Fica como sintoma de diagnóstico:** buzzer ligado direto e indiferente ao software é
**coletor e emissor trocados**, não polaridade do buzzer — piezo ativo invertido fica
**mudo**, nunca ligado.

**A regra que sai disto.** Quando um ADR move uma tensão de trilho, **toda afirmação de
margem que cita aquela tensão fica suspeita** — e margens aparecem em notas de segurança,
que é onde errar custa peça. O ADR 0009 mudou 5 V para 12 V em setembro, e duas frases
de "não há risco" sobreviveram três semanas em dois documentos diferentes.

## R-66 — A BOM divergiu das peças em mãos em três pontos num só dia

- **Onde:** `bom_schematic.md`
- **Confiança:** ✅ Três divergências confirmadas, duas delas com consequência
- **Status:** ⏳ **ABERTO** — inspeção pendente

**O sintoma.** Em 2026-10-01 a documentação discordou da peça física três vezes:

| Item | A BOM dizia | A peça é | Consequência |
| :--- | :--- | :--- | :--- |
| Torres da Patola | "torres de fixação para placa" *(descrição da revenda)* | torres da **tampa** | plano de fixação refeito |
| Local do conversor (item 22) | "montado **fora** do gabinete" | **dentro**, desde o ADR 0009 | linha obsoleta, contradizia o item 19 |
| Conector da antena (item 2) | "antena ativa externa **SMA**" | **U.FL**, rabicho de **8 cm** | **duas propostas nasceram mortas** |

**Por que importa.** As duas últimas me levaram a propor arranjos que não funcionam —
caixa na coluna A e antena remota — porque eu inferi fato físico de documento em vez de
conferir a peça. É a mesma forma do **R-63** (três pinos desconectados, cinco hipóteses
erradas antes de olhar o fio) e do card detect do **ADR 0010** (quatro diagnósticos
sobre uma leitura não conferida).

A BOM foi escrita em 2026-09-15, antes de quase tudo existir fisicamente. Ela
envelheceu enquanto a montagem avançava, e agora que praticamente tudo está comprado e
montado, ela é a única fonte que **ninguém reconferiu contra o hardware**.

**A inspeção.** Meia hora com paquímetro, conferindo contra a peça em mãos:

- [ ] **conector por conector** — família, gênero e diâmetro
- [ ] **comprimento de cabo por comprimento de cabo** — o que é roteável e o que não é
- [ ] encapsulamento e marcação dos semicondutores
- [ ] o que está **soldado direto** e o que é desconectável
- [ ] revisar as linhas que o ADR 0009 e o ADR 0010 deveriam ter superado

**Regra que sai disto.** Não planejar montagem sobre descrição de revenda nem sobre
linha de BOM que antecede a compra. Fato físico se confere na peça — e as três vezes
de hoje custaram duas propostas inteiras.

## R-65 — O NEO-M8N fica fora da faixa de ARMAZENAMENTO no painel ao sol

- **Onde:** `requirements.md` RNF09 · `montagem.md` §4
- **Confiança:** 🟡 Datasheet confirmado; temperatura de fonte externa, não medida no aparelho
- **Status:** ⏳ **ABERTO E ACEITO** — **ADR 0011**: monta-se com o que já existe e as
  mitigações são contingentes a medição (**M-08**, **M-06**). Risco conhecido, não
  defeito a corrigir agora.

**O defeito.** O RNF09 afirmava que o painel "ultrapassa 60 °C" e que um painel ao sol
no verão brasileiro "chega perto" dos 85 °C do módulo. Medição com termômetro
infravermelho em São Paulo, após 5 h de sol, deu **92 °C na superfície do painel**.

O número do requisito estava subestimado em mais de 30 °C, e a conclusão qualitativa
estava errada na direção que importa: **não chega perto, passa** — por 7 °C.

E o limite excedido é o de **armazenamento**, não o de operação:

| | NEO-M8N | NEO-M8M |
| :--- | :---: | :---: |
| Operação | −40 a +85 °C | −40 a +85 °C |
| **Armazenamento** | **+85 °C** | **+105 °C** |

Ou seja: o aparelho desligado, parado, já está fora da especificação. Não existe
estado em que a condição seja segura pelo datasheet.

**A assimetria que ninguém tinha notado.** O aparelho **opera** com o carro ligado, e
aí o ar-condicionado refrigera a cabine. Ele **armazena** desligado, parado ao sol.
Logo o limite que aperta é o de armazenamento — e é justamente nesse eixo que o M8M
tem 20 °C mais de margem que o M8N que está em mãos.

**O que o 92 °C é, exatamente.** Superfície de um plástico escuro, fosco e absorvedor,
ao sol direto, incapaz de dissipar o que absorve — o pior ponto do veículo. O ar da
cabine fica bem abaixo (47 °C após 1 h, medição da Arizona State). A temperatura que o
**módulo** atinge depende de três variáveis, e as três são de projeto:

| Variável | Alavanca |
| :--- | :--- |
| Condução dos 92 °C | **folga de ar** entre a caixa e o painel — é o acoplamento mais forte |
| Absortividade própria | **face solar clara** (a tampa da Patola já é a peça cinza) |
| Troca de ar | **ventilação por convecção** — caixa selada ao sol é estufa |

**Mitigação recusada, e a recusa é de produto.** Remover o aparelho ao estacionar
resolveria termicamente e foi **vetada pelo autor**: contraria a premissa de estar
sempre pronto para uso. Exigir conexão ao entrar no carro faz o celular com Waze ganhar
por atrito, e o aparelho perde a razão de existir. Uma mitigação que destrói o requisito
que a motivou não é mitigação.

**Mitigação adotada — e ela conserta um erro do plano de montagem.** O `montagem.md`
punha a prateleira do GPS **na tampa**, com módulo e antena juntos. A tampa é a face
solar: era o pior lugar possível para o componente termicamente limitante.

A prateleira migra para o **chassi**, em camadas (§4 do `montagem.md`):

- antena no topo da prateleira, vendo o zênite através de **folga de ar** até a tampa;
- a prateleira de FR4 passa a ser **escudo de radiação** entre a tampa quente e o módulo;
- módulo **sob** a prateleira, na sombra dela.

Ganho adicional, e foi objeção do autor que o revelou: **com a prateleira no chassi, a
abertura da tampa não mexe no conjunto GPS.** O coaxial nunca flexiona. A entrada de RF
do módulo alimenta o LNA por *bias tee* e é sensível a ESD; o conector é a peça mais
frágil da montagem. Uma versão intermediária desta proposta separava antena e módulo
entre tampa e chassi — e teria posto a peça mais frágil a flexionar a cada manutenção.

### A ordem de grandeza das mitigações — e ela não é óbvia

A primeira versão deste achado listava só mitigações de montagem, o que passava a
impressão errada. Com o cabo da antena medido em **8 cm** (ver abaixo), a exigência de
vista de céu **prega a caixa no ponto mais ensolarado do carro** — e isso não tem saída
por geometria.

| Ordem | Mitigação | Rende |
| :---: | :--- | :--- |
| **1ª** | **Antena de cabo longo + bulkhead SMA** (`montagem.md` §4.8) | **dezenas de °C** — a caixa deixa de precisar de céu e vai para a sombra |
| 2ª | Não conduzir: pés + manta isolante refletiva | o acoplamento mais forte depois da posição |
| 2ª | Não absorver: face solar clara, parede dupla, sombra | a entrada dominante é radiante |
| 3ª | Ventilar | acopla o interior ao ar da cabine (47–60 °C) |
| 4ª | Dissipador interno | ~3,5 °C de origem própria (2 W em 0,056 m²) |

⚠️ **Dissipador SOB a caixa foi considerado e recusado.** O problema é calor *entrando*:
alumínio (~200 W/m·K) entre o painel de 92 °C e a caixa de ABS (~0,2 W/m·K) troca um
isolante por um condutor mil vezes melhor, e anodizado preto ao sol é absorvedor solar
quase ideal. É problema de **isolar**, não de dissipar. Os pés funcionam pelo motivo
oposto: minimizam área de contato e deixam ar parado, que é o melhor isolante de graça.

### O cabo da antena tem 8 cm, e isso matou duas propostas

Medido pelo autor: a fêmea do módulo é **U.FL / IPEX MHF1**, ~2 mm de diâmetro a
paquímetro, com **30 ciclos de encaixe** no datasheet da Hirose. A BOM dizia "antena
ativa externa SMA" (corrigido em 2026-10-01).

Duas propostas desta sessão nasceram mortas sobre essa suposição:

| Proposta | Por que morreu |
| :--- | :--- |
| Caixa na **coluna A** | Ganho térmico e acústico reais, mas o teto bloqueia o zênite, e em superfície vertical não se tem tampa-para-o-céu e display-para-o-motorista ao mesmo tempo. Some o airbag de cortina e a zona de impacto de cabeça. |
| **Antena remota** no painel, caixa na sombra | 8 cm não chegam a lugar nenhum. |

**O que sobreviveu da coluna A:** o **buzzer**. Ele já tem **2 m de cabo próprio** na
BOM — a posição dele sempre foi livre, e levá-lo para perto do ouvido ataca o **R-32**
sem compra nenhuma. Está soldado direto desde 2026-09-25, então é decisão de uma vez só.

**Lição de método, e é a terceira do mesmo tipo hoje.** Inferi fato físico de documento
em vez de conferir a peça: as torres da Patola (descrição da revenda), o local do conversor
(linha obsoleta após o ADR 0009) e o conector da antena. As duas últimas me fizeram
propor coisa que não funciona. Mesma forma do R-63 e do card detect do ADR 0010.
Registrado como item de inspeção **R-66**.

**Candidato para a v2:** trocar para o **NEO-M8M** pela faixa de armazenamento. ⚠️ Antes
de adotar, confirmar que ele atende **GPS+GLONASS concorrente** na taxa do RF01.4; o
**R-21** ancorou o teto de 5 Hz para o M8N, não para o M8M. A placa em mãos é a
GY-GPS6MV2-NEO M8N (R-14), então é troca de placa, não de configuração.

**Postura, e ela é explícita.** Limite de datasheet não é precipício: 92 °C ocasionais
aceleram envelhecimento, não matam o módulo na hora. Como isto é projeto de estudo e não
produto em série, a posição é **medir o real (M-08), reduzir o que é barato reduzir,
registrar o risco, e saber do que suspeitar** se o GPS degradar em janeiro. O que não é
defensável é não saber que o risco existe.

## R-64 — A fonte de 56×94 do §4.1 não cabe uma velocidade de três dígitos

- **Onde:** `requirements.md` §4.1, tabela de assets
- **Confiança:** ✅ Aritmética, confirmada na maquete no painel real
- **Status:** ✅ **CORRIGIDO** — hierarquia de escala, `FonteNumeroPequeno`

**O defeito.** O §4.1 especifica uma fonte numérica de **56×94** para
`velocidade/limite`, com 11 glifos (`0-9` e `/`). Some as larguras do pior
caso real:

```
"120/120"  →  7 glifos × 56 px  =  392 px
tela útil  →  320 − 2×2 de moldura  =  316 px
```

**Não cabe, e por 76 px.** Não é caso extremo: rodovia brasileira tem limite
de 110 e 120 km/h, e velocidade de três dígitos é o normal nelas.

**Por que passou.** O §4.1 fixou o tamanho da célula sem multiplicar pelo
conteúdo máximo. E a primeira maquete só não expôs isso porque eu escolhi
`72/60` como exemplo — 5 glifos, 280 px, cabe. **Escolhi um caso que caberia
e concluí que o layout funcionava.** O autor pediu explicitamente para ver
`100/120`, e foi o pedido que revelou o problema.

**A correção: hierarquia de escala, não encolher tudo.** Reduzir a fonte
única para 45 px faria caber, ao custo de diminuir a velocidade — que é
justamente o que se lê de relance. Em vez disso:

| Elemento | Fonte | Pior caso |
| :--- | :--- | ---: |
| Velocidade | 56×94 | `120` → 168 px |
| `/limite` | **28×48** | `/120` → 112 px |
| | | **280 px** ✅ |

Isso também concorda com a atenção do motorista, e não só com a aritmética:
a velocidade é a informação, o limite é referência. O §4.1 já lista
"hierarquia por contraste de escala" entre as qualidades exigidas — aqui ela
deixou de ser recomendação e virou necessidade geométrica.

**Custo em flash:** +2.112 bytes. Total das três fontes: 12,8 KiB, contra os
~10 KiB que o §4.1 orçava para duas. O orçamento era de 16 KiB com os
sprites, e ainda cabe.

**O limite assenta na linha de base da velocidade**, não centralizado na
altura da própria célula — alinhado pelo meio ele pareceria flutuar acima do
número.

## R-63 — Primeira ligação do painel: o custo de não conferir o óbvio

- **Onde:** bancada, 2026-09-29
- **Confiança:** ✅ Painel desenhando; cada hipótese descartada por medição
- **Status:** ✅ **FECHADO** — e registrado como lição de método

**O sintoma.** Backlight aceso, tela sem nada. Nenhuma cor, em nenhuma
velocidade, com o firmware rodando até o fim (provado pelo LED por etapa).

**A causa.** Os pinos `DC`, `CS` e `RST` **não estavam conectados**. O `DC` é o
que distingue comando de dado no SPI de 4 fios; sem ele, o ST7789V nunca
interpretou um único comando como comando. `SLPOUT`, `COLMOD`, `DISPON`: nada
chegou. O painel nunca saiu do repouso.

**O que isso invalida.** Cinco rodadas de diagnóstico, todas sobre software:

| Hipótese perseguida | Veredito |
| :--- | :--- |
| Clock de 62,5 MHz alto demais para protoboard | plausível, mas não era a causa |
| `CS` solto entre comando e parâmetros | idem |
| LDO do módulo morto | descartada por medição (3,27 V) |
| `RST` preso em nível baixo | descartada por medição (3,24 V) |
| Falta de `NORON` e atrasos curtos | idem |
| Falta da sequência de tensões internas | idem |

Nenhuma delas podia funcionar, porque **o driver nunca chegou a ser exercido**.

**O erro de método, que é o que importa.** A pergunta *"os oito pinos estão
fisicamente conectados?"* nunca foi feita. Ela é a mais barata e a mais básica
de todas, e foi pulada porque a conversa começou pela tabela de pinagem — o
que criou a impressão de que a ligação estava feita.

Pior: houve um teste de continuidade com resultado "ok em todos os pontos", e
ele foi tratado como se cobrisse os cinco sinais. Continuidade prova **o fio**,
não a presença dele. Um par não conectado não é medido como falha — ele
simplesmente não é medido.

**O que fica como regra.** Antes de qualquer hipótese de protocolo num
periférico novo:

1. Conferir **presença física** de cada pino, um a um, contra a tabela.
2. Só então medir continuidade, e **enumerar** os pares medidos.
3. Só então olhar o software.

O `bancada_display` já tinha a etapa 2 exatamente para isso — pulsar cada pino
para medição com multímetro. Ela existia, foi escrita, e foi ignorada em favor
de teorias mais interessantes.

## R-62 — Controlador do display identificado: ST7789V, e sem MISO

- **Onde:** `bom_schematic.md` item 5 e §2; peça em mãos em 2026-09-29
- **Confiança:** ✅ Serigrafia lida pelo autor, peça e versão confirmadas em fonte externa
- **Status:** ✅ **FECHADO** — a pendência mais antiga do display

**O que estava em aberto.** O item 5 do BOM dizia *"controlador a confirmar: 2,4"
costuma ser ILI9341, não ST7789 — a sequência de inicialização difere"*, e a §2
tinha o mesmo aviso. Era pendência real: as duas sequências de inicialização são
incompatíveis, e escrever a errada dá tela preta sem mensagem de erro.

**O que a peça diz.** A serigrafia do verso é `GMT024-08-SPI8P ver.: 1.3`. É um
painel de 2,4" **240×320** com **ST7789V**.

| | Estava escrito | É |
| :--- | :--- | :--- |
| Controlador | ILI9341 *(palpite do BOM)* | **ST7789V** |
| Resolução | 240×240 *(título antigo da §2)* | **240×320** nativo |

O palpite do BOM estava errado e o título original da §2 estava certo quanto ao
controlador — e errado quanto à resolução. Como o firmware usa a tela deitada em
320×240 (`Visor.h`), o painel nativo em retrato exige **rotação por MADCTL** na
inicialização; não é o mesmo que um painel nativo em paisagem.

**O achado que não estava previsto: o módulo não tem MISO.** São 8 pinos —
`GND, VCC, SCL, SDA, RST, DC, CS, BL`. Duas consequências de peso:

1. **Não há leitura de registrador.** O método definitivo de identificar o
   controlador (ler o ID por SPI) **não existe nesta peça**, e o mesmo vale para
   qualquer diagnóstico que dependa de ler estado de volta. A verificação de que
   a inicialização funcionou é **visual**: um padrão de teste na tela, olhado por
   uma pessoa. Nenhum teste automatizado substitui isso.
2. **Um risco do barramento compartilhado desaparece.** A §2 divide o SPI0 entre
   display e cartão. Sem pino MISO, o display **não tem como** disputar a linha de
   dados de leitura do microSD. O que resta ali é só o cuidado com o clock, que o
   cartão exige ≤ 400 kHz na inicialização e o display quer em dezenas de MHz.

**Pendente por consequência.** A inversão de cor (`INVON`) é típica dos painéis
IPS com ST7789 e não dá para decidir no papel: ou as cores saem certas, ou saem
todas complementares. Fica para a primeira ligação, junto com a rotação.

## R-61 — Modo noturno: LDR descartado, o GPS já sabe que horas são

- **Onde:** proposta do autor em 2026-09-28; decisão registrada antes de implementar
- **Confiança:** ✅ Regras da paleta e pinos ADC conferidos no código
- **Status:** ✅ **DECIDIDO** — sinal vem do GPS; a paleta **não** muda

**A proposta.** Um LDR para saber se é dia ou noite e ligar um modo noturno com
"cores mais suaves" na tela.

**A metade das cores foi recusada, e a razão é estrutural.** As três regras da paleta
do §4.1 existem *por causa* do PWM do backlight: distinguir por matiz e nunca por
luminância, nunca só por saturação, número sempre branco. "Cores mais suaves" quer
dizer baixar luminância ou saturação — exatamente o que as regras 1 e 2 proíbem —, e
faria isso à noite, com o backlight em 5%, que é quando a margem é menor.

Pior: o **R-05 continua aberto** e pergunta precisamente se âmbar, rosa e vermelho
sobrevivem distinguíveis a 5%. Suavizar gastaria uma margem que ainda não foi medida.

E o modo noturno, em certo sentido, já existe: **fundo preto permanente mais backlight
baixo**. O §4.1 diz que o preto não é estética — com o brilho em 5%, quanto menor a
área acesa, menor o ofuscamento. O que faltava era só decidir o brilho sozinho.

**O LDR foi descartado por três motivos, nenhum deles o custo da peça.** Há GPIO 26,
27 e 28 livres e são ADC, então hardware não era o obstáculo:

1. **Duplica um controle que existe e funciona.** O encoder já ajusta de 5 a 100 em
   passos de 5.
2. **Errar é pior que não ter.** Brilho automático que erra muda a tela sem pedido:
   viaduto, túnel, farol de quem vem atrás, sombra de caminhão, sol rasante no sensor —
   cada um é uma transição falsa.
3. **O difícil é a mecânica.** Dentro da caixa, o sensor precisa de um furo que veja
   luz ambiente sem ver sol direto nem farol. Esse posicionamento *é* o projeto, e não
   é óbvio.

**O sinal escolhido: o próprio GPS.** Data, latitude e longitude bastam para calcular
nascer e pôr do sol. Sem peça nova, sem ADC, sem calibração, sem furo na caixa — e,
para escolher um **modo**, mais confiável que o LDR: não vira noite dentro de um
túnel, que é justamente o que não se quer de um modo.

A fraqueza é simétrica e aceita: ele não sabe de garagem coberta nem de temporal ao
meio-dia. Para brilho instantâneo isso contaria; para modo dia/noite é o comportamento
desejável.

**O que muda, então:** o **brilho**, entre dois presets, e nada mais. A paleta fica
como está. O encoder sobrepõe sempre, até a transição seguinte.

**Ordem acordada:** o R-05 continua sendo o que decide se há margem para qualquer
refinamento noturno além disto, e é medição de bancada quando a tela chegar.

### Implementado em 2026-09-28

`nucleo/PeriodoDoDia` calcula nascer e pôr do sol pelo algoritmo do NOAA, e o
`Brilho` ganhou **dois presets** — o ajuste manual edita o do período vigente, então
se acerta uma vez de dia e uma vez de noite e a transição seguinte já vem certa. Um
preset só obrigaria a reajustar duas vezes por dia, para sempre.

Os valores de referência vieram de uma implementação independente em Python, e foram
conferidos por um terceiro caminho que não depende da precisão da conta: no equinócio
o dia dá 12h06m — **pouco mais** de doze horas, porque o zênite de 90,833° inclui
refração e meio disco solar — com o meio-dia solar às 12:18 local, que é a soma da
correção de longitude (+11,5 min) com a equação do tempo de março (+7,4 min).

**Um defeito real, achado por teste:** em longitudes a leste o meio-dia solar cai perto
de 00:00 UTC e a conta crua devolve **minuto negativo** para o nascer. Sem normalizar
para `[0, 1440)`, a comparação com o relógio comparava coisas diferentes e o aparelho
acharia que é dia à meia-noite na Nova Zelândia. No Brasil nunca apareceria.

E dois erros meus **nos testes**, não no código: escrevi os casos polares com os
hemisférios trocados — no solstício de junho quem fica no escuro é o sul, não o norte.

11 defeitos injetados, 11 mortos.

**Pendência:** falta ligar o `define_periodo` ao laço do firmware. Depende do porte do
backlight, que depende de identificar o controlador do painel. A prévia de terminal já
exercita o caminho.

---

## R-60 — O LED apagado queria dizer duas coisas

- **Onde:** `led/PadraoLed`, `requirements.md` §4.1
- **Confiança:** ✅ Separação de matiz calculada; 487 testes
- **Registrado em:** 2026-09-28
- **Status:** ✅ **APLICADO**

**O problema, que estava à vista desde o começo.** O desenho original deixava o LED
**apagado** sem fix, sem base e durante o OTA. Apagado também é o que se vê quando o
aparelho perde energia, trava ou queima. Ou seja: o canal dizia *"não estou
protegendo"* e *"morri"* com o mesmo sinal, e o motorista não distingue os dois sem
tirar os olhos da estrada — que é exatamente o que o LED existe para evitar.

É a mesma família do R-46 e do buraco de log: **estado silencioso é pior que estado
curto**, porque faz quem observa concluir a coisa errada.

**A correção, e a regra que ela produz.** Azul fixo para os três casos, e o escuro
deixa de ser estado:

> **azul = vivo e sem proteção ativa · escuro = sem energia**

Um significado cada. Os três casos viram um só porque, para o motorista, são o mesmo
fato — não há alerta agora —, e a ação é a mesma nos três. É o mesmo critério que
retirou o ícone do radar móvel no R-59: **distinção que não muda decisão é ruído.**

**Por que azul, e por que fixo.** Matiz 240°, a **96°** do vizinho mais próximo,
contra os 40° que o §4.1 exige como mínimo discriminável — magenta ficaria em 36° e
ciano em 60°. O canal azul já tem o menor resistor da placa (150 Ω) por ser o mais
fraco, então está calibrado. E fixo, não pulsante: sem fix **não há ação a tomar**, e
piscar pediria uma atenção que não se deve pedir. O canal pulsante fica para o urgente.

**Um teste guarda a regra.** Ele percorre as seis zonas e falha se **alguma** deixar o
LED apagado o tempo inteiro. Se um dia alguém reintroduzir o escuro como estado, a
ambiguidade volta junto — e aí a suíte avisa, em vez do trânsito.

**Pendência:** os estados de OTA ainda não existem como zona, então o firmware não tem
onde honrar o azul durante a atualização. O requisito já manda; o código vai junto
quando o modo OTA entrar no laço.

---

## R-59 — Prévia do produto no terminal, e uma distinção visual retirada

- **Onde:** `ferramentas/VisorTerminal`, `ferramentas/previa_produto`,
  `display/Visor.h`, `requirements.md` §4.1
- **Confiança:** ✅ Rodado contra o simulador, 500+ fixes a 4 Hz sem erro
- **Registrado em:** 2026-09-28
- **Status:** ✅ **FEITO**

Com o módulo de GPS e o de tela ainda não entregues, o produto inteiro passou a rodar
no host: `LeitorGps`, `PilotoAlerta`, `MaquinaZona`, `TelaPrincipal`, `CadenciaBuzzer` e
`PadraoLed` são os **mesmos objetos** que o `main.cpp` vai instanciar. Trocam-se três
portes de saída — a UART vira pty, o painel vira ANSI, LED e buzzer viram texto.

Serve ao que teste unitário não alcança: ver a coisa **em movimento**. Já rendeu,
imediatamente, o que se esperava dela.

### O `x` do texto significava duas coisas

`Visor::texto` recebia `x` como **centro** para `Fonte::Numero` e como **borda
esquerda** para `Fonte::Texto`, sem nada no código dizendo isso. Não dava erro porque
só havia duas chamadas, cada uma escrita por quem sabia. A terceira teria 50% de chance
de acertar. O alinhamento virou parâmetro explícito, com teste afirmando cada escolha:
faixa superior centralizada, faixa inferior à esquerda — esta porque o contador `0:14`
cresce no fim da linha e centralizado arrastaria a frase de lado a cada segundo.

### Emoji no terminal, sprites no painel

No painel são sprites próprios, e o §4.1 explica: não há pilha de fontes no Pico. No
terminal há, então ali o emoji é **mais** fiel que `[RADAR]`. Custou duas mudanças na
grade: emoji ocupa duas colunas e tem vários bytes, então a célula virou `std::string`
com marca de continuação, e as cadeias passaram a ser quebradas em glifos UTF-8 — sem
isso, um emoji cortado ao meio faria tudo à direita escorregar.

### O radar móvel deixou de ter ícone próprio

Decisão do autor, e boa. O desenho original usava um carro **vazado** para dizer "este
ponto pode não estar aqui hoje". Mas o RF03.5 já manda zonear o móvel exatamente como o
fixo, e **a ação do motorista é a mesma nos dois casos**: distinção que não muda
decisão é ruído no instante em que menos se pode gastar atenção.

O `TYPE` continua distinto no dado e na base — o que se retirou foi o canal visual. O
valor saiu do `enum` em vez de virar um apelido, porque um valor que ninguém mais
produz é código morto. Economiza um sprite, 3,1 KiB de flash, e o §4.1 foi emendado.

---

## R-58 — A tela, e os 150 KB de framebuffer que não precisavam existir

- **Onde:** `display/Visor.h`, `display/TelaPrincipal`, `display/Brilho`
- **Confiança:** ✅ 35 testes, mutação com 15 defeitos
- **Registrado em:** 2026-09-28
- **Status:** 🟡 **layout e brilho FEITOS**; o porte do painel depende de identificar
  o controlador

### O framebuffer sai do orçamento inteiro

O RNF07 reserva **150,0 KB** para um framebuffer 320×240 RGB565 e exige ≥ 60 KB de
folga. Com os 182 KiB livres medidos no binário real (L-02), um framebuffer inteiro
deixaria **32 KiB** — abaixo da própria reserva. O requisito previa uma alavanca de
alívio, renderização em bandas de 40 linhas, que cairia para 25 KB.

Nenhuma das duas é necessária. O próprio §4.1 já continha a resposta, três seções
adiante da tabela de memória: *"o layout não muda entre estados"* e *"nada pisca"*,
com os custos por região tabelados — 38,4 ms para a tela toda contra 3,4 ms para a
barra. **Se o redesenho é sempre parcial, não há o que bufferizar.** A `TelaPrincipal`
compara o que vai desenhar com o que desenhou e emite só as regiões que mudaram; o
`.bss` medido depois de tudo isto continua em 338,3 KiB, **sem um byte novo**.

Vale registrar o formato do erro: a linha de 150 KB não estava errada quando foi
escrita, estava desatualizada em relação a uma decisão tomada no mesmo documento.
Orçamento e desenho moram em seções diferentes e ninguém releu as duas juntas.

### O controlador está contraditório, e o porte espera por isso

O item 5 do BOM diz *"controlador a confirmar: 2,4" costuma ser ILI9341, não ST7789"*,
e o título da seção 2 do mesmo arquivo dizia **"Display ST7789"**. O nome saiu do
título; a identificação é passo de bancada, e a sequência de inicialização difere entre
os dois. **Não escrevi o porte concreto** — inventar uma sequência de inicialização
para o chip errado é trabalho que se joga fora, e o que decide não é raciocínio, é
olhar a peça.

O que ficou pronto é o que não depende disso: a interface `Visor`, todo o layout do
§4.1 e a curva de brilho do RF04.

### Dois mutantes mascarados por valores neutros

Sobreviveram à primeira suíte, e os dois pelo mesmo motivo — o teste usava um valor em
que o certo e o errado coincidem:

* **Barra enchendo ao contrário.** Eu testava 300 m → 0%, 150 m → 50%, 0 m → 100%. Os
  extremos são fixados pelos limites, e **150 m dá 50% nos dois sentidos**. Só um ponto
  assimétrico distingue: 75 m → 75%, ou 25% se estiver invertida.
* **Zona Segura ganhando ícone.** O teste usava um `Veredito` com o alvo zerado, e tipo
  zero não é `TipoPonto` válido, então nenhum ícone saía nem com o `if` quebrado.
  Agora o alvo vai **preenchido** e quem manda é o `tem_alvo`.

É a terceira vez nesta sessão que um teste passa pelo motivo errado. O padrão é sempre
o mesmo: **escolher o caso pelo que é fácil de escrever, e não pelo que distingue.**

---

## R-57 — O laço do produto, e o que sobrou de decisão para ele

- **Onde:** `app/PilotoAlerta`, `led/PadraoLed`, `led/Cor.h`
- **Confiança:** ✅ 22 testes, mutação com 11 defeitos
- **Registrado em:** 2026-09-28
- **Status:** ✅ **FEITO** — item 8 da revisão geral

O `PilotoAlerta` lê o GPS, decide a zona e manda no LED e no buzzer. Cabe em vinte
linhas, e **isso é o resultado**, não economia: toda a decisão já estava no
`Zonamento`, no `CadenciaBuzzer` e no `PadraoLed`, cada um com suíte própria. O que os
testes dele verificam não é lógica, é **fiação** — que o veredito chega ao LED certo,
que o buzzer só soa em Perigo, que perder o fix apaga tudo.

### Sem fix e sem base são o mesmo caso

Cartão ausente, base recusada ou túnel: nos três não há o que afirmar sobre a via. O
motorista não precisa saber qual faltou para entender que não há alerta, e a tela tem
onde dizer a diferença. É a mesma decisão do ADR 0010 aplicada um nível acima.

### O `PadraoLed`, e por que ele não mora no `Zonamento`

A máquina decide **o que está acontecendo**; o padrão decide **como mostrar**. Trocar a
paleta, o período de piscada ou o próprio LED não deve tocar na lógica de alerta.

O semáforo alterna amarelo↔vermelho em vez de piscar contra o apagado: não é gravidade
intermediária entre margem e perigo, é **outra natureza** de alerta, e o par de cores
evoca a própria coisa. Um teste garante que o apagado nunca aparece nessa zona.

### Um sobrevivente que virou teste melhor

`define_base()` chama `maquina_.reinicia()`, e o mutante que o removia sobrevivia: o
alvo já está protegido por coordenada desde o R-51. Mas `reinicia()` faz uma segunda
coisa — **zera a histerese** —, e isso é observável. A 65 km/h contra limite 60
(`V_infra` 66), vindo de Perigo o limiar está rebaixado para 64 e 65 ainda é Perigo; do
zero, 65 não passa de 66 e é Margem. **Uma base nova não pode chegar já em Perigo por
causa da anterior.** O teste que distingue os dois casos matou o mutante e documentou
uma regra que não estava escrita em lugar nenhum.

---

## R-56 — O configurador do GPS, e a armadilha de trocar o baud no meio

- **Onde:** `gps/Uart.h`, `gps/UartPico`, `gps/ConfiguradorGps`
- **Confiança:** ✅ 19 testes, mutação com 10 defeitos e 10 mortos
- **Registrado em:** 2026-09-28
- **Status:** ✅ **FEITO** — item 7 da revisão geral. Prepara o fechamento do R-53

### O leitor, e o byte que derrubava a sentença seguinte

O `LeitorGps` puxa bytes da UART e os vira telemetria, alimentando o
`MonitorTaxa` no caminho. Dois achados vieram dos testes, e nenhum dos dois eu
teria previsto:

**Quadro UBX gruda na sentença seguinte.** Texto e binário dividem a linha, e um
`ACK` que chegue entre duas sentenças fica no buffer de montagem e prefixa a
próxima — que então não começa com `$` e é descartada. Acontece o tempo todo
*durante a configuração*, que é justamente quando não se quer perder telemetria. A
correção é de uma linha e vale como regra geral: **`$` reinicia a montagem**, porque
o que estava no buffer antes dele era lixo por definição.

**Bytes de UBX não contam como checksum inválido.** Eles produzem "linhas" sem `$`,
e contá-las poluiria o número que o RF01.5 existe para separar — "o GPS não está
enviando" contra "estamos falhando em interpretar". Sem esse cuidado, configurar o
módulo pareceria ruído elétrico na linha.

### E eu fabriquei um checksum de novo

A sentença sem fix do teste levava `*7A`, inventado. O correto é `*63`. É o mesmo
erro que o `NmeaTest` já registra — e, de novo, quem pegou foi o validador, não eu.
Vale menos como falha isolada e mais como padrão: **toda constante de protocolo
escrita à mão neste projeto até hoje saiu errada.** Calculadas em Python, saem certas.

### Uma redundância removida em vez de documentada

O montador recortava o `\r` do fim da linha. A mutação mostrou que nenhum teste
distinguia as duas versões — o `analisa_rmc` para no `*` e ignora o que vem depois.
O recorte saiu, e a tolerância do parser virou **afirmação testada** em vez de
suposição.

O RF01.2 manda enviar quatro comandos a cada boot. O que **não** estava escrito em
lugar nenhum é que mandá-los não basta: mandar e torcer produz exatamente o sintoma que
o RF01.5 descreve — o módulo segue em 1 Hz com sete sentenças por época, e o defeito só
aparece meses depois como "taxa baixa". Cada comando aqui espera o `ACK-ACK` **da sua
classe e do seu id**.

### A armadilha do `CFG-PRT`

A resposta ao comando que troca o baud sai **na velocidade nova** — o módulo troca ao
processá-lo. Se a porta local continuasse em 9600, esperaríamos um ACK ilegível e
concluiríamos "não respondeu", com o módulo tendo respondido. A ordem correta é:
escrever o quadro, trocar a porta local, **e só então** esperar.

E há um segundo laço: a u-blox **não garante** esse ACK. Tratá-lo como obrigatório
recusaria um módulo que se configurou certo. A saída não foi ignorar o passo, foi
**deslocar a prova**: o silêncio no `CFG-PRT` é tolerado, e quem confirma que a porta
nova está de pé é o `CFG-CFG` seguinte — se a porta tivesse ficado muda, nenhum ACK
chegaria lá. Um NAK, ao contrário, é recusa explícita e encerra.

### Silêncio e recusa deixaram de ser a mesma coisa

Na primeira versão que escrevi, um `NAK` no `CFG-RATE` era reportado como "o módulo não
respondeu". São dois lugares diferentes para procurar: silêncio aponta para fiação,
energia ou baud errado; recusa diz que o módulo entendeu e não aceitou. Corrigido antes
de existir teste, ao escrever os casos.

### O que a mutação achou depois de 17 testes passando

Dois defeitos sobreviveram à primeira suíte, e os dois eram buracos meus:

* **Aceitar ACK de qualquer comando.** O dublê sempre respondia pelo comando recém
  enviado, então o filtro por id nunca era exercitado. Na linha de verdade chega sobra
  de ACK anterior, e aceitar qualquer um daria por confirmado um comando que o módulo
  pode nem ter visto.
* **NAK no `CFG-PRT` tratado como o silêncio tolerado.** Faltava o caso.

Desligar as seis sentenças extras **antes** de subir o baud também é deliberado: a
9600 as sete de fábrica não cabem nem em 1 Hz, e é essa a linha congestionada por onde
o próximo comando vai passar.

---

## R-55 — O logger de cartão ganhou teste, e o `CartaoSd` continua sem — com motivo

- **Onde:** `log/LoggerCartao`, `armazenamento/CartaoSd`
- **Confiança:** ✅ Medido: 16 testes novos, mutação com 10 defeitos
- **Registrado em:** 2026-09-28
- **Status:** ✅ item 5 **CORRIGIDO** · ⚠️ item 6 **AVALIADO E ADIADO**

### Item 5 — `LoggerCartao`

107 linhas sem teste, e foi onde nasceu o R-46 — a perda silenciosa de 14 linhas de
log. A correção da época foi verificada à mão, comparando arquivo com serial.

Bastou o que o R-54 já tinha criado: trocar `CartaoSd&` por `Armazenamento&`
(acrescentando `acrescenta_arquivo` à interface) e o logger virou portável. Ele decide
**quando** gravar, não **como** — nunca precisou do cartão concreto.

16 testes, entre eles a regressão do R-46: gravação que falha **preserva** o buffer, e
as linhas de antes da falha sobrevivem quando o cartão volta.

### A redundância que a mutação destapou

O guarda de reentrância existe em **dois** lugares: `descarrega()` e `registra()`.
Medido em 2026-09-28: removendo **qualquer um dos dois**, a suíte continua passando —
o outro segura. Removendo **os dois**, ela morre com SIGSEGV por recursão infinita.

Isso é incômodo de um jeito útil. Cada guarda, olhado sozinho, parece código morto que
alguém vai "limpar" um dia. Escrevi um teste que torna o de `descarrega()`
individualmente necessário — a reentrância pela porta pública é real, o `main` chama
`descarrega()` — e o de `registra()` ficou documentado no código com a medição, porque
não há caminho alcançável que o isole. Não é sobra: são duas portas diferentes.

### Item 6 — `CartaoSd`

> **Retratação, 2026-09-28.** Horas antes eu avaliei que o caminho era FatFs de
> verdade sobre disco em RAM, e que sairia caro. Errado no diagnóstico, não na
> estimativa: **não queremos testar o FatFs.** Ele é
> maduro e não é nosso. Queremos testar a nossa lógica **sobre** ele — e os casos que
> interessam são justamente os que um disco real torna difíceis: "o volume 0 não monta
> e o 2 sim", "o `f_rename` falhou", "o cartão encheu no meio da escrita". Num dublê
> são um campo; num disco em RAM, uma obra.
>
> A superfície é pequena e fechada: `f_mount`, `f_unmount`, `f_open`, `f_close`,
> `f_read`, `f_write`, `f_size`, `f_stat`, `f_rename`, `f_unlink`, `FRESULT_str` e
> `sd_init_driver`. Uma fachada de 217 linhas cobre tudo.
>
> **O `CartaoSd.cpp` de produção compila sem uma linha alterada** — o que muda é qual
> `ff.h` o caminho de include encontra. O `ffconf.h` é o **nosso**, o mesmo do alvo
> Pico, então os `static_assert` passam a verificar a configuração real também no host.
>
> 21 testes, mutação com 9 defeitos e 9 mortos. Entre eles **o defeito do R-38**:
> parar na primeira partição que monta, em vez de seguir procurando o arquivo. Aquele
> bug, que custou uma investigação com cartão na mão, agora falha a suíte em 30 ms.
>
> Cobertos também: a troca atômica guardando a base anterior, a primeira atualização
> sem base a guardar, o `.bak` antigo que impediria o rename, a renomeação que falha
> deixando a base vigente intacta, a distinção do ADR 0010 entre cartão ilegível e
> arquivo ausente, e a escrita indo ao **mesmo volume** onde a leitura achou.
>
> A lição é sobre a pergunta. Eu perguntei *"como rodar o FatFs no host?"* e a resposta
> era cara. A pergunta certa era *"o que, aqui, é nosso?"* — e aí a resposta é barata.

---

## R-54 — 310 linhas de OTA só rodavam na placa, por uma dependência que não precisava existir

- **Onde:** `rede/AtualizadorOta`, `armazenamento/Armazenamento.h`, `rede/Conexao.h`,
  `rede/Baixador.h`, `nucleo/Pausa.h`
- **Confiança:** ✅ Medido: 23 testes novos, 11 defeitos injetados e 11 mortos
- **Registrado em:** 2026-09-28
- **Status:** ✅ **CORRIGIDO** — item 4 da revisão geral

**O problema.** O `AtualizadorOta` recebia `CartaoSd&` e `RedeWifi&` — classes
**concretas**, sem método virtual, cujas bibliotecas nem são compiladas no alvo de
host. Consequência: a troca atômica do RF05.2, as três retentativas e todo o
tratamento de falha só existiam na placa. E são exatamente os caminhos que a bancada
**não** consegue provocar: "o cartão encheu no meio do download", "a renomeação
falhou", "a base chegou corrompida".

O projeto já tinha a regra certa e a aplicava — `LedRgb` e `Buzzer` são interfaces com
porte separado. Armazenamento e rede ficaram de fora, e ninguém notou porque o OTA
*funcionava*: foi validado de ponta a ponta com base real, Wi-Fi real e cartão real. O
caminho feliz estava provado; nenhum dos outros estava.

**A correção.** Quatro interfaces, cada uma o **subconjunto** que o OTA usa e não a
classe inteira: `Armazenamento` (7 métodos, sem `inicia` nem montagem de volume),
`Conexao` (2), `Baixador` (1) e `Pausa` (1). As concretas passaram a implementá-las e o
`AtualizadorOta` migrou para injeção por construtor, numa biblioteca nova
(`coruja_ota`) que compila nos **dois** alvos.

Dois detalhes que mereceram decisão:

* Os `descreve()` dos enums de erro viraram **`inline` no cabeçalho**. Estavam nos
  `.cpp` de hardware, então qualquer lógica portável que mencionasse um erro de cartão
  deixava de linkar no host — o tipo é portável, a implementação não.
* A interface de rede chama-se **`Conexao`**, não `Rede`: `Rede` já é a struct de uma
  credencial Wi-Fi em `Configuracao.h`. Uma é o enlace, a outra é uma linha da lista de
  prioridade.

**Abstrair o `sleep_ms` parecia exagero e não era.** Era a última amarra: as três
tentativas esperam 5 s entre si, e um teste que dormisse de verdade levaria 10 s para
exercitar o caminho de falha — a ponto de ninguém rodar. Com a espera injetada, o teste
**verifica** que esperou, quantas vezes e quanto, sem esperar. E pegou coisa: o mutante
que esperava também antes da primeira tentativa morre nesse assert.

**O que os 23 testes cobrem e antes não se cobria.** A ordem `abre → conclui → promove
→ grava versão`, que é o coração do RF05.2 — gravar a versão antes da troca deixaria o
cartão afirmando ter uma base que não tem, e o próximo boot carregaria a antiga achando
que está em dia. O cartão enchendo no meio do download. A base chegando corrompida ou
truncada. A renomeação falhando, que sai na hora em vez de insistir, porque não é falha
que se cure repetindo. E a promessa que dá sentido ao requisito: **falhar não piora o
que já existe** — em nenhum caminho de erro o `promove` é chamado nem a versão é
tocada.

Teste de mutação: 11 defeitos, 11 mortos.

---

## R-53 — As constantes de payload do UBX não estão medidas, e o ACK é quem julga

- **Onde:** `nucleo/Ubx.cpp`, `monta_cfg_prt_uart()`
- **Confiança:** ⚠️ Vindas da especificação do protocolo, **não de bancada**
- **Registrado em:** 2026-09-25
- **Status:** ⚠️ **ABERTO** — fecha quando o ACK for observado com o módulo

O montador de quadros UBX está testado contra quadros de referência calculados por uma
implementação independente em Python, então a **estrutura** — sincronismo, ordem dos
campos, tamanho em little-endian, faixa do checksum — está verificada. O que **não**
está é a **semântica dos bitmasks** do `CFG-PRT`:

| Campo | Valor usado | De onde vem |
| :--- | :--- | :--- |
| `mode` | `0x000008D0` | 8N1 da especificação: charLen=3 nos bits 6-7, parity=100b nos 9-11, 1 stop bit. O bit 4 vem ligado no padrão de fábrica |
| `inProtoMask` / `outProtoMask` | `0x0003` | UBX + NMEA. A saída precisa dos dois: NMEA pela RMC do RF01.1, UBX pelo ACK desta própria configuração |

**O juiz não sou eu, é o módulo.** Se ele responder `ACK`, aceitou; se responder `NAK`,
algum campo está errado — e é por isso que o parser de ACK e o montador nasceram
juntos, na mesma tarefa. Um montador sem quem leia a resposta seria escrever no escuro.

**Uma armadilha de bancada registrada antes de cair nela:** a resposta ao `CFG-PRT`
chega no **baud novo**. Quem enviar tem de reconfigurar a própria UART antes de esperar
o ACK, ou vai concluir que o módulo não respondeu quando ele respondeu — em 115200
contra uma porta ainda em 9600.

---

## R-52 — A máquina de zonas validada contra o simulador, e o monitor que escondia um estado

- **Onde:** `firmware/ferramentas/monitor_alertas.cpp`, `nucleo/Zonamento`
- **Confiança:** ✅ Medido: 630 sentenças da base real, transições registradas
- **Registrado em:** 2026-09-25
- **Status:** ✅ **VALIDADO**

**A sequência completa, num trecho só e no mesmo alvo:**

| tempo | zona | dist | vel | buzzer |
| :--- | :--- | ---: | ---: | :--- |
| 1:57.8 | APROX | 297 m | 55,0 | silêncio |
| 2:01.1 | MARGEM | 249 m | 63,0 | silêncio |
| 2:04.1 | PERIGO | 200 m | 70,0 | lenta |
| 2:06.1 | PERIGO | 164 m | 74,0 | rápida |
| 2:08.1 | PERIGO | 129 m | 80,0 | **pulso** |
| 2:10.1 | PERIGO | 97 m | 72,0 | rápida |
| 2:12.1 | MARGEM | 79 m | 62,0 | silêncio |
| 2:13.1 | segura | — | 62,0 | silêncio |

630 sentenças RMC, **zero erros de parsing**, distância fechando monotonicamente.

**Duas linhas valem por todo o resto, porque são discriminantes e não
confirmatórias** — só a histerese as explica, e a hipótese contrária prevê outra coisa:

* **72 km/h em `rápida`.** O limiar da faixa rápida é 72,6. Sem histerese, 72 cairia
  para `lenta`. Com os 2 km/h de rebaixamento na descida o limiar efetivo é 70,6, e 72
  fica. Observado vindo de `pulso`.
* **62 km/h saindo de Perigo.** `V_infra` é 66. Sem histerese teria saído já a 65; saiu
  a 62, que é abaixo dos 64 previstos.

**Reprodutibilidade.** A corrida foi repetida e os **10 eventos saíram idênticos** —
mesma zona, mesmo alvo, mesma distância ao metro (297, 249, 200, 164, 129, 97, 79) e
mesma faixa sonora. Só os carimbos de tempo variaram, em até 0,4 s, que é o arranque
do processo. Distância idêntica ao metro entre execuções diz que não há ruído no
caminho: a rota é determinística, o parser não perde amostra e a máquina não depende
de relógio de parede.

**O defeito que a validação encontrou, no instrumento.** A primeira corrida com a
escada completa **não mostrou o degrau dos 80 km/h**. A máquina estava certa: o monitor
é que só emitia evento na troca de zona ou de alvo, e subir de 70 para 80 mantém a zona
`PERIGO` — muda só a faixa sonora, que é precisamente o que o motorista ouve. Em pipe,
onde a linha de status viva é desligada, a passagem para `pulso` era invisível.

Corrigido: evento também na troca de faixa. Sem isso, a validação teria concluído
"tudo certo" sem nunca ter visto um dos três estados sonoros do RF03.7.

**O padrão, que já é o terceiro nesta sessão.** A malha completa no `.fzz`, o
`--sem-pausa` matando o teclado e este monitor sub-reportando não apareceram em teste
automático nenhum. Apareceram quando alguém olhou a saída e perguntou por que faltava
alguma coisa. Teste automático confirma o que se pensou em verificar; **ausência só se
nota olhando**.

---

## R-51 — O `D2` saiu do projeto, três revisões depois de ser declarado desnecessário

- **Onde:** `gera_fritzing.py`, `coruja_gps.fzz`, `bom_schematic.md`, `README.md`,
  `docs/adr/0009`
- **Confiança:** ✅ Verificado: netlist das três vistas antes e depois, e contra o
  gerador
- **Registrado em:** 2026-09-25
- **Status:** ✅ **REMOVIDO** — fecha o **R-16**

**O que aconteceu.** O autor perguntou se o `1N4148` era necessário, observando que ele
"não parecia estar fazendo muita coisa". Estava certo — e o projeto **já sabia**: o
R-16 registrou em revisão 1 que a justificativa ("roda-livre para o pico de retorno
magnético") estava incorreta, porque o SFM-27 é piezo ativo, carga capacitiva.

**E mesmo assim o componente ficou.** Foi rebaixado a "opcional" e sobreviveu a três
revisões: seguiu no BOM, no gerador, no `.fzz` e nos passos de montagem. Rebaixar a
opcional é o que se faz quando não se quer decidir — e o custo não é o diodo, é que
cada revisão seguinte teve de continuar explicando por que ele estava ali. A nota do
R-50 tinha três erros, e ela só existia para justificar um componente que não devia
existir.

**O último argumento caiu sozinho.** Mantê-lo se justificava como seguro contra uma
troca futura por buzzer eletromagnético. O R-49 soldou o buzzer; a troca passou a
exigir dessoldar, e nesse momento se solda o diodo junto. O seguro deixou de ter
quando ser útil — uma consequência da mudança anterior que ninguém tinha ido buscar.

**A pergunta que o autor fez e que eu não tinha feito.** *"Onde está a ligação de GND
do buzzer?"* O retorno não vai ao GND por fio: vai pelo transistor, em chaveamento de
lado baixo. Lendo a netlist parada, com o `Q1` cortado, o coletor sobe a ~12 V pelo
próprio buzzer e as duas pernas parecem no mesmo potencial. Isso agora está escrito no
gerador, junto da rede `BUZZ_COLETOR`, porque é exatamente a leitura que confunde quem
olha a lista de redes em vez do circuito.

**Um recado para a próxima vez que alguém mexer no `.fzz`.** Ao rotear a protoboard
depois desta remoção, o autor apagou os fios que ainda seguravam as ligações do buzzer
no **esquemático** e no **PCB** — vistas que o Fritzing rotea separadamente. A
protoboard ficou correta e completa; as outras duas ficaram com `BZ1:connector0` e
`Q1:connector2` isolados, e ninguém veria isso abrindo o arquivo, porque a vista que
se olha para montar é a que estava certa.

Pegou o verificador de netlist, não o olho. Vale a regra: **depois de mexer no layout,
conferir as três vistas contra o gerador antes de publicar** — são segundos, e é o
único jeito de saber que as vistas não divergiram entre si.

**Verificação.** 21 peças (eram 22), 163 fios preservados, 29 redes nas três vistas
sem alteração além dos dois pinos do diodo, zero ligações peça-a-peça inventadas, e
netlist idêntica à do gerador. O ramo do buzzer ficou com quatro nós: `+12 V → BZ`,
`BZ → coletor`, `emissor → GND`, `base → R4 → GPIO 5`.

---

## R-50 — A mudança do ADR 0009 não alcançou três trechos, e a minha correção do buzzer parou no meio

- **Onde:** `bom_schematic.md` (itens 19, seção dos conectores, nota do JST-XH, nota
  de exposição do conversor)
- **Confiança:** ✅ Lido no arquivo; o usuário apontou o item 19
- **Registrado em:** 2026-09-25
- **Status:** ✅ **CORRIGIDO**

**Primeira camada, anterior a mim.** O ADR 0009 trouxe o conversor para dentro do
gabinete e trocou a entrada de 5 V por 12 V. Três trechos do `bom_schematic.md`
ficaram para trás e continuaram afirmando a arquitetura antiga:

1. **Item 19** do BOM: *"Entrada de 5 V, depois do conversor"* — e ainda justificava as
   3 vias por não encaixarem no conector de 2 vias do buzzer.
2. **Nota "o trecho de 12 V NÃO pode usar JST-XH"**: partia de *"com o conversor fora,
   existem agora dois cabos externos"*. Com o conversor dentro, há um só.
3. **Nota de exposição**: *"com o conversor fora do gabinete, ele fica exposto a
   vibração e umidade"*.

O item 19 era o mais grave porque **contradizia uma nota vermelha do próprio
documento**: mandava usar JST-XH numa linha que a seção 0 proibia para JST-XH.

**Segunda camada, minha.** Ao remover o conector do buzzer (R-49), eu anexei ao fim da
seção dos conectores um parágrafo dizendo que ele deixou de existir — e deixei intactos
o **título** ("os dois conectores do aparelho"), a **tabela** com os dois, e a análise
de *"o que acontece hoje em cada troca"* entre eles. A seção passou a se contradizer
dentro de si mesma. É o R-44 de novo, em escala menor: mudei a coisa e não fui atrás
de tudo que a descrevia.

**Terceira camada, achada por uma pergunta.** Ao perguntar se o `1N4148` servia para
alguma coisa, o autor levou à nota *"diodo do buzzer"*, que tinha **três** erros ao
mesmo tempo: dizia **item 15** quando o `1N4148` é o item 14 (o 15 é o eletrolítico);
mandava pôr o **catodo no 5 V**, quando o ADR 0009 moveu a referência da roda-livre
para 12 V; e a linha do buzzer no BOM ainda o dizia *"trocável sem desmontar nada,
pelo JST de 2 vias"*. As três corrigidas.

Vale o registro de **como** apareceram: não por varredura, mas porque alguém leu o
esquema e perguntou por que uma peça estava ali. A deriva de documento não se acha
relendo o documento — quem o releu escreveu-o e lê o que quis dizer.

**Correção.** A seção foi reescrita para um conector só, com a progressão histórica
(Jack P2 → JST → header genérico → soldado) numa tabela, porque ela explica por que
cada passo intermediário não bastava. A nota do JST-XH foi marcada como **caduca** — a
regra não estava errada, a premissa dela é que sumiu.

**A conclusão que se inverteu.** Sem um segundo conector, a troca entre soquetes deixa
de ser modo de falha, e o que sobra na entrada é a **inversão de polaridade** (o TVS é
bidirecional e não protege contra ela — já registrado na análise de falhas). A
propriedade que importa no conector deixou de ser a contagem de vias e passou a ser o
**chaveamento mecânico**. Ou seja: o JST-XH, antes proibido ali, passa a ser adequado
pelo motivo oposto ao que o proibia. A família fica em aberto no item 19; o requisito
é ser chaveado.

---

## R-49 — O conector do buzzer foi removido, e o `.fzz` foi editado sem regerar

- **Onde:** `gera_fritzing.py`, `coruja_gps.fzz`, `bom_schematic.md`, `README.md`,
  `docs/adr/0009`
- **Confiança:** ✅ Verificado: netlist derivada do `.fzz` antes e depois, nas três
  vistas, e comparada com a do gerador
- **Registrado em:** 2026-09-25
- **Status:** ✅ **APLICADO** — fecha o R-06 em definitivo

**Mudança.** Com a caixa Patola em mãos, o buzzer passou a ser **soldado direto**, sem
conector. Os dois fios saem da placa e vão ao SFM-27 no painel.

**Por que isso é melhor do que o que havia.** O R-06 trocou o Jack P2 por um JST, e o
ADR 0009 trocou o JST por um header genérico. Cada passo administrou melhor o mesmo
risco — plugar a coisa errada no soquete errado — sem eliminá-lo, e o header genérico
até piorou, porque não é polarizado. Soldar **apaga** o risco: o aparelho passa a ter
um único conector externo, e não existe par para trocar. O preço é serviço, e é uma
escolha de primeira montagem, revisível.

**O método, que é o que vale registrar.** O R-29 fixou que o gerador é fonte da
*netlist* e o `.fzz` é fonte do *layout*, porque regerar descarta 155 fios roteados à
mão, 16 orientações e 4 notas. Regerar por cima teria custado esse trabalho de novo.
Em vez disso, o `.fzz` foi **editado cirurgicamente**: remover uma peça *passa-fio* é
apagá-la e unir entre si tudo que chegava a cada pino dela.

Isso rende um invariante que se verifica por máquina, e não por inspeção visual:

> **Remover um passa-fio não pode mudar rede nenhuma.**

Medido: 29 redes antes, 29 depois, idênticas nas três vistas depois de descontar os
dois pinos do conector; 163 fios preservados; 23 peças viraram 22. E a netlist do
`.fzz` editado foi comparada com a do gerador atualizado — **idênticas**, o que fecha
a convergência que o R-29 exigia manter à mão.

Um achado de passagem: o `.fzz` na árvore de trabalho **estava modificado e não
commitado**. A edição partiu dessa versão, então nada se perdeu, mas a comparação de
redes mostrou que a alteração pendente era cosmética.

### O invariante estava certo e mesmo assim passou um defeito

A primeira versão desta edição uniu os pontos de cada pino em **malha completa** —
todos com todos. Isso preserva a netlist, e o invariante passou. Só que malha completa
**inventa ligações diretas peça-a-peça que não existiam**, e o Fritzing as desenha:
apareceram seis, entre elas `BZ1:connector1 — Q1:connector2` e
`BZ1:connector0 — Conversor:connector0`. O autor abriu o arquivo e disse, com razão,
que o positivo e o negativo do buzzer pareciam ambos no coletor.

A substituição certa de um cubo é **outro cubo**, não uma malha: eleger um dos fios e
pendurar os demais nele, n−1 ligações, a mesma topologia que o pino do conector tinha.
Refeito assim: 40 ligações em vez de 92, todas envolvendo um fio, e **zero** ligações
peça-a-peça inventadas.

**A lição, que é sobre verificação e não sobre Fritzing.** "Remover um passa-fio não
pode mudar rede nenhuma" é um invariante **necessário e insuficiente**. Ele olha a
partição do grafo e é cego para as arestas que produzem essa partição — e as arestas
são o que se desenha. Faltava o segundo invariante, que agora existe e é igualmente
barato de checar:

> **Nenhuma ligação direta peça-a-peça pode surgir que já não existisse.**

É o mesmo erro de forma do R-47: o teste passou porque media a coisa certa pela metade,
e só um segundo ângulo mostrou o que o primeiro não alcançava. Lá o segundo ângulo foi
mutação; aqui foi um olho humano no desenho — o que é pior, porque significa que a
verificação automática não bastou e o autor teve de ser o revisor.

---

## R-47 — A suíte da máquina de zonas passou 53/53 de primeira, e 4 de 14 mutantes sobreviveram

- **Onde:** `nucleo/Zonamento.{h,cpp}`, `test/nucleo/ZonamentoTest.cpp`
- **Confiança:** ✅ Medido por teste de mutação: 14 defeitos injetados um a um,
  recompilando e rodando a suíte a cada um
- **Registrado em:** 2026-09-24
- **Status:** ✅ **CORRIGIDO** — 14/14 mortos depois dos ajustes

**Problema.** A suíte nova passou inteira na primeira execução. Isso não é notícia boa:
teste que nunca falhou não provou que falha quando devia. Injetando 14 defeitos
deliberados na implementação, **quatro passaram despercebidos** — e um deles era coberto
por um teste cujo comentário afirmava, em letras próprias, que ele pegaria exatamente
aquele defeito.

| Mutante | Por que escapou |
|---|---|
| Guarda de `kSemLimite` em `e_perigo` removida | A classificação testava `limite == 0` **antes** de chamar `e_perigo`. A guarda era código morto; o teste media a ordem do `if`, não a guarda |
| Janela de longitude com o raio de entrada no lugar do de saída | Toda a histerese era exercitada no eixo norte–sul, onde a longitude nunca aperta |
| Guarda de índice após troca de base | A base menor do teste caía fora do raio de qualquer jeito. O teste passava pelo motivo errado |
| Faixa sonora não zerada ao sair da zona | O teste usava 67 km/h, que dá `Lenta` **com ou sem** o defeito. Só uma velocidade dentro da janela de histerese distingue |

**O que mudou no código, não só nos testes.** Dois dos quatro apontaram defeito real:

1. `e_perigo` passou a ser consultado **primeiro**, e a guarda de `kSemLimite` dentro
   dele virou o único ponto que separa semáforo de perigo. Antes a regra estava escrita
   em dois lugares, e o segundo não era executado nunca.
2. O alvo passou a ser identificado por índice **e coordenadas**. Só o índice deixava
   uma base recarregada pôr outro radar na mesma posição do array e herdar a retenção de
   340 m que ele nunca conquistou — e `reinicia()`, que é o caminho certo, depende de o
   chamador lembrar.

**A lição.** É a mesma do R-41, por outro caminho. Lá eu medi a minha própria
configuração e li como se fosse o mundo; aqui eu escrevi um teste, li o comentário que
eu mesmo tinha escrito e tomei a afirmação como verificação. **Um teste verde só
informa alguma coisa se existir uma versão do código em que ele fica vermelho** — e
isso não se deduz olhando o teste, se mede quebrando o código de propósito. O script
que faz isso está descartado, mas reproduzir custa vinte linhas.

---

## R-48 — Decisões tomadas onde o RF03 é omisso (máquina de zonas)

- **Onde:** `nucleo/Zonamento.{h,cpp}`
- **Confiança:** ⚠️ Leitura minha do requisito, não ratificada
- **Registrado em:** 2026-09-24
- **Status:** ⚠️ **ABERTO** — em uso, sujeito a revisão

Seis pontos em que o requisito não fecha e eu escolhi. Ficam aqui para poderem ser
derrubados sem arqueologia:

1. **Histerese de 2 km/h na fronteira Aproximação/Perigo.** O RF03.2 diz que existe uma
   segunda histerese nas fronteiras de velocidade e manda "ver RF03.7", que só especifica
   o valor para as faixas sonoras. Adotei o mesmo 2 km/h por essa referência.
2. **Nenhuma histerese na fronteira Conforme/Margem.** Não é especificada, e as duas são
   silenciosas — o efeito de uma oscilação é a cor do LED tremular entre amarelo e rosa.
   YAGNI até isso incomodar de verdade na estrada.
3. **"À frente" por azimute, não por distância decrescente.** O RF03.1 permite os dois.
   O azimute funciona na primeira amostra e não quebra com o veículo parado; a distância
   decrescente precisa de duas amostras e mente no semáforo fechado.
4. **A histerese de velocidade erra para o lado mais grave.** Estando em Perigo, o
   limiar rebaixado vale para **todos** os pontos da janela, não só para o alvo vigente.
   É uma simplificação: o estado é um só. O erro possível é manter Perigo um pouco
   além do devido, que é o lado seguro.
5. **`SemSinal` é uma zona própria, não `Segura`.** O §4.1 pede LED apagado sem fix, e
   Segura é verde. Confundir as duas acenderia verde dentro de um túnel.
6. **O filtro de rumo abre abaixo de 5 km/h em ambos os usos** — sentido (RF02.3, que
   manda) e "à frente" (RF03.1, que não fala). Parado, o azimute do NEO-M8N é ruído, e
   a razão vale igual nos dois.

**Custo medido.** Contra a base real (18.304 pontos), 2.615 avaliações completas com o
veículo sobre a área de maior densidade: **0,90 µs por ciclo no host**. O orçamento a
4 Hz é de 250.000 µs. Mesmo com uma penalidade pessimista de 100× no RP2350 sobram três
ordens de grandeza — mas o número do Pico ainda **não foi medido**, e é ele que vale.

---

## R-38 — Cartão com mais de uma partição: o firmware montaria a errada, em silêncio

- **Onde:** `requirements.md` RNF03 · camada de cartão (ainda não escrita)
- **Confiança:** ✅ Verificado na documentação do FatFs (elm-chan.org), não de memória
- **Registrado em:** 2026-09-20
- **Status:** ✅ **CORRIGIDO** — sondagem implementada no `CartaoSd` (ADR 0007)

**Problema.** O RNF03 exige cartão *"formatado estritamente em FAT32"* e não diz
uma palavra sobre partições. O caminho padrão no Pico é o FatFs, e com
`FF_MULTI_PARTITION = 0` — que é o padrão — ele procura o volume assim:

> reads boot sectors and checks if it is an FAT VBR in order of LBA 0 as SFD
> format, 1st partition, 2nd partition, 3rd partition, ...

Ele percorre as partições, mas **para na primeira que for FAT válida**. O
critério é *"isto é FAT?"*, nunca *"isto contém o `coruja.cfg`?"*.

| Cartão | O que acontece |
|---|---|
| 1 partição FAT32 | funciona |
| 2 partições FAT, config na **segunda** | monta a primeira; `f_open` devolve `FR_NO_FILE` |
| config em partição **lógica** (dentro de estendida) | nunca encontrada: só as 4 primárias da MBR são olhadas |
| cartão GPT | não monta: exige `FF_LBA64=1`, que por sua vez exige exFAT |

A segunda linha é a pior. O `DET` do GPIO 14 diz "cartão presente", o mount diz
"ok", e só o `open` falha — o aparelho reporta **sem configuração** com o
arquivo fisicamente no cartão. O RF07 hoje distingue *ausente* de *ilegível*, e
este terceiro caso não tem para onde ir: ele se disfarça de um dos dois.

**Decisão.** Sondar **pelo arquivo, não pelo tipo**: `FF_MULTI_PARTITION = 1`,
`VolToPart[]` estática de 4 entradas, e no boot montar `0:` a `3:` em
sequência, ficando na primeira que contenha o `coruja.cfg`. Custa até quatro
tentativas de mount, uma vez, no boot; reaproveitando o mesmo objeto `FATFS`
entre as tentativas não custa RAM nenhuma.

Se nenhuma partição tiver o arquivo, a mensagem diz **quantas partições FAT
foram vistas** — que é o que transforma "sem configuração" de beco em
diagnóstico.

**Regra que vem junto:** o `radares.bin` tem de estar na **mesma partição** do
`coruja.cfg`. Dois critérios de seleção brigando dariam um empate silencioso.

---

## R-46 — O logger de cartão trocava "buffer preso" por "linhas perdidas em silêncio"

- **Onde:** `log/LoggerCartao.cpp`
- **Confiança:** ✅ Medido: 14 linhas sumiram de uma execução real, comparando o
  `coruja.log` com a captura da serial
- **Registrado em:** 2026-09-22
- **Status:** ✅ **CORRIGIDO** antes de ser publicado

**Problema.** O `descarrega()` zerava o buffer **antes** de tentar gravar, com o
raciocínio de que assim ele não ficaria preso se a gravação falhasse. Mas durante o
download da base a gravação falha **sempre**, de propósito — uma escrita em fluxo está
em curso e as duas usariam o mesmo descritor. Cada tentativa jogava fora 1 KiB de log
acumulado, inclusive linhas de **antes** do download começar.

Medido comparando o arquivo com a serial: sumiram 14 linhas — o fim da varredura de
Wi-Fi, a conexão, o IP, os dois `GET`, a decisão de baixar e metade do cabeçalho.

**O que a correção mudou, e não é só o tamanho.** Três coisas:

1. O buffer **não é mais zerado** quando a gravação falha. O conteúdo fica e sai na
   próxima descarga, que o `main` dispara logo após o OTA.
2. Foi de 1 KiB para **4 KiB**, dimensionado pela janela medida: as 14 linhas ocupam
   ~900 bytes, e 4 KiB dão folga de quatro vezes.
3. Se ainda assim algo for descartado, o arquivo ganha
   `[AVISO] log: N linha(s) perdida(s) por buffer cheio`.

A terceira é a que importa mais. **Buraco declarado é diagnóstico; buraco silencioso é
armadilha** — ele faz quem lê concluir que o evento não aconteceu. Foi o que quase
aconteceu comigo: a primeira leitura do arquivo me pareceu normal até eu comparar linha
a linha com a serial.

Verificado depois da correção: o trecho do download aparece **inteiro** no `coruja.log`,
e nenhum aviso de perda.

---

## R-45 — Um aviso do OTA afirmava o contrário do que o log da mesma execução mostrava

- **Onde:** `rede/AtualizadorOta.cpp`
- **Confiança:** ✅ Visto no log de bancada de 2026-09-22
- **Registrado em:** 2026-09-22
- **Status:** ✅ **CORRIGIDO**

**Problema.** Ao fim de cada atualização o firmware registrava:

```
[WARN ] ota: nao foi gravada: o leitor de cartao ainda nao existe (R-38)
```

Duas coisas erradas. O leitor **existe** — quatro linhas acima, no mesmo log, ele
tinha lido o `coruja.cfg`. E o R-38 é a referência errada: aquele achado era sobre
sondagem de partições. O que falta é a **escrita** do RF05.2.

**Como envelheceu.** O texto era verdadeiro quando foi escrito, no dia em que o leitor
de fato não existia. Quando o leitor entrou, ninguém releu a mensagem — ela não faz
parte de nenhum teste, não quebra build, e só aparece no fim de uma execução bem
sucedida, que é justamente quando não se lê o log com atenção.

**O padrão, que já apareceu quatro vezes neste projeto.** Texto que descreve o estado
do sistema envelhece em silêncio:

| Onde | O que afirmava | Quando deixou de valer |
| :--- | :--- | :--- |
| `.fzz` versionado | LED de cátodo comum | R-33, e só foi notado 4 dias depois |
| Mensagem do boot | "DET em nível baixo" | ao inverter a polaridade (R-41) |
| `descreve(Ausente)` | "(pelo DET)" | mesma correção |
| Aviso do OTA | "o leitor não existe" | ao implementar o leitor |

A defesa que funcionou nos dois casos de nível elétrico foi **medir em vez de
afirmar** — a mensagem passou a imprimir o valor lido. Aqui não há valor a medir, e a
única defesa real é reler as mensagens quando a funcionalidade que elas descrevem
muda. Vale procurar as demais antes de cada entrega.

---

## R-44 — O gerador do Fritzing continuou fiando os capacitores que o R-36 proibiu

- **Onde:** `gera_fritzing.py` · `coruja_gps.fzz`
- **Confiança:** ✅ Lido no `NETS`, e confirmado no diff do commit do R-36
- **Registrado em:** 2026-09-21
- **Status:** ✅ **CORRIGIDO** — `C3` e `C4` removidos das peças, das redes e das posições

**Problema.** O R-36 concluiu, com medição, que os 100 nF em `CLK` e `DT` **impedem
qualquer decodificação** de quadratura, e a montagem passou a ser sem eles. O commit
que registrou isso se chama *"os 100 nF de debounce matavam a quadratura"*.

Mas ele **não tocou nos capacitores no gerador**. Conferido no diff: as únicas
mudanças foram o `LED_R/G/B_GPIO` do R-35. O `C3` e o `C4` continuaram na lista de
peças e ligados às redes `ENC_CLK` e `ENC_DT` por mais dois dias.

Ou seja: o esquemático que o projeto publica mandava instalar exatamente os
componentes que o projeto já sabia que quebram o encoder.

**Por que passou.** A mensagem do commit descrevia a conclusão, não o escopo da
mudança — ela falava dos capacitores porque *o achado* era sobre eles, enquanto o
*diff* tratava do LED. Quem lesse a mensagem concluiria que o gerador estava
atualizado. Eu escrevi esse commit.

**A defesa que faltava.** Nenhuma: o `bom_schematic.md` e o gerador não têm
verificação cruzada automática, e é a segunda vez que divergem (a primeira foi o
R-40, com o leitor SD). Vale considerar um teste que compare as tabelas do documento
com o `NETS`, como já existe entre o `gera_config.py` e o `Configuracao.h`.

---

## R-43 — O fio do `DET` tem contato intermitente

- **Onde:** fiação de bancada (protoboard)
- **Confiança:** ✅ Observado duas vezes na mesma alimentação
- **Registrado em:** 2026-09-20
- **Status:** ✅ **ENCERRADO por remoção** — o card detect saiu do projeto (ADR 0010).
  A causa raiz acabou sendo outra: a chave do soquete não abre por completo e deixa o
  pino em 1,13 V, na zona indeterminada. "Contato intermitente" era a leitura errada de
  um pino que nunca esteve em nível lógico definido.

**Observação.** Numa única inicialização, com o cartão inserido e sem ninguém tocar
em nada:

```
boot   -> DET: pull-down=BAIXO  pull-up=ALTO  sem pull=ALTO   (FLUTUANDO)
clique -> DET: pull-down=ALTO   pull-up=ALTO  sem pull=ALTO   (acionado)
```

Segundos de diferença, mesma alimentação, mesma fiação. O contato abre e fecha.

**Por que importa mais do que parece.** O aparelho vai num carro, e vibração é o
ambiente em que contato marginal falha. Um `DET` intermitente não produz erro claro:
produz "cartão ausente" esporádico, e o RF07 reagiria a isso como se o motorista
tivesse tirado o cartão — enquanto dirige.

Também é uma armadilha de diagnóstico. Uma leitura flutuante **parece conclusiva**, e
já sustentou dois diagnósticos errados nesta mesma investigação (R-41, R-42). Com
contato intermitente, o mesmo teste dá respostas diferentes em execuções seguidas, e a
tentação é explicar a diferença por software.

**Encaminhamento.** Reassentar com firmeza ou soldar, e confirmar com o
`diagnostica_det()` em várias inicializações seguidas — uma só não basta, que é
precisamente a lição do R-42.

---

## R-42 — O fio do `DET` não chega a pino nenhum: o GPIO 14 está flutuando

- **Onde:** fiação de bancada · `armazenamento/CartaoSd.cpp`
- **Confiança:** ✅ Medido sob os três pulls internos na mesma inicialização
- **Registrado em:** 2026-09-20
- **Status:** ✅ **CORRIGIDO na época**, e **sem objeto** desde 2026-09-22: o card
  detect saiu do projeto (ADR 0010). A medição continua válida como registro — o pino
  era mesmo acionado nos dois estados — mas a chave do soquete nunca foi confiável, e é
  isso que o R-43 acabou revelando.

**Medição.** Com o cartão **inserido**:

```
DET (GPIO 14): pull-down=BAIXO  pull-up=ALTO  sem pull=ALTO
```

O nível acompanha o pull interno. O pino está **flutuando** — nada o aciona.

**O que isso invalida.** Todas as leituras anteriores do `DET` mediam o pull configurado
no firmware, não o cartão. Inclusive a que gerou o R-41.

**O que isso NÃO invalida.** A primeira leitura de todas — fiação original, sem cartão,
pull-down, resultado ALTO — continua sendo um pino **acionado em alto**, porque um pino
flutuante com pull-down leria baixo. Ou seja: na fiação original o `DET` chegava a algum
pino com pull-up, e depois da refiação passou a não chegar a nada.

**Instrumento que resolveu.** Ler o mesmo pino sob pull-down, pull-up e sem pull, na
mesma inicialização. Nenhuma leitura isolada distingue flutuante de acionado, e todas
as leituras isoladas *parecem* conclusivas — foi o que sustentou dois diagnósticos
errados seguidos.

O diagnóstico passou a rodar **a cada clique**, não só no boot, para que mover o fio de
pino em pino não exija reiniciar nem regravar.

**Resolvido na bancada.** Com o fio reassentado, o pino saiu de flutuante para
acionado, e os dois estados foram medidos sob os três pulls:

| Cartão | pull-down | pull-up | sem pull |
| :--- | :---: | :---: | :---: |
| dentro | ALTO | ALTO | ALTO |
| fora | BAIXO | BAIXO | BAIXO |

**Cartão dentro = ALTO**, que é a polaridade documentada pela Adafruit e a que estava
configurada originalmente. `card_detected_true` de volta a 1, com pull-down interno.

**Consequência para o R-40.** No R-41 eu também desacreditei a explicação do R-40 —
"o fio teria ido para um pino de dados com pull-up" — argumentando que um pino de
dados não ficaria baixo ao inserir o cartão. Aquele "baixo" era o artefato do pino
flutuante. Como agora se sabe que a fiação correta dá **BAIXO com slot vazio**, e a
leitura original deu **ALTO com slot vazio**, o fio de fato não estava no `DET`: a
explicação do R-40 volta a ser a melhor disponível.

---

## R-41 — RETRATADO: eu "medi" uma polaridade que era o meu próprio pull interno

> ⚠️ **Esta conclusão estava errada e foi publicada num commit.** O que segue é o
> registro do erro; a correção de fato está no R-42.
>
> Eu concluí que o card detect tinha polaridade invertida a partir de duas leituras:
> slot vazio deu ALTO, cartão dentro deu BAIXO. O que eu não considerei é que as duas
> foram feitas com **pull-down interno habilitado** e o pino **flutuando** — então a
> leitura BAIXO não media o cartão, media a minha própria configuração.
>
> Provado depois lendo o mesmo pino sob os três pulls na mesma inicialização:
> `pull-down=BAIXO  pull-up=ALTO  sem pull=ALTO`. O nível **acompanha o pull**, com o
> cartão inserido. Nada aciona o GPIO 14.
>
> **A lição:** eu já sabia que duas leituras não determinam uma polaridade — escrevi
> isso no próprio R-41. E então fiz exatamente o mesmo erro uma camada acima: troquei
> "duas leituras" por "duas leituras com a variável errada fixa". A pergunta que
> faltava não era *"quantas medições?"*, era **"o que mais poderia produzir este
> número?"** — e a resposta, o pull que eu mesmo tinha ligado, estava no meu código.
>
> O texto original segue abaixo, sem edição, porque uma conclusão errada apagada não
> ensina nada.

### (texto original, incorreto)

## R-41 — A polaridade do card detect era o inverso da documentada, e eu expliquei o sintoma errado

- **Onde:** `bom_schematic.md` §2 · `armazenamento/hw_config.cpp`
- **Confiança:** ✅ Três leituras na bancada, com o firmware relatando o nível
- **Registrado em:** 2026-09-20
- **Status:** ❌ **RETRATADO** — a conclusão estava errada; ver o aviso acima e o R-42.
  O assunto ficou sem objeto em 2026-09-22, com a remoção do card detect (ADR 0010).

**Problema.** O módulo deste projeto tem pull-up no `DET` e uma chave que o aterra
**quando o cartão entra**. O documento citava a Adafruit dizendo o contrário — citação
correta para o breakout 4682, errada para este módulo.

Medido:

| Estado | GPIO 14 |
| :--- | :--- |
| módulo desconectado | ALTO (pull-up interno) |
| ligado, slot vazio | ALTO (pull-up do módulo) |
| ligado, cartão dentro | **BAIXO** (chave ao GND) |

O firmware relatava **"cartão presente" com o slot vazio** e **"sem cartão" com o
cartão dentro** — e, por causa do primeiro, seguia para o `f_mount` e falhava com uma
mensagem sobre partições. O sintoma apontava para longe da causa.

**O erro de raciocínio, que é o que vale registrar.** Ao ver "cartão presente" com o
slot vazio, montei uma explicação: o fio do `DET` teria ido parar no `DAT2` por causa
de um pino faltando na tabela (R-40), e `DAT2` tem pull-up. A explicação era coerente,
citava fonte do fabricante e estava **errada** — um pino de dados não ficaria baixo ao
inserir o cartão.

A tabela de fato estava errada e a correção do R-40 continua valendo. Mas eu usei um
defeito verdadeiro para explicar um sintoma que ele não causava, e isso é pior do que
não ter explicação: fechou a investigação cedo. O que resolveu foi a terceira leitura
— com cartão —, que ninguém tinha feito ainda. **Duas leituras não determinam uma
polaridade.**

**Correção.** `card_detected_true = 0` e pull-up interno, que cobre os três estados
inclusive o de módulo ausente. O comentário no `hw_config.cpp` traz a tabela das três
leituras, e manda medir em vez de adotar a folha de dados de um módulo parecido.

---

## R-40 — A tabela do leitor SD tinha 8 pinos; a placa tem 9, e o `DET` saía errado

- **Onde:** `bom_schematic.md` §2 · fiação de bancada
- **Confiança:** ✅ Pinos contados na placa física pelo autor em 2026-09-20
- **Registrado em:** 2026-09-20
- **Status:** ✅ **CORRIGIDO** — tabela relida e substituída

**Problema.** A tabela listava `3V, GND, CLK, DO/SO, CMD/SI, D3/CS, DAT2, DET` — oito
posições. A placa tem **nove**: falta o `D1`, entre `D3` e `DAT2`.

O erro não é de nome, é de **posição**. Quem contasse pela tabela poria o fio do `DET`
na posição 8, que na placa real é o `DAT2`.

**Por que isso não falha de forma visível.** A Adafruit documenta *"pull ups are
provided on all SDIO logic pins"*. `DAT2` fica **alto por construção**. O firmware,
lendo o GPIO 14, relata **"cartão presente"** para sempre — com cartão, sem cartão,
com o slot vazio. Depois falha na montagem, e a mensagem que sobra fala de partição,
não de fiação.

Foi exatamente a sequência observada: `DET` em alto com o slot vazio, e nenhum dos
cinco volumes montando no clique.

**O que levou ao erro.** A revisão 3 marcava a tabela como *"conferida na placa,
2026-09-17"*, e ela estava errada — a revisão 2 já tinha errado antes, de outro jeito
(`VCC/GND/CLK/DI/DO/CS`, por inferência). **Duas conferências seguidas, dois erros.**

A lição não é "conferir na placa", que já estava escrito. É que um pino **ausente** de
uma tabela não tem como ser notado ao comparar rótulo por rótulo: a leitura casa até
o ponto em que diverge, e as posições seguintes parecem certas porque os nomes ainda
existem, só que deslocados. A defesa é **contar os pinos** antes de comparar os nomes.

**Correção.** Tabela substituída pelos nove pinos. O aviso no documento agora manda
contar antes de fiar.

---

## R-39 — `__has_include` de um arquivo ausente não deixa rastro, e o build mente

- **Onde:** `firmware/src/main.cpp` · `scripts/gera_config_bancada.py`
- **Confiança:** ✅ Reproduzido: o binário não continha o SSID após gerar e recompilar
- **Registrado em:** 2026-09-20
- **Status:** ✅ **CORRIGIDO** — o gerador toca no `main.cpp`

**Problema.** A configuração de bancada entra por
`#if __has_include("placa/ConfigBancada.h")`. Quando o arquivo **não existe**, o
compilador não o abre — e portanto não o registra como dependência. O CMake
passa a considerar o `main.cpp` em dia.

O resultado: gerar a configuração e recompilar produz um firmware que **continua
dizendo "sem configuração"**, com o arquivo ali, recém-criado. Nada falha, nada
avisa, e a hipótese natural passa a ser "o script não funcionou" — que é onde se
perde a tarde.

Medido: após gerar o cabeçalho e rodar o build, `strings` no ELF não encontrava
o SSID. Só depois de um `touch src/main.cpp` ele aparecia.

**Correção.** O gerador toca no `main.cpp` depois de escrever, e diz o comando
de recompilação. A alternativa — declarar a dependência no CMake — não resolve
o caso que importa, que é justamente o do arquivo que ainda não existe.

---

## R-37 — O RF05 mandava baixar a base e nunca dizia de onde

- **Onde:** `requirements.md` RF05 · `docs/adr/0002`
- **Confiança:** ✅ Verificado por varredura: não havia URL em nenhum arquivo
- **Registrado em:** 2026-09-20
- **Status:** ✅ **CORRIGIDO** — duas URLs em `coruja.cfg`

**Problema.** O RF05 exigia que o aparelho *"conecte ao ponto de acesso
configurado e baixe a versão atualizada da base de radares"*. **Origem nenhuma
era especificada** — nem URL, nem servidor, nem protocolo de consulta. Uma
varredura por `url`, `servidor`, `http` e `endpoint` nos documentos só
encontrava o RF05.2 exigindo HTTPS para um download cuja origem não existia.

A lacuna nasceu quando o repositório virou público: a origem dos dados é do
pipeline privado, e o repositório público **não pode** conhecê-la. Mas em vez
de virar configuração, ela simplesmente sumiu do texto.

**Correção.** Duas chaves em `coruja.cfg`:

| Chave | Papel |
| :--- | :--- |
| `url_versao` | devolve **uma linha de texto qualquer** — data, número, hash. O firmware guarda ao lado do `radares.bin` e compara como texto |
| `url_base` | entrega o `radares.bin`. O RF05.2 exige HTTPS |

A resposta da versão ser texto livre é deliberado: **não impõe formato ao
servidor**, e quem clonar o projeto escolhe o dele sem tocar no firmware.

**Duas decisões que vieram junto**, ambas do autor:

1. **Até 5 redes Wi-Fi, em ordem de prioridade.** Ao clicar no encoder o
   aparelho varre e conecta na primeira da lista que estiver visível. A
   prioridade é a **ordem do arquivo**, não o sinal mais forte — explícita,
   previsível, e o log consegue dizer por que escolheu.
2. **Todo o resto sai da configuração.** Brilho, fuso, tolerâncias e
   calibração passam a viver no código. Ver o ADR 0002 para o critério.

**O que o gerador escondia.** Ao revisar, apareceu que o `ConfigCalibracao.h`
gerado **não era incluído por nenhum arquivo do firmware** — seis menções, todas
em comentário. Os valores medidos no R-05 estavam num header que ninguém lia. É
pior que um valor errado, porque não há sintoma. A calibração foi para
`led/Calibracao.h`, versionada e com teste.

**Formato numerado em vez de `ssid:senha`.** Senha de Wi-Fi pode conter
qualquer caractere, inclusive o separador. O parser divide no **primeiro `=`**,
e há teste com `senha=a=b=c`.

---

# 🟡 Lacunas de requisitos

## L-01 — Comportamento sem fix de GPS

Nenhum requisito define o que acontece em túnel, garagem ou cold start: o que a tela
mostra, o que o LED RGB faz, se o último radar detectado continua válido e por quanto
tempo. Hoje a matriz IHM não tem linha para esse estado.

## L-02 — Orçamentos de recursos — 🟡 **memória FECHADA, corrente e boot abertos**

Faltavam números medidos, não estimados. A **memória** agora está medida no binário
real (2026-09-28, `coruja_gps.elf` do build do RP2350):

| | medido | de | ocupação |
| :--- | ---: | ---: | ---: |
| Flash (`text`) | **465,4 KiB** | 4096 KiB | 11,4% |
| SRAM (`.bss`) | **338,3 KiB** | 520 KiB | 65,0% |
| SRAM livre para pilha e heap | **181,7 KiB** | — | 35,0% |

Quem ocupa o `.bss`, pelos seis maiores símbolos:

| Símbolo | Tamanho | O que é |
| :--- | ---: | :--- |
| `g_pontos` | 280,8 KiB | a base de radares, 24.000 × 12 B — **83% do total** |
| `memp_memory_PBUF_POOL_base` | 35,9 KiB | pool de buffers do lwIP |
| `ram_heap` | 3,9 KiB | heap do lwIP |
| `pedaco` (`CartaoSd::le_em_fluxo`) | 4,0 KiB | buffer de leitura em fluxo |
| `cyw43_state` | 2,4 KiB | estado do rádio |
| `g_texto_config` | 2,0 KiB | texto do `coruja.cfg` |

**O que esses números dizem.** A base domina, como o ADR 0006 previu, e a decisão de
reservar 24.000 em vez dos 40.000 do teto foi o que manteve a folga: o teto custaria
mais 187 KiB e **não caberia** — 525 KiB de `.bss` num chip de 520 KiB. Fora a base, o
firmware inteiro cabe em 57 KiB, e o maior item nem é nosso, é o pool do lwIP.

Flash a 11,4% não é restrição para nada que esteja planejado, incluindo o driver de
display, que é o próximo grande consumidor previsto.

**Continuam abertos:** o orçamento de **corrente** (medido com a placa montada e
alimentada pela fonte de bancada) e o **tempo de boot** — nenhum dos dois se mede no
binário.

## L-03 — Falha ou ausência do cartão SD

Não especificado: boot sem cartão, cartão não-FAT32 (o RNF03 exige FAT32 mas não define
o comportamento quando a exigência não é atendida), `speedcam.txt` ausente ou ilegível.

## L-04 — Watchdog e recuperação de travamento

Crítico neste produto: o motorista não pode reiniciar o dispositivo dirigindo. Não há
requisito de watchdog, nem de comportamento após reset inesperado.

## L-05 — Faixa térmica e especificação de temperatura dos componentes

Painel de veículo ao sol passa de 60 °C. O capacitor eletrolítico (item 14) não tem
temperatura especificada — **exigir 105 °C, não 85 °C**. Avaliar também a faixa de
operação do display IPS e do cartão SD. Nenhum RNF trata disso.

## L-06 — Conversão e tratamento da velocidade — ✅ **FECHADA**

A sentença RMC entrega velocidade em nós. O fator ×1,852 e a estratégia de suavização
(média móvel, filtro) não estavam especificados, apesar de a velocidade ser o gatilho
da transição Aproximação → Perigo.

**Resolvido em duas frentes, e o registro estava faltando (2026-09-28):**

1. **Conversão:** implementada em `nucleo/Nmea.cpp`, `kNoParaKmh = 1,852`, com teste.
2. **Suavização: não haverá**, por decisão do autor em 2026-09-23 — *"não há
   necessidade de implementar suavização de velocidade antes de ter certeza que isso é
   um problema real"*. Princípio YAGNI.

A segunda merece nota, porque é uma decisão e não uma omissão. Suavizar velocidade tem
um custo que não é óbvio: **atrasa a detecção da subida**, que é exatamente a direção
em que o alerta precisa ser rápido. Uma média móvel de 4 amostras a 4 Hz adiciona meio
segundo de atraso à transição Margem → Perigo. Se o ruído de velocidade do NEO-M8N vier
a incomodar em uso real, o lugar de tratá-lo é a histerese do RF03.7, que já existe e
não custa atraso — não um filtro novo.

## L-07 — Estratégia de verificação e testes

Nenhum dos dois documentos menciona verificação. Mínimo necessário:
- Testes unitários do parser NMEA (incluindo checksum inválido, campos vazios, sem fix).
- Testes unitários do Haversine e do filtro de rumo com vetores conhecidos —
  **incluindo o caso de wraparound de R-04**.
- Replay de logs NMEA gravados em estrada, para validar transições de zona sem dirigir.
- Teste de interrupção de energia durante o OTA (valida R-10).

---

## L-08 — Linguagem e runtime do firmware não declarados

Nenhum dos documentos diz se o firmware é **C/C++ (Pico SDK)** ou **MicroPython**. Para
esta arquitetura a escolha não é livre: o orçamento de `formato_dados.md` §1 assume
overhead de runtime de ~20 KB, compatível com o SDK em C. O heap do MicroPython mais o
interpretador não deixariam espaço para 214 KB de base **e** 150 KB de framebuffer — e
nesse caminho o particionamento em quadrantes (Anexo A) voltaria a ser obrigatório.

**Comparação completa de desempenho em `formato_dados.md` §9.** Resumo: **velocidade não
é o critério** — MicroPython usaria ~4% do orçamento de ciclo, e o custo dominante é a
transferência SPI do display (~29 ms), igual nas duas linguagens. Os critérios reais são
**memória** e, sobretudo, **dual core**: o `_thread` do port RP2 tem GIL, então a divisão
core 0 = GPS / core 1 = UI que o RNF04 e o R-15 exigem não se realiza em MicroPython.

**Recomendação:** C/C++ com o Pico SDK, registrado como requisito não-funcional. É a
decisão de maior alavancagem em aberto no projeto — resolve ou reabre R-02. O teste de
heap da §9.5 fecha a dúvida em 30 segundos no hardware real.

## L-09 — Precisão numérica não especificada (FPU de precisão simples)

A FPU do Cortex-M33 do RP2350 é de **precisão simples**; `double` é emulado em software.
Nenhum documento especifica em que precisão rodam os cálculos geográficos, e a combinação
que parece natural é justamente a errada: `float` tem ~7,2 dígitos significativos,
enquanto uma coordenada como `-23.537216` precisa de 8 — e a Haversine subtrai números
próximos, ampliando o erro exatamente em distâncias curtas.

Ver `formato_dados.md` §4.1: a forma **equirretangular sobre diferenças** é 5–8× mais
barata, tem erro <0,01% em 300 m e escapa do problema naturalmente, porque opera sobre
números pequenos. Escrever como requisito, junto com a decisão sobre manter ou não a
Haversine do RF02.

# ⚪ Correções editoriais

| # | Onde | Atual | Correto |
| :---: | :--- | :--- | :--- |
| E-01 | `bom_schematic.md`, tabela BOM, última linha | Item **29** | Item **19** |
| E-02 | `requirements.md` RNF05 | "Moduloridade Mecânica" | "Modularidade Mecânica" |
| E-03 | `requirements.md` RNF02 | "transistor NPN acuado como chave" | "transistor NPN atuando como chave" |
| E-04 | `requirements.md`, matriz IHM, linha Zona Segura | "Fondo Preto" | "Fundo Preto" |
| E-05 | `bom_schematic.md` seção 1 + `requirements.md` RNF01 | Referências a `VBUS` como nó de entrada | Atualizar em conjunto ao aplicar **R-01** |

---

# ⚖️ Nota

Se o dispositivo for de fato instalado no carro, vale saber que no Brasil há distinção
entre **detectores/inibidores de radar** (proibidos) e **bases de dados de posição de
radares fixos** com alerta por GPS — categoria em que este projeto se enquadra, como
navegadores comerciais. Não verifiquei a resolução CONTRAN vigente; irrelevante para
bancada, mas bom saber antes de fixar no painel.

---

# ✅ Checklist de fechamento

```text
BLOQUEADORES
[ ] R-01  Entrada de energia migrada para VSYS (pino 39) + Schottky
[x] R-02  RESOLVIDO — premissa errada; 18.294 pontos cabem em RAM (formato_dados.md §1)
[x] R-03  RESOLVIDO — array ordenado por lat + busca binária (formato_dados.md §4)
[ ] R-04  Diferença circular + porta de velocidade + DirType (0=omni, 2=bi)
[~] R-19  DECIDIDO: Zona de Semáforo silenciosa, LED amarelo/vermelho 2 Hz
                └─ implementação pendente; DEPENDE do R-05 (sem verde, não há amarelo)
[x] R-05  CONCLUIDO 19/09 — 330R/470R/150R e PWM ambar 19,6% / rosa 15,7%.
          Duas previsoes erradas: verde precisou do MAIOR resistor, e os
          nominais de PWM erravam por 2,3x e 3,8x.
[x] R-06  RESOLVIDO — o conector do buzzer foi REMOVIDO (2026-09-25): fios
          soldados direto. Sobra um unico conector externo. Ver R-49
[x] R-21  RESOLVIDO — GPS+GLONASS a 4 Hz nominal, piso de 3 Hz
[ ] R-28  Trecho de 12 V sem conector JST-XH (direto no conversor)

RELEVANTES
[ ] R-07  Sequência de configuração UBX especificada no RF01
[ ] R-08  Parser aceita $GNRMC e $GPRMC + valida checksum
[ ] R-09  Condição de aproximação + histerese nas zonas
[x] R-10  RESOLVIDO — RF05.2 implementado e verificado na bancada: baixa para
          .tmp gravando enquanto chega, valida, roda .bak e promove. Boot
          carrega em fluxo do cartao com recuo para o .bak  OTA com validação, escrita atômica e rollback
                └─ validação de integridade já especificada em formato_dados.md §2
[ ] R-11  Credenciais de Wi-Fi fora do firmware
[ ] R-12  OTA condicionado a veículo parado
[ ] R-13  Orçamento de corrente do 3V3_OUT medido
[ ] R-14  Alimentação do GPS definida (5V ou 3V3)
[ ] R-15  Exclusão mútua no SPI0 + divisão entre cores no RNF04
[x] R-16  RESOLVIDO — o diodo foi REMOVIDO (2026-09-25), nao so a
          justificativa corrigida. Ver R-51
[ ] R-17  Transistor com margem de corrente (BC337 / 2N2222)
[x] R-18  RESOLVIDO — cabeçalho explícito + DirType confirmado; converte.py verificado
[ ] R-22  Resistor de 1 kΩ em série no `GPIO 0 → GPS RX`
[x] R-23  RESOLVIDO — faixas sonoras reancoradas em V_infra
[x] R-24  RESOLVIDO — precedência Perigo > Margem > Semáforo > Conforme
[x] R-25  RESOLVIDO — LED RGB exclusivo de estado de via, 5 estados
[x] R-26  RESOLVIDO — ícone 🚦+🏎 composto nos 2.994 pontos de TYPE=2 (requirements.md §4.1)
[x] R-30  RESOLVIDO — BASE INDISPONÍVEL persistente na faixa inferior (requirements.md §4.1)
[x] R-31  RESOLVIDO — TVS 24 V + 470 uF/50 V na entrada de 12 V (bom_schematic.md itens 27-28)
[~] R-32  Faixa 3 virou pulso de 10 Hz. MEDIDO em bancada (27/09): 52 dB em
          5 V contra 75 dB em 12 V -- 23 dB, ~14x em pressao, confirma o
          ADR 0009. Medido a ~5 cm com telefone. Extrapolado para 80 cm da
          ~51 dB contra 75-85 dB de cabine: indicio DESFAVORAVEL. Resolver
          antes a discrepancia com os 105 dB da folha (em que tensao?)
[x] R-33  RESOLVIDO — LED e de ANODO comum; logica invertida no firmware e na netlist
[~] R-34  Tabela de pinagem do GPS criada e gerador corrigido; serigrafia A CONFERIR na placa
[x] R-35  RESOLVIDO — LED com vermelho no GPIO 8 e azul no 6; o mapa descreve a placa
[x] R-36  RESOLVIDO — monta SEM capacitor; RF04 revisado, maquina de estados e o
          debounce. RC de 1-10 nF fica como contingencia documentada.
[x] R-37  RESOLVIDO — url_versao e url_base em coruja.cfg; ate 5 redes Wi-Fi
          por ordem de prioridade. LeitorConfig com 26 testes.
[x] R-61  DECIDIDO — modo noturno pelo GPS (nascer/por do sol), nao por
          LDR; troca o BRILHO entre dois presets e nao a paleta
[x] R-60  APLICADO — LED azul fixo para 'vivo sem protecao'; escuro
          passa a significar so falta de energia. Teste guarda a regra
[x] R-59  FEITO — previa do produto no terminal com o codigo real;
          alinhamento de texto virou explicito; radar movel deixou de
          ter icone proprio, e o §4.1 foi emendado
[~] R-58  layout e brilho FEITOS (35 testes, 15/15 mutantes). Porte do
          painel espera identificar o controlador na bancada. E o
          framebuffer de 150 KB do RNF07 nao e necessario: redesenho
          parcial, .bss inalterado
[x] R-57  FEITO — laco do produto ligando GPS, zonas, LED e buzzer. 22
          testes, 11/11 mutantes. Falta so o visor
[x] R-56  FEITO — configurador do GPS com ACK por comando, e a troca de
          baud na ordem certa. 19 testes, 10/10 mutantes
[x] R-55  itens 5 e 6 CORRIGIDOS. LoggerCartao com 16 testes (regressao do
          R-46). CartaoSd com 21 testes sobre uma fachada falsa de FatFs de
          217 linhas -- o defeito do R-38 agora falha a suite em 30 ms. Minha
          avaliacao de que exigiria disco em RAM estava errada e esta
          retratada no corpo do R-55
[x] R-54  CORRIGIDO — OTA passa a receber interfaces; 310 linhas que so
          rodavam na placa ganharam 23 testes de host, 11/11 mutantes
[~] R-53  ABERTO — bitmasks do CFG-PRT vem da especificacao, nao de
          bancada. Fecha quando o ACK for observado com o modulo
[x] R-52  VALIDADO — sequencia APROX/MARGEM/PERIGO/segura no mesmo alvo
          contra o simulador, com as 3 faixas sonoras e as duas
          histereses observadas de forma discriminante
[x] R-51  REMOVIDO — D2 fora do projeto; fecha o R-16, aberto desde a rev.1
[x] R-50  RESOLVIDO — 3 trechos do bom_schematic ainda descreviam a
          arquitetura anterior ao ADR 0009, e a minha propria correcao do
          buzzer deixou a secao dos conectores contradizendo a si mesma
[x] R-49  APLICADO — buzzer soldado direto; .fzz editado cirurgicamente em
          vez de regerado, com a netlist verificada nas 3 vistas
[~] R-48  ABERTO — seis decisoes minhas onde o RF03 e omisso (histerese de
          2 km/h em Aproximacao/Perigo, "a frente" por azimute, SemSinal como
          zona propria). Em uso, sujeitas a revisao
[x] R-47  RESOLVIDO — 4 de 14 mutantes sobreviveram a uma suite que passou
          53/53 de primeira, um deles coberto por comentario falso. 14/14 apos
[x] R-38  RESOLVIDO — FF_MULTI_PARTITION=1 e sondagem das 4 particoes primarias
          procurando o arquivo. static_assert quebra o build se o override do
          ffconf.h se perder; verificado por teste negativo. ADR 0007.
[x] R-46  RESOLVIDO — logger de cartao perdia 1 KiB por descarga falha durante
          o download. Buffer 4 KiB, conteudo preservado na falha, e buraco
          declarado no arquivo em vez de silencioso
[x] R-45  RESOLVIDO — aviso do OTA dizia "o leitor de cartao nao existe" com o
          cartao recem-lido no mesmo log. Texto que descreve estado envelhece
          em silencio; e a quarta ocorrencia registrada
[x] R-44  RESOLVIDO — C3/C4 saíram do gerador. O commit do R-36 falava deles na
          mensagem e mexia so no LED; o .fzz mandou instalar por 2 dias os
          capacitores que matam a quadratura
[x] R-43  ENCERRADO por remocao — nao era contato intermitente: a chave do
          soquete nao abre por completo e deixa 1,13 V, na zona indeterminada.
          Card detect saiu do projeto (ADR 0010); GPIO 14 livre
[x] R-42  RESOLVIDO — fio reassentado; medido nos dois estados sob os tres
          pulls: cartao dentro=ALTO, slot vazio=BAIXO. card_detected_true=1,
          como estava antes do R-41. Diagnostico dos tres pulls fica no codigo
[!] R-41  RETRATADO — a "polaridade invertida" era o meu proprio pull-down num
          pino flutuante. Conclusao errada, publicada em commit. Ver R-42
[x] R-40  RESOLVIDO — leitor SD tem 9 pinos, nao 8; faltava o D1 e o DET saia
          deslocado para DAT2, que tem pull-up e mentia "cartao presente"
[x] R-39  RESOLVIDO — o gera_config_bancada.py toca no main.cpp; sem isso o
          build ficava em dia com uma configuracao que ele nunca leu
[x] R-29  RESOLVIDO — o .fzz gerado com o circuito de alimentacao foi ajustado
          a mao e promovido a canonico. O antigo estava defasado em cinco
          pontos, inclusive LED como catodo comum, e ficou no historico
[x] R-20  RESOLVIDO — TYPE=5 é Radar Móvel; hipótese de trecho controlado descartada

LACUNAS
[ ] L-01  Comportamento sem fix de GPS
[~] L-02  MEMORIA FECHADA (28/09, medida no .elf): flash 465,4 KiB de 4096
          (11,4%), .bss 338,3 KiB de 520 (65%), 181,7 KiB livres. A base e 83%
          do .bss. Corrente e tempo de boot seguem abertos
[~] L-03  Cartao ausente e cartao ilegivel sao UM caso so desde 2026-09-22
          (ADR 0010), reportado como "cartao ausente ou ilegivel". Falta o
          tratamento de IHM para base ausente
[ ] L-04  Watchdog e recuperação
[ ] L-05  Faixa térmica (capacitor 105 °C)
[x] L-06  FECHADA — x1,852 implementado e testado; suavizacao NAO havera,
          por decisao de 2026-09-23 (YAGNI). Ruido, se houver, se trata na
          histerese que ja existe, que nao custa atraso
[ ] L-07  Estratégia de verificação e testes
[ ] L-08  Linguagem e runtime declarados (C/C++ SDK recomendado; ver §9)
[ ] L-09  Precisão dos cálculos geográficos definida (FPU é single-precision)

EDITORIAIS
[ ] E-01 a E-05

PENDÊNCIAS DE formato_dados.md
[x] A-01  RESOLVIDO — layout e semântica confirmados      (= R-18)
[ ] A-02  Runtime decidido                                (= L-08)
[ ] A-03  Estimativas de memória medidas no binário real   (→ L-02)
```
