paulovitorbal/coruja_gps/firmware/src/display/Sprites.h

// Gerado por scripts/gera_sprites.py. NÃO EDITAR À MÃO.
//
// Arte do Twemoji, © Twitter Inc. e colaboradores.
// Licenciada sob CC-BY 4.0 — ver docs/licencas/CC-BY-4.0-twemoji.txt.

#pragma once
#include <cstdint>

namespace coruja::sprite {

constexpr int kLado = 40;

/// RGB565, linha por linha de cima para baixo. O transparente
/// do PNG ja vem composto sobre PRETO: desenhar sobre outro
/// fundo deixaria uma moldura escura em volta do icone.

/// U+1F3CE 🏎, de radar_1f3ce.png.
constexpr std::uint16_t kRadar[kLado * kLado] = {
    0xF75C, 0xF75C, 0xF75C, 0xF75C, 0xF75C, 0xF75C, 0xF75C, 0xF75C, 0xF75C, 0xF75C,
    0xF75C, 0xF75C, 0xF75C, 0xF75C, 0xF75C, 0xF75C, 0xF75C, 0xF75C, 0xF75C, 0xF75C,
    0xF75C, 0xF75C, 0xF75C, 0xF75C, 0xF75C, 0xF75C, 0xF75C, 0xF75C, 0xF75C, 0xF75C,
    0xF75C, 0xF75C, 0xF75C, 0xF75C, 0xF75C, 0xF75C, 0xF75C, 0xF75C, 0xF75C, 0xF75C,
    0xF75C, 0xF75C, 0xF75C, 0xF75C, 0xF75C, 0xF75C, 0xF75C, 0xF75C, 0xF75C, 0xF75C,
    0xF75C, 0xF75C, 0xF75C, 0xF75C, 0xF75C, 0xF75C, 0xF75C, 0xF75C, 0xF75C, 0xF75C,
    0xF75C, 0xF75C, 0xF75C, 0xF75C, 0xF75C, 0xF75C, 0xF75C, 0xF75C, 0xF75C, 0xF75C,
    0xF75C, 0xF75C, 0xF75C, 0xF75C, 0xF75C, 0xF75C, 0xF75C, 0xF75C, 0xF75C, 0xF75C,
    0xF75C, 0xF75C, 0xF75C, 0xF75C, 0xF75C, 0xF75C, 0xF75C, 0xF75C, 0xF75C, 0xF75C,
    0xF75C, 0xF75C, 0xF75C, 0xF75C, 0xF75C, 0xF75C, 0xF75C, 0xF75C, 0xF75C, 0xF75C,
    0xF75C, 0xF75C, 0xF75C, 0xF75C, 0xF75C, 0xF75C, 0xF75C, 0xF75C, 0xF75C, 0xF75C,
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
    0x31A7, 0x2967, 0x29A7, 0x29A7, 0x2967, 0x31A7, 0x31A7, 0x31C7, 0x31C8, 0x9491,
    0xF75C, 0xF75B, 0xF75C, 0xF75C, 0xF75C, 0xF75C, 0xF75C, 0xF75C, 0xF75C, 0xF75C,
    0xF75C, 0xF75C, 0xF75C, 0xF75C, 0xF75C, 0xF75C, 0xF75C, 0xF75C, 0xF75C, 0xF75C,
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
};

}  // namespace coruja::sprite
