paulovitorbal/coruja_gps/firmware/src/placa/Pinos.h

#pragma once
#include <cstddef>

/// Mapa único de pinos do Coruja GPS.
///
/// **Esta é a fonte da verdade do firmware.** Antes deste arquivo os pinos
/// viviam espalhados: três no `LedRgbAnodoComum`, três no `EncoderKy040`, e os
/// outros doze só em prosa no `bom_schematic.md`. Um mapa espalhado é um mapa
/// que divergiu — a pergunta "o GPIO 15 já está usado?" não tinha onde ser
/// respondida.
///
/// Transcrito do `bom_schematic.md` e conferido contra a netlist do
/// `gera_fritzing.py`, que é quem desenha o esquema.
///
/// O **número físico** de cada pino vem no comentário porque os dois sistemas
/// de numeração coexistem no projeto: o firmware fala em GPIO, o documento de
/// montagem e a serigrafia falam em pino físico, e a tradução errada é fonte
/// de fiação errada.
namespace coruja::pinos {

// ---------------------------------------------------------------------------
// GPS — UART0
// ---------------------------------------------------------------------------

/// Pico transmite, GPS recebe. Vai por um resistor de 1 kΩ em série (R-22):
/// limita a corrente caso o módulo apresente nível de 5 V no `RX`.
constexpr unsigned kGpsTx = 0;   // pino físico 1
/// Pico recebe, GPS transmite.
constexpr unsigned kGpsRx = 1;   // pino físico 2

// ---------------------------------------------------------------------------
// Encoder rotativo KY-040
// ---------------------------------------------------------------------------
//
// Conferidos na placa física em 2026-09-17: a ordem de serigrafia do módulo é
// o INVERSO da que costuma aparecer documentada, e a revisão 2 do
// bom_schematic tinha a sequência trocada — o que colocaria 3,3 V e GND
// diretamente em dois GPIO.

// ⚠️ **Sem capacitor de debounce em `CLK` e `DT`.** A revisão 2 do
// `bom_schematic.md` mandava 100 nF, e medido na placa esse valor **impede
// qualquer decodificação**: ele achata fases de 45 a 128 ms em pulsos de 1 ms
// e apaga o estado `(0,0)`, que é onde a quadratura codifica direção. O
// debounce é a máquina de estados do `DecodificadorQuadratura`. Ver R-36.
constexpr unsigned kEncoderClk = 2;  // pino físico 4
constexpr unsigned kEncoderDt  = 3;  // pino físico 5
constexpr unsigned kEncoderSw  = 4;  // pino físico 6

// ---------------------------------------------------------------------------
// Buzzer
// ---------------------------------------------------------------------------

/// Base do transistor, por um resistor de 1 kΩ. O GPIO **não** fornece a
/// corrente do buzzer: é o RNF02.
constexpr unsigned kBuzzerBase = 5;  // pino físico 7

// ---------------------------------------------------------------------------
// LED RGB — ânodo comum
// ---------------------------------------------------------------------------
//
// ⚠️ O ânodo comum vai ao `k3V3Out`, e cada cátodo desce por seu resistor até
// o GPIO: nível BAIXO acende. Ver R-33 e `LedRgbAnodoComum`.
//
// ⚠️ **Vermelho e azul NÃO seguem a ordem crescente de GPIO.** A ordem das
// pernas deste LED de 10 mm não é R-G-B, e a fiação foi mantida como está: o
// mapa abaixo descreve **a placa como construída**, que é o papel deste
// arquivo. Determinado empiricamente em 2026-09-19 pelo modo de calibração —
// o firmware acendia um canal por vez e a cor observada não batia, com as
// compostas confirmando: âmbar saía ciano e rosa saía lilás. Ver R-35.
//
// Os resistores foram medidos (R-05) e **acompanham a cor**, não o GPIO:
// 330 Ω no vermelho, 470 Ω no verde, 150 Ω no azul. A ordem é o inverso da
// sensibilidade do olho, que tem pico no verde.

constexpr unsigned kLedVermelho = 8;  // pino físico 11; resistor 330 Ω
constexpr unsigned kLedVerde    = 7;  // pino físico 10; resistor 470 Ω
constexpr unsigned kLedAzul     = 6;  // pino físico  9; resistor 150 Ω

// ---------------------------------------------------------------------------
// Cartão microSD
// ---------------------------------------------------------------------------

// ⚠️ **O GPIO 14 é o `RST` do display desde 2026-09-29** — e é a **terceira**
// função que esse pino recebe. Antes foi o LED de Wi-Fi (R-25) e depois o
// card detect do soquete de microSD, removido em 2026-09-22 (ADR 0010): o
// projeto reage igual a cartão ausente e a cartão ilegível, e a chave do
// soquete não abria por completo — deixava o pino em 1,13 V, dentro da zona
// indeterminada da lógica de 3,3 V.
//
// **Consequência prática para quem monta:** se sobrar qualquer fio do soquete
// do cartão neste pino, ele disputa o `RST` do display. Um `RST` puxado para
// baixo mantém o ST7789V em reset permanente — tela apagada, nenhum comando
// surtindo efeito, e a continuidade medindo perfeita, porque o fio do Pico
// até o módulo continua lá. É um sintoma caro de diagnosticar, e foi por um
// fio muito parecido com este que a primeira ligação do painel custou várias
// horas.

constexpr unsigned kSdCs  = 17;  // pino físico 22

// ---------------------------------------------------------------------------
// Cartão microSD — SPI0, agora sozinho
// ---------------------------------------------------------------------------
//
// ✅ **O barramento deixou de ser compartilhado em 2026-09-29.** O display
// migrou para o SPI1 (abaixo), e com isso caem três coisas de uma vez: o
// mutex entre display e cartão, a reconfiguração de velocidade a cada
// transação — o cartão exige <= 400 kHz na inicialização e o display quer
// dezenas de MHz — e a possibilidade de o buffer de nível do leitor carregar
// as linhas do display, que chegou a ser suspeito na primeira ligação.
//
// O motivo imediato foi espaço na protoboard: o display ocupava cinco pinos
// do lado direito e o lado esquerdo tinha seis livres em sequência. A
// separação dos barramentos veio de brinde, e é o ganho que fica.

constexpr unsigned kSpiMiso = 16;  // pino físico 21; cartão DO/SO
constexpr unsigned kSpiSck  = 18;  // pino físico 24; cartão CLK
constexpr unsigned kSpiMosi = 19;  // pino físico 25; cartão CMD/SI

// ---------------------------------------------------------------------------
// Display — SPI1, exclusivo
// ---------------------------------------------------------------------------
//
// Seis pinos físicos em sequência (14 a 20), com o GND do pino 18 no meio do
// bloco. GP10 e GP11 não são escolha arbitrária: são as funções `SCK` e `TX`
// do SPI1 no RP2350, e são os únicos pinos livres do lado esquerdo que
// servem para isso.
//
// O módulo é um `GMT024-08-SPI8P ver. 1.3`: ST7789V, 240x320, **8 pinos sem
// MISO** (R-62). Não há linha de leitura porque não há o que ler — nem o
// registrador de ID, nem estado nenhum.

constexpr unsigned kDisplaySck  = 10;  // pino físico 14; módulo SCL
constexpr unsigned kDisplayMosi = 11;  // pino físico 15; módulo SDA
constexpr unsigned kDisplayCs   = 12;  // pino físico 16
constexpr unsigned kDisplayDc   = 13;  // pino físico 17
constexpr unsigned kDisplayRst  = 14;  // pino físico 19

/// PWM do backlight. Frequência >= 20 kHz: abaixo de ~1 kHz o painel cintila
/// de forma perceptível na visão periférica e pode dar efeito estroboscópico
/// com feições da estrada, e entre 1 e 20 kHz alguns módulos assobiam. A curva
/// de brilho é perceptual, não linear (requirements.md §4.1).
constexpr unsigned kDisplayBacklight = 15;  // pino físico 20

// ---------------------------------------------------------------------------
// Pinos de alimentação — NÃO SÃO GPIO
// ---------------------------------------------------------------------------
//
// Estão aqui como documentação, para que o número não seja procurado em outro
// arquivo. Não passe nenhum deles a `gpio_init()`.

/// Saída de 3,3 V do regulador da placa. É **a fonte**: leitor SD, encoder,
/// ânodo comum do LED e, se o módulo não tiver regulador próprio, o VCC do
/// display.
constexpr unsigned kPinoFisico3V3Out = 36;

/// ⚠️ **Entrada de *enable* do regulador, não uma fonte.** Pino **adjacente**
/// ao `3V3_OUT`, com pull-up de 100 kΩ para `VSYS` na placa. Puxá-lo ao GND
/// desliga o regulador de 3,3 V — e o RP2350 com ele.
///
/// Está declarado aqui **só para ser reconhecido e evitado**. O sintoma de
/// ligar uma carga nele é a placa dar boot e morrer ao acender o LED, o que
/// parece bug de firmware.
constexpr unsigned kPinoFisico3V3En = 37;

/// Entrada de 5 V, depois do Schottky. **Nunca** `VBUS` (pino 40), que é
/// ligado direto ao conector USB — ver R-01.
constexpr unsigned kPinoFisicoVsys = 39;
/// O Pico tem oito pinos de GND: 3, 8, 13, 18, 23, 28, 33 e 38.
constexpr unsigned kPinoFisicoGnd = 38;

// ---------------------------------------------------------------------------
// Invariantes guardadas pelo compilador
// ---------------------------------------------------------------------------

/// Todos os GPIO que o firmware usa. Acrescentar um pino aqui é obrigatório:
/// é esta lista que as verificações abaixo enxergam.
constexpr unsigned kTodosOsGpio[] = {
    kGpsTx,     kGpsRx,      kEncoderClk, kEncoderDt,  kEncoderSw,
    kBuzzerBase, kLedVermelho, kLedVerde, kLedAzul,   kSdCs,
    kSpiMiso,   kSpiSck,     kSpiMosi,
    kDisplaySck, kDisplayMosi, kDisplayCs,
    kDisplayDc, kDisplayRst, kDisplayBacklight,
};
constexpr std::size_t kQuantosGpio =
    sizeof kTodosOsGpio / sizeof *kTodosOsGpio;

namespace detalhe {

constexpr bool sem_repeticao(const unsigned* v, std::size_t n) {
    for (std::size_t i = 0; i < n; ++i) {
        for (std::size_t j = i + 1; j < n; ++j) {
            if (v[i] == v[j]) {
                return false;
            }
        }
    }
    return true;
}

/// O RP2350 tem GPIO 0 a 29, mas o cabeçalho do Pico expõe só 0–22, 26, 27 e
/// 28. Os quatro que faltam não são livres: **23, 24, 25 e 29 são do módulo
/// Wi-Fi CYW43** na variante W, e o projeto usa Wi-Fi para a atualização OTA.
constexpr bool disponivel_no_cabecalho(unsigned g) {
    return g <= 22 || g == 26 || g == 27 || g == 28;
}

constexpr bool todos_disponiveis(const unsigned* v, std::size_t n) {
    for (std::size_t i = 0; i < n; ++i) {
        if (!disponivel_no_cabecalho(v[i])) {
            return false;
        }
    }
    return true;
}

}  // namespace detalhe

// Um pino atribuído duas vezes é o erro que mais custa a achar numa placa
// montada: dois periféricos disputam a linha e os dois funcionam pela metade.
// O compilador passa a recusar antes de existir placa.
static_assert(detalhe::sem_repeticao(kTodosOsGpio, kQuantosGpio),
              "dois periféricos foram atribuídos ao mesmo GPIO");

static_assert(detalhe::todos_disponiveis(kTodosOsGpio, kQuantosGpio),
              "algum GPIO não existe no cabeçalho do Pico, ou pertence ao "
              "módulo Wi-Fi CYW43 (23, 24, 25, 29)");

// ⚠️ **PENDENTE:** subiu de 17 para 19 em 2026-09-29, quando o display
// migrou para o SPI1 e o `SCK`/`MOSI` dele deixaram de ser os mesmos do
// cartão. O `bom_schematic.md` §2 e a netlist do `gera_fritzing.py` **ainda
// descrevem a pinagem antiga** — atualizar os dois é trabalho combinado com
// o autor para depois de o painel estar funcionando.
static_assert(kQuantosGpio == 19,
              "a contagem de GPIO mudou: confira o bom_schematic.md e a "
              "netlist do gera_fritzing.py antes de ajustar este número");

}  // namespace coruja::pinos
