paulovitorbal/coruja_gps/firmware/src/armazenamento/CartaoSd.h

#pragma once
#include <cstddef>
#include <cstdint>

#include "armazenamento/Armazenamento.h"
#include "armazenamento/Arquivario.h"

namespace coruja {

class Logger;

// `ErroCartao` e `descreve()` vivem em `Armazenamento.h`, portavel.

/// Acesso ao cartão microSD.
///
/// **A presença não é detectada por pino dedicado.** O card detect foi
/// removido em 2026-09-22 (ADR 0010): o projeto reage igual a cartão ausente e
/// a cartão ilegível, então a distinção não pagava o GPIO, o fio, e uma chave
/// de soquete que se mostrou não confiável — ela não abria por completo, e
/// deixava o pino em 1,13 V, na zona indeterminada da lógica de 3,3 V.
///
/// A presença passa a ser **inferida da montagem**: se o cartão monta, existe.
/// Implementa os **dois** recortes: `Armazenamento`, que o OTA usa para
/// escrever e promover, e `Arquivario`, que a remessa usa para enumerar, ler e
/// apagar. São interfaces separadas de propósito -- ver `Arquivario.h`.
class CartaoSd : public Armazenamento, public Arquivario {
public:
    /// Prepara o driver e o barramento SPI. Pode ser chamado no boot.
    void inicia(Logger& log);

    /// Monta e lê um arquivo inteiro para `destino`.
    ///
    /// Monta e desmonta a cada chamada, de propósito: o cartão é removível, e
    /// manter um volume montado através de uma remoção é como se corrompe
    /// sistema de arquivos. Ver R-38 sobre a escolha da partição.
    ErroCartao le_arquivo(const char* nome, char* destino, std::size_t capacidade,
                          std::size_t* lidos, Logger& log) override;

    /// Chamada a cada pedaço lido. Não pode bloquear por muito tempo.
    using AoLerPedaco = void (*)(void* contexto, const std::uint8_t* bytes,
                                 std::size_t tamanho);

    /// Lê um arquivo **em fluxo**, entregando pedaços a quem chamou.
    ///
    /// É como a base é carregada no boot: o `radares.bin` tem 214 KB e o vetor
    /// decodificado ocupa 281 KB, então não existe momento em que os dois
    /// caibam juntos. Os bytes viram `Ponto` na passagem.
    ErroCartao le_em_fluxo(const char* nome, AoLerPedaco ao_ler, void* contexto,
                           std::size_t* lidos, Logger& log);

    /// Acrescenta bytes ao fim de um arquivo, criando-o se não existir.
    ///
    /// Usado pelo log. Abre e fecha a cada chamada de propósito: o cartão é
    /// removível, e manter um arquivo de log aberto indefinidamente é como se
    /// perde um sistema de arquivos ao puxar o cartão.
    ErroCartao acrescenta_arquivo(const char* nome, const char* conteudo,
                                  std::size_t tamanho, Logger& log) override;

    /// Grava um arquivo pequeno inteiro, de uma vez. Para a linha de versão.
    ErroCartao grava_arquivo(const char* nome, const char* conteudo,
                             std::size_t tamanho, Logger& log) override;

    // -----------------------------------------------------------------------
    // Escrita em fluxo — o download não cabe em RAM
    // -----------------------------------------------------------------------
    //
    // O `radares.bin` tem 214 KB e sobram ~185 KiB. Não há como baixar inteiro
    // e depois gravar: os bytes vão para o cartão **enquanto chegam**, no mesmo
    // callback que alimenta o verificador de CRC.
    //
    // O volume é o mesmo onde o `coruja.cfg` foi encontrado — não se procura de
    // novo, porque a base tem de acompanhar a configuração que a definiu.

    /// Monta e abre `nome` para escrita, truncando. Deixa o volume montado.
    ErroCartao abre_para_escrita(const char* nome, Logger& log) override;

    /// Acrescenta bytes ao arquivo aberto. `false` em qualquer falha — quem
    /// chama deve parar de alimentar e abortar.
    bool escreve(const std::uint8_t* bytes, std::size_t tamanho) override;

    /// Fecha o arquivo e desmonta. Use quando o conteúdo foi aceito.
    ErroCartao conclui_escrita(Logger& log) override;

    /// Fecha, **apaga** o arquivo e desmonta. Use quando o conteúdo foi
    /// recusado: melhor não deixar um `.tmp` meio escrito no cartão.
    void descarta_escrita(const char* nome, Logger& log) override;

    /// A troca atômica do RF05.2, passos 3 e 4: a base vigente vira `.bak` e o
    /// temporário vira a base. Monta e desmonta por conta própria.
    ///
    /// A ordem importa. Renomear é a operação mais barata e mais atômica que o
    /// FAT oferece — nenhum byte de dado se move —, então a janela em que o
    /// cartão está inconsistente é de uma atualização de diretório.
    ErroCartao promove(const char* temporario, const char* base,
                       const char* reserva, Logger& log) override;

    bool existe(const char* nome, Logger& log);

    // -----------------------------------------------------------------------
    // Arquivario -- o que a remessa de dados usa
    // -----------------------------------------------------------------------

    /// Enumera a raiz do volume de trabalho, ignorando diretórios.
    ErroCartao lista(AoListar ao_listar, void* contexto, Logger& log) override;

    /// Abre para leitura e **deixa o volume montado**, como a escrita em
    /// fluxo faz. O descritor é separado do da escrita: durante um envio o
    /// log pode querer gravar no cartão, e um descritor só serviria aos dois
    /// ao mesmo tempo -- ou seja, a nenhum.
    ErroCartao abre_para_leitura(const char* nome, std::size_t* tamanho,
                                 Logger& log) override;
    bool le(std::uint8_t* destino, std::size_t capacidade,
            std::size_t* lidos) override;
    bool rebobina() override;
    void fecha_leitura() override;

    ErroCartao remove(const char* nome, Logger& log) override;

private:
    /// Monta o volume de trabalho e devolve seu prefixo em `raiz`.
    ErroCartao monta_volume(char* raiz, std::size_t tam_raiz, Logger& log);
    /// O par de `monta_volume`. Só desmonta de verdade na última.
    void desmonta_volume(const char* raiz);

    /// Quantas operações seguram o volume montado AGORA.
    ///
    /// ⚠️ **O FatFs não aninha montagem.** `f_unmount` zera a área de trabalho
    /// do volume, e toda operação seguinte — inclusive um `FIL` já aberto —
    /// passa a falhar com `FR_NOT_ENABLED`. Sem contagem, gravar uma linha de
    /// log no meio de outra operação do cartão a desmontava por baixo:
    ///
    ///  - no `promove()`, entre os dois `f_rename`, o volume caía e a base
    ///    ficava só como `.bak` — o cartão sem `radares.bin`;
    ///  - no envio, o fluxo de leitura aberto morria no meio do arquivo.
    ///
    /// Os dois aconteceram no aparelho em 07/10/2026. Contar faz a montagem
    /// pertencer à operação mais externa, que é quem sabe quando acabou.
    unsigned montagens_ = 0;
    char     raiz_montada_[4] = {};

    bool iniciado_ = false;
    /// Volume onde o `coruja.cfg` foi achado. -1 enquanto não se sabe; aí a
    /// escrita sonda como a leitura faz.
    int  volume_ativo_ = -1;
    bool escrevendo_ = false;
    bool lendo_ = false;
    char raiz_aberta_[4] = {};
    char raiz_leitura_[4] = {};
};

}  // namespace coruja
