paulovitorbal/coruja_gps/firmware/src/nucleo/BaseRadares.cpp

#include "nucleo/BaseRadares.h"

#include <cstdio>
#include <cstring>

#include "log/Logger.h"

namespace coruja {

namespace {

std::uint32_t le_u32(const std::uint8_t* p) {
    return static_cast<std::uint32_t>(p[0]) |
           (static_cast<std::uint32_t>(p[1]) << 8) |
           (static_cast<std::uint32_t>(p[2]) << 16) |
           (static_cast<std::uint32_t>(p[3]) << 24);
}

std::int32_t le_i32(const std::uint8_t* p) {
    return static_cast<std::int32_t>(le_u32(p));
}

std::uint16_t le_u16(const std::uint8_t* p) {
    return static_cast<std::uint16_t>(p[0] | (p[1] << 8));
}

constexpr const char* kOrigem = "base";

void registra(Logger* logger, Nivel nivel, const char* msg) {
    if (logger != nullptr) {
        logger->registra(nivel, kOrigem, msg);
    }
}

ResultadoCarga falha(Logger* logger, ErroBase erro) {
    registra(logger, Nivel::Error, descreve(erro));
    return {erro, 0};
}

}  // namespace

const char* descreve(ErroBase erro) {
    switch (erro) {
        case ErroBase::Nenhum:                return "sem erro";
        case ErroBase::TamanhoInvalido:       return "tamanho invalido";
        case ErroBase::MagicInvalido:         return "assinatura invalida";
        case ErroBase::VersaoInvalida:        return "versao nao suportada";
        case ErroBase::EscalaInvalida:        return "expoente de escala inesperado";
        case ErroBase::TamRegistroInvalido:   return "tamanho de registro inesperado";
        case ErroBase::BaseVazia:             return "base sem nenhum ponto";
        case ErroBase::ExcedeuTeto:           return "acima do teto de 40.000 pontos";
        case ErroBase::ContagemInconsistente: return "contagem discorda do tamanho";
        case ErroBase::ExcedeuCapacidade:     return "mais pontos do que a capacidade";
        case ErroBase::CrcInvalido:           return "CRC-32 nao confere";
        case ErroBase::ForaDeOrdem:           return "nao ordenado por latitude";
        case ErroBase::RegistroInvalido:      return "registro com campo fora do dominio";
    }
    return "erro desconhecido";
}

bool decodifica_registro(const std::uint8_t* registro, Ponto* destino,
                         std::int32_t* lat_bruta) {
    const std::uint8_t flags   = registro[10];
    const auto         sentido = static_cast<std::uint8_t>(flags & 0x03U);
    const auto         tipo    = static_cast<std::uint8_t>((flags >> 2) & 0x07U);
    if (!tipo_valido(tipo) || !sentido_valido(sentido)) {
        return false;
    }

    const std::int32_t lat_e = le_i32(registro);
    *lat_bruta = lat_e;
    *destino = Ponto{
        static_cast<float>(lat_e) / kEscala,
        static_cast<float>(le_i32(registro + 4)) / kEscala,
        registro[8],
        registro[9],  // rumo ja vem quantizado no arquivo; nao expandir
        static_cast<TipoPonto>(tipo),
        static_cast<Sentido>(sentido),
    };
    return true;
}

ResultadoCarga carrega_base(const std::uint8_t* bytes, std::size_t tamanho,
                            Ponto* destino, std::size_t capacidade,
                            Logger* logger) {
    // O cabecalho tem tamanho VARIAVEL: 16 bytes na versao 1, 20 na 2. A
    // versao so se conhece depois de ler os 6 primeiros, entao a checagem
    // de tamanho minimo usa o menor dos dois e o resto vem depois.
    if (bytes == nullptr || destino == nullptr ||
        tamanho < kTamCabecalhoSemData) {
        return falha(logger, ErroBase::TamanhoInvalido);
    }
    if (le_u32(bytes) != kMagic) {
        return falha(logger, ErroBase::MagicInvalido);
    }
    const std::uint16_t versao = le_u16(bytes + 4);
    // Aceita as duas: um cartao com base v1 continua valido, e o aparelho
    // so fica sem a data. Recusa-la o deixaria SEM BASE ate a proxima
    // atualizacao, que e muito pior.
    if (versao != kVersao && versao != kVersaoSemData) {
        return falha(logger, ErroBase::VersaoInvalida);
    }
    const std::size_t cab =
        versao == kVersaoSemData ? kTamCabecalhoSemData : kTamCabecalho;
    if (tamanho < cab || (tamanho - cab) % kTamRegistro != 0) {
        return falha(logger, ErroBase::TamanhoInvalido);
    }
    if (bytes[6] != kExpoenteEscala) {
        return falha(logger, ErroBase::EscalaInvalida);
    }
    if (bytes[7] != kTamRegistro) {
        return falha(logger, ErroBase::TamRegistroInvalido);
    }

    const std::uint32_t declarados = le_u32(bytes + 8);
    if (declarados == 0) {
        return falha(logger, ErroBase::BaseVazia);
    }
    if (declarados > kTetoPontos) {
        return falha(logger, ErroBase::ExcedeuTeto);
    }
    const std::size_t reais = (tamanho - cab) / kTamRegistro;
    if (declarados != reais) {
        return falha(logger, ErroBase::ContagemInconsistente);
    }
    if (reais > capacidade) {
        return falha(logger, ErroBase::ExcedeuCapacidade);
    }

    const std::uint32_t crc_esperado = le_u32(bytes + 12);
    if (crc32(bytes + cab, tamanho - cab) != crc_esperado) {
        return falha(logger, ErroBase::CrcInvalido);
    }

    std::int32_t lat_anterior = -2147483647 - 1;
    for (std::size_t i = 0; i < reais; ++i) {
        const std::uint8_t* r = bytes + cab + i * kTamRegistro;
        std::int32_t lat_e = 0;
        if (!decodifica_registro(r, &destino[i], &lat_e)) {
            return falha(logger, ErroBase::RegistroInvalido);
        }
        if (lat_e < lat_anterior) {
            return falha(logger, ErroBase::ForaDeOrdem);
        }
        lat_anterior = lat_e;
    }

    if (logger != nullptr) {
        char msg[64];
        std::snprintf(msg, sizeof msg, "%u pontos carregados",
                      static_cast<unsigned>(reais));
        logger->info(kOrigem, msg);
    }
    return {ErroBase::Nenhum, reais};
}

}  // namespace coruja
