paulovitorbal/coruja_gps/firmware/src/nucleo/BaseRadares.h

#pragma once
#include <cstddef>
#include <cstdint>

#include "nucleo/Crc32.h"
#include "nucleo/Ponto.h"

namespace coruja {

class Logger;

/// Por que a base falhou a carga. O firmware precisa distinguir estes casos
/// porque o RF07 exige mensagens diferentes: cartao ausente o motorista
/// resolve inserindo o cartao, base corrompida ele nao resolve dirigindo.
enum class ErroBase {
    Nenhum,
    TamanhoInvalido,   ///< menor que o cabecalho, ou nao multiplo do registro
    MagicInvalido,
    VersaoInvalida,
    EscalaInvalida,
    TamRegistroInvalido,
    BaseVazia,              ///< n_pontos == 0; a especificacao recusa
    ExcedeuTeto,            ///< acima de kTetoPontos: estouraria a RAM
    ContagemInconsistente,  ///< cabecalho e tamanho do arquivo discordam
    ExcedeuCapacidade,      ///< mais pontos do que o destino aguenta
    CrcInvalido,
    ForaDeOrdem,            ///< nao esta ordenado por latitude
    RegistroInvalido,       ///< TYPE ou DirType fora do dominio
};

const char* descreve(ErroBase erro);

/// Resultado da carga. `pontos` sempre e zero em caso de erro: a base e
/// carregada por inteiro ou nao e carregada — nao existe base parcial, porque
/// um alerta que falta e pior que nenhum alerta.
struct ResultadoCarga {
    ErroBase    erro   = ErroBase::Nenhum;
    std::size_t pontos = 0;
    bool ok() const { return erro == ErroBase::Nenhum; }
};

/// Layout do `radares.bin`, espelhando formato_dados.md §2.
/// Cabecalho de 16 B: magic[4] | versao u16 | exp_escala u8 | tam_registro u8 |
/// n_pontos u32 | crc32 u32. Equivale ao `<4sHBBII` do `formato_radares.py`,
/// que e o contrato compartilhado entre conversor e firmware.
constexpr std::uint32_t kMagic          = 0x31524452U;  // "RDR1" little-endian

/// Versao 2 desde 2026-09-30: o cabecalho ganhou a DATA da base.
///
/// Os 16 primeiros bytes sao identicos aos da versao 1 -- so `versao` muda.
/// A data entrou DEPOIS do CRC de proposito: um campo no meio deslocaria o
/// `crc32`, e um leitor antigo leria o CRC de outro lugar sem perceber.
constexpr std::uint16_t kVersao         = 2;
/// A versao anterior continua ACEITA na leitura. Um cartao com base v1 vale,
/// e o aparelho so fica sem a data para mostrar -- recusa-la deixaria o
/// aparelho sem base ate a proxima atualizacao, o que e muito pior que uma
/// linha vazia na tela de informacao.
constexpr std::uint16_t kVersaoSemData  = 1;

constexpr std::uint8_t  kExpoenteEscala = 5;
constexpr float         kEscala         = 100000.0F;
constexpr std::size_t   kTamCabecalho        = 20;
constexpr std::size_t   kTamCabecalhoSemData = 16;
constexpr std::size_t   kTamRegistro    = 12;

/// O ponto em RAM e o registro em arquivo tem de ter o mesmo tamanho. Nao e
/// coincidencia nem conveniencia: o orcamento de memoria do `formato_dados.md`
/// §1 foi calculado sobre 12 B por ponto, e padding silencioso de alinhamento
/// ja custou 71 KiB uma vez. O compilador guarda esse invariante agora.
static_assert(sizeof(Ponto) == kTamRegistro,
              "Ponto cresceu por padding: ver docs/adr/0006");

/// Teto do **formato**: acima disto o arquivo e absurdo e deve ser recusado
/// como corrompido (formato_dados.md §2). Nao e o que o firmware reserva.
constexpr std::uint32_t kTetoPontos = 40000;

/// Capacidade que o **firmware** reserva estaticamente em `.bss`.
///
/// Confundir os dois foi um erro real: dimensionar o array pelo teto de
/// formato reserva 468,75 KiB e deixa so 48 KiB livres dos 520 KiB — medido no
/// linker, nao estimado. Nao sobra para lwIP, stacks e as bandas do display.
///
/// O orcamento do `formato_dados.md` §1 deixa 355 KiB para a base, ou ~30.300
/// pontos. Reservar 24.000 da **31% de folga** sobre os 18.294 de hoje e ainda
/// sobram ~134 KiB. Um arquivo entre 24.000 e 40.000 pontos e valido pelo
/// formato e recusado por este firmware com `ExcedeuCapacidade`, que e a
/// distincao correta: o arquivo nao esta corrompido, esta grande demais para
/// esta placa. Ver `docs/adr/0006`.
constexpr std::uint32_t kCapacidadeFirmware = 24000;

static_assert(kCapacidadeFirmware <= kTetoPontos,
              "a capacidade do firmware nao pode passar do teto do formato");
static_assert(kCapacidadeFirmware * sizeof(Ponto) < 355u * 1024u,
              "a base estourou a fatia de 355 KiB do orcamento do §1");

/// Decodifica um arquivo `radares.bin` ja em memoria para um vetor de `Ponto`.
///
/// Nao le do cartao: recebe os bytes crus. Essa separacao e o que permite
/// testar a validacao inteira no host, contra o arquivo real de 18.294 pontos,
/// sem SD e sem Pico.
///
/// Valida, na ordem: tamanho, magic, versao, escala, contagem, capacidade,
/// CRC-32, ordenacao por latitude e o dominio de cada registro. Mesma ordem e
/// mesmos critérios do `formato_radares.py`, que e o contrato compartilhado.
/// Decodifica **um** registro de 12 B e valida o domínio de `TipoPonto` e
/// `Sentido`. Devolve `false` se algum estiver fora — o registro não é escrito.
///
/// `lat_bruta` recebe a latitude ainda em inteiro escalado, que é como a
/// ordenação tem de ser comparada: converter para `float` antes de comparar
/// introduziria empates que o arquivo não tem.
///
/// Existe extraída porque **dois** caminhos decodificam registros: a carga a
/// partir de um buffer e a carga em fluxo do cartão. Duplicar isto seria
/// duplicar a validação de domínio, e um dos dois envelheceria.
bool decodifica_registro(const std::uint8_t* registro, Ponto* destino,
                         std::int32_t* lat_bruta);

ResultadoCarga carrega_base(const std::uint8_t* bytes, std::size_t tamanho,
                            Ponto* destino, std::size_t capacidade,
                            Logger* logger = nullptr);

}  // namespace coruja
