paulovitorbal/coruja_gps/firmware/src/display/PainelSt7789.h

#pragma once
#include <cstddef>
#include <cstdint>

namespace coruja {

/// Driver do painel ST7789V do `GMT024-08-SPI8P ver. 1.3` (R-62).
///
/// Camada baixa: janela e pixels, sem texto nem icone. O `Visor` completo
/// vem por cima disto quando as fontes existirem; separar permite ligar e
/// conferir o painel antes de ter um unico glifo desenhado.
///
/// **O modulo nao tem MISO** (R-62). Nada pode ser lido de volta: nem o
/// registrador de ID, nem o estado do controlador, nem se um comando foi
/// aceito. Toda escrita aqui e cega, e a unica verificacao possivel e
/// **olhar a tela**. E por isso que o `bancada_display` existe.
///
/// O painel e 240x320 em retrato; o firmware usa 320x240 deitado
/// (`Visor.h`), o que se obtem por MADCTL na inicializacao -- nao e um
/// painel nativo em paisagem.
/// Clock do SPI do display: **16 MHz, medidos e não supostos.**
///
/// A varredura da bancada mostrou desenho limpo até 25 MHz efetivos nesta
/// protoboard (autor, 2026-09-29); 16 deixa margem para variação de
/// temperatura e de contato.
///
/// Os 4 MHz que estavam aqui antes eram conservadorismo caro. Cada passo de
/// rolagem redesenha uma linha de texto — 320 × 20 px, 12.800 bytes — e a
/// 4 MHz isso é **25,6 ms de SPI bloqueante**, mais que a folga inteira de
/// 5,75 ms que a decodificação do encoder tem no estado `(0,0)` (R-36). A
/// 16 MHz cai para 6,4 ms, e com rolagem por caractere (4 passos/s) o custo
/// total fica em 3% do barramento.
///
/// O número é do **meio físico**, não do chip: o ST7789V aceita ~66 MHz,
/// protoboard com fio jumper não. Foi por confundir os dois que a primeira
/// versão saiu com 62,5 MHz.
constexpr std::uint32_t kBaudDisplayHz = 16000000;
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
